railyai/raily-pin/published/keyring/case-3d/v2/bambu/stats.md

# Slice stats per plate (case v2)

Bambu Studio 02.06.00.51 CLI, system presets, 0.16 mm layers, Panchroma Matte (density 1.37). Grams come from the G-code extrusion: *part* = model + support, *purge* = the flush at each colour change + the prime tower (P2S and H2S flush in firmware, `M620.10`: their purge is the slicer's filament total minus the G-code extrusion). Times are the slicer estimate. Generated by `build_bambu.py stats`.

## X1 Carbon / X1E / X1

| Project | Plate | Time | Colour changes | White, part | Periwinkle, part | Support (in the part grams) | Purge | Total |
| --- | --- | --- | --- | --- | --- | --- | --- | --- |
| v1 | 1. LED coupon (print first) | 0 h 13 m | 0 | 0.0 g | 1.5 g | 0.0 g | 0.0 g | 2.0 g |
| v1 | 2. V1 case A (screws): tray + shelf | 0 h 59 m | 0 | 18.7 g | 0.0 g | 0.4 g | 0.0 g | 19.2 g |
| v1 | 3. V1 case A (screws): cover | 1 h 21 m | 0 | 0.0 g | 23.7 g | 11.4 g | 0.0 g | 24.2 g |
| v1 | 4. V1 case B (snap-fit): tray + shelf | 1 h 03 m | 0 | 18.9 g | 0.0 g | 0.4 g | 0.0 g | 19.4 g |
| v1 | 5. V1 case B (snap-fit): cover | 1 h 21 m | 0 | 0.0 g | 23.8 g | 11.3 g | 0.0 g | 24.3 g |
| v5 | 1. LED coupon (print first) | 0 h 13 m | 0 | 0.0 g | 1.5 g | 0.0 g | 0.0 g | 2.0 g |
| v5 | 2. V5 case A (screws): tray + shelf | 2 h 15 m | 50 | 19.5 g | 1.9 g | 0.4 g | 14.9 g | 36.7 g |
| v5 | 3. V5 case A (screws): cover | 1 h 21 m | 0 | 0.0 g | 23.7 g | 11.4 g | 0.0 g | 24.2 g |
| v5 | 4. V5 case B (snap-fit): tray + shelf | 2 h 17 m | 50 | 19.7 g | 1.9 g | 0.4 g | 14.9 g | 36.9 g |
| v5 | 5. V5 case B (snap-fit): cover | 1 h 21 m | 0 | 0.0 g | 23.8 g | 11.3 g | 0.0 g | 24.3 g |
| v5-batch | 1. V5 5 trays + 5 shelves (A) | 5 h 55 m | 50 | 91.0 g | 2.7 g | 2.2 g | 21.3 g | 115.5 g |
| v5-batch | 2. V5 5 covers (A) | 6 h 08 m | 0 | 0.0 g | 118.6 g | 56.9 g | 0.0 g | 119.1 g |
| v1-noams | 1. White: tray + shelf (A) | 0 h 59 m | 0 | 18.7 g | 0.0 g | 0.4 g | 0.0 g | 19.2 g |
| v1-noams | 2. Periwinkle: cover (A) | 1 h 21 m | 0 | 0.0 g | 23.7 g | 11.4 g | 0.0 g | 24.2 g |
| v1-noams | 3. White: tray + shelf (B) | 1 h 02 m | 0 | 18.9 g | 0.0 g | 0.4 g | 0.0 g | 19.4 g |
| v1-noams | 4. Periwinkle: cover (B) | 1 h 21 m | 0 | 0.0 g | 23.8 g | 11.3 g | 0.0 g | 24.3 g |

## P1S

| Project | Plate | Time | Colour changes | White, part | Periwinkle, part | Support (in the part grams) | Purge | Total |
| --- | --- | --- | --- | --- | --- | --- | --- | --- |
| v1 | 1. LED coupon (print first) | 0 h 11 m | 0 | 0.0 g | 1.5 g | 0.0 g | 0.0 g | 1.8 g |
| v1 | 2. V1 case A (screws): tray + shelf | 0 h 57 m | 0 | 18.7 g | 0.0 g | 0.4 g | 0.0 g | 19.1 g |
| v1 | 3. V1 case A (screws): cover | 1 h 18 m | 0 | 0.0 g | 23.7 g | 11.4 g | 0.0 g | 24.1 g |
| v1 | 4. V1 case B (snap-fit): tray + shelf | 1 h 00 m | 0 | 18.9 g | 0.0 g | 0.4 g | 0.0 g | 19.3 g |
| v1 | 5. V1 case B (snap-fit): cover | 1 h 19 m | 0 | 0.0 g | 23.8 g | 11.3 g | 0.0 g | 24.2 g |
| v5 | 1. LED coupon (print first) | 0 h 11 m | 0 | 0.0 g | 1.5 g | 0.0 g | 0.0 g | 1.8 g |
| v5 | 2. V5 case A (screws): tray + shelf | 2 h 13 m | 50 | 19.5 g | 1.9 g | 0.4 g | 14.9 g | 36.6 g |
| v5 | 3. V5 case A (screws): cover | 1 h 18 m | 0 | 0.0 g | 23.7 g | 11.4 g | 0.0 g | 24.1 g |
| v5 | 4. V5 case B (snap-fit): tray + shelf | 2 h 15 m | 50 | 19.7 g | 1.9 g | 0.4 g | 14.9 g | 36.8 g |
| v5 | 5. V5 case B (snap-fit): cover | 1 h 19 m | 0 | 0.0 g | 23.8 g | 11.3 g | 0.0 g | 24.2 g |
| v5-batch | 1. V5 5 trays + 5 shelves (A) | 5 h 53 m | 50 | 91.0 g | 2.7 g | 2.2 g | 21.3 g | 115.3 g |
| v5-batch | 2. V5 5 covers (A) | 6 h 05 m | 0 | 0.0 g | 118.6 g | 56.9 g | 0.0 g | 118.9 g |
| v1-noams | 1. White: tray + shelf (A) | 0 h 57 m | 0 | 18.7 g | 0.0 g | 0.4 g | 0.0 g | 19.1 g |
| v1-noams | 2. Periwinkle: cover (A) | 1 h 18 m | 0 | 0.0 g | 23.7 g | 11.4 g | 0.0 g | 24.1 g |
| v1-noams | 3. White: tray + shelf (B) | 1 h 00 m | 0 | 18.9 g | 0.0 g | 0.4 g | 0.0 g | 19.3 g |
| v1-noams | 4. Periwinkle: cover (B) | 1 h 19 m | 0 | 0.0 g | 23.8 g | 11.3 g | 0.0 g | 24.2 g |

## P1P

| Project | Plate | Time | Colour changes | White, part | Periwinkle, part | Support (in the part grams) | Purge | Total |
| --- | --- | --- | --- | --- | --- | --- | --- | --- |
| v1 | 1. LED coupon (print first) | 0 h 11 m | 0 | 0.0 g | 1.5 g | 0.0 g | 0.0 g | 1.8 g |
| v1 | 2. V1 case A (screws): tray + shelf | 0 h 58 m | 0 | 18.7 g | 0.0 g | 0.4 g | 0.0 g | 19.1 g |
| v1 | 3. V1 case A (screws): cover | 1 h 19 m | 0 | 0.0 g | 23.7 g | 11.4 g | 0.0 g | 24.1 g |
| v1 | 4. V1 case B (snap-fit): tray + shelf | 1 h 01 m | 0 | 18.9 g | 0.0 g | 0.4 g | 0.0 g | 19.3 g |
| v1 | 5. V1 case B (snap-fit): cover | 1 h 19 m | 0 | 0.0 g | 23.8 g | 11.3 g | 0.0 g | 24.2 g |
| v5 | 1. LED coupon (print first) | 0 h 11 m | 0 | 0.0 g | 1.5 g | 0.0 g | 0.0 g | 1.8 g |
| v5 | 2. V5 case A (screws): tray + shelf | 2 h 14 m | 50 | 19.5 g | 1.9 g | 0.4 g | 14.9 g | 36.6 g |
| v5 | 3. V5 case A (screws): cover | 1 h 19 m | 0 | 0.0 g | 23.7 g | 11.4 g | 0.0 g | 24.1 g |
| v5 | 4. V5 case B (snap-fit): tray + shelf | 2 h 16 m | 50 | 19.7 g | 1.9 g | 0.4 g | 14.9 g | 36.8 g |
| v5 | 5. V5 case B (snap-fit): cover | 1 h 19 m | 0 | 0.0 g | 23.8 g | 11.3 g | 0.0 g | 24.2 g |
| v5-batch | 1. V5 5 trays + 5 shelves (A) | 5 h 53 m | 50 | 91.0 g | 2.7 g | 2.2 g | 21.3 g | 115.3 g |
| v5-batch | 2. V5 5 covers (A) | 6 h 05 m | 0 | 0.0 g | 118.6 g | 56.9 g | 0.0 g | 118.9 g |
| v1-noams | 1. White: tray + shelf (A) | 0 h 58 m | 0 | 18.7 g | 0.0 g | 0.4 g | 0.0 g | 19.1 g |
| v1-noams | 2. Periwinkle: cover (A) | 1 h 19 m | 0 | 0.0 g | 23.7 g | 11.4 g | 0.0 g | 24.1 g |
| v1-noams | 3. White: tray + shelf (B) | 1 h 01 m | 0 | 18.9 g | 0.0 g | 0.4 g | 0.0 g | 19.3 g |
| v1-noams | 4. Periwinkle: cover (B) | 1 h 19 m | 0 | 0.0 g | 23.8 g | 11.3 g | 0.0 g | 24.2 g |

## P2S

| Project | Plate | Time | Colour changes | White, part | Periwinkle, part | Support (in the part grams) | Purge | Total |
| --- | --- | --- | --- | --- | --- | --- | --- | --- |
| v1 | 1. LED coupon (print first) | 0 h 11 m | 0 | 0.0 g | 1.6 g | 0.0 g | 0.0 g | 1.6 g |
| v1 | 2. V1 case A (screws) | 2 h 13 m | 2 | 19.3 g | 24.5 g | 12.2 g | 0.7 g | 44.5 g |
| v1 | 3. V1 case B (snap-fit) | 2 h 16 m | 2 | 19.5 g | 24.6 g | 12.1 g | 0.7 g | 44.8 g |
| v5 | 1. LED coupon (print first) | 0 h 11 m | 0 | 0.0 g | 1.6 g | 0.0 g | 0.0 g | 1.6 g |
| v5 | 2. V5 case A (screws) | 3 h 19 m | 52 | 18.7 g | 25.0 g | 12.2 g | 18.4 g | 62.2 g |
| v5 | 3. V5 case B (snap-fit) | 3 h 22 m | 52 | 18.9 g | 25.1 g | 12.1 g | 18.4 g | 62.5 g |
| v5-batch | 1. V5 5 trays + 5 shelves (A) | 5 h 44 m | 50 | 93.8 g | 2.8 g | 2.2 g | 21.3 g | 117.8 g |
| v5-batch | 2. V5 5 covers (A) | 6 h 07 m | 0 | 0.0 g | 122.2 g | 58.6 g | 0.0 g | 122.3 g |
| v1-noams | 1. White: tray + shelf (A) | 0 h 58 m | 0 | 19.3 g | 0.0 g | 0.5 g | 0.0 g | 19.3 g |
| v1-noams | 2. Periwinkle: cover (A) | 1 h 19 m | 0 | 0.0 g | 24.5 g | 11.7 g | 0.0 g | 24.5 g |
| v1-noams | 3. White: tray + shelf (B) | 1 h 01 m | 0 | 19.5 g | 0.0 g | 0.5 g | 0.0 g | 19.6 g |
| v1-noams | 4. Periwinkle: cover (B) | 1 h 19 m | 0 | 0.0 g | 24.6 g | 11.6 g | 0.0 g | 24.6 g |

## A1

| Project | Plate | Time | Colour changes | White, part | Periwinkle, part | Support (in the part grams) | Purge | Total |
| --- | --- | --- | --- | --- | --- | --- | --- | --- |
| v1 | 1. LED coupon (print first) | 0 h 12 m | 0 | 0.0 g | 1.5 g | 0.0 g | 0.0 g | 1.9 g |
| v1 | 2. V1 case A (screws) | 2 h 14 m | 2 | 18.8 g | 23.8 g | 11.8 g | 0.4 g | 43.4 g |
| v1 | 3. V1 case B (snap-fit) | 2 h 17 m | 2 | 19.0 g | 23.9 g | 11.7 g | 0.4 g | 43.7 g |
| v5 | 1. LED coupon (print first) | 0 h 12 m | 0 | 0.0 g | 1.5 g | 0.0 g | 0.0 g | 1.9 g |
| v5 | 2. V5 case A (screws) | 3 h 24 m | 52 | 19.9 g | 26.0 g | 11.8 g | 11.1 g | 57.4 g |
| v5 | 3. V5 case B (snap-fit) | 3 h 26 m | 52 | 20.1 g | 26.1 g | 11.7 g | 11.1 g | 57.7 g |
| v5-batch | 1. V5 5 trays + 5 shelves (A) | 5 h 56 m | 50 | 91.0 g | 2.6 g | 2.2 g | 19.1 g | 113.1 g |
| v5-batch | 2. V5 5 covers (A) | 6 h 14 m | 0 | 0.0 g | 118.6 g | 56.9 g | 0.0 g | 119.0 g |
| v1-noams | 1. White: tray + shelf (A) | 0 h 59 m | 0 | 18.7 g | 0.0 g | 0.4 g | 0.0 g | 19.1 g |
| v1-noams | 2. Periwinkle: cover (A) | 1 h 19 m | 0 | 0.0 g | 23.7 g | 11.4 g | 0.0 g | 24.1 g |
| v1-noams | 3. White: tray + shelf (B) | 1 h 02 m | 0 | 18.9 g | 0.0 g | 0.4 g | 0.0 g | 19.3 g |
| v1-noams | 4. Periwinkle: cover (B) | 1 h 20 m | 0 | 0.0 g | 23.8 g | 11.3 g | 0.0 g | 24.2 g |

## A1 mini

| Project | Plate | Time | Colour changes | White, part | Periwinkle, part | Support (in the part grams) | Purge | Total |
| --- | --- | --- | --- | --- | --- | --- | --- | --- |
| v1 | 1. LED coupon (print first) | 0 h 11 m | 0 | 0.0 g | 1.5 g | 0.0 g | 0.0 g | 1.9 g |
| v1 | 2. V1 case A (screws): tray + shelf | 0 h 59 m | 0 | 18.7 g | 0.0 g | 0.4 g | 0.0 g | 19.1 g |
| v1 | 3. V1 case A (screws): cover | 1 h 22 m | 0 | 0.0 g | 23.7 g | 11.4 g | 0.0 g | 24.1 g |
| v1 | 4. V1 case B (snap-fit): tray + shelf | 1 h 03 m | 0 | 18.9 g | 0.0 g | 0.4 g | 0.0 g | 19.3 g |
| v1 | 5. V1 case B (snap-fit): cover | 1 h 22 m | 0 | 0.0 g | 23.8 g | 11.3 g | 0.0 g | 24.2 g |
| v5 | 1. LED coupon (print first) | 0 h 11 m | 0 | 0.0 g | 1.5 g | 0.0 g | 0.0 g | 1.9 g |
| v5 | 2. V5 case A (screws): tray + shelf | 2 h 18 m | 50 | 19.8 g | 2.1 g | 0.4 g | 10.7 g | 32.9 g |
| v5 | 3. V5 case A (screws): cover | 1 h 22 m | 0 | 0.0 g | 23.7 g | 11.4 g | 0.0 g | 24.1 g |
| v5 | 4. V5 case B (snap-fit): tray + shelf | 2 h 20 m | 50 | 20.0 g | 2.1 g | 0.4 g | 10.7 g | 33.1 g |
| v5 | 5. V5 case B (snap-fit): cover | 1 h 22 m | 0 | 0.0 g | 23.8 g | 11.3 g | 0.0 g | 24.2 g |
| v5-batch | 1. V5 3 trays + 3 shelves (A) | 4 h 24 m | 50 | 54.6 g | 1.5 g | 1.3 g | 19.2 g | 75.7 g |
| v5-batch | 2. V5 3 covers (A) | 3 h 55 m | 0 | 0.0 g | 71.2 g | 34.1 g | 0.0 g | 71.5 g |
| v1-noams | 1. White: tray + shelf (A) | 0 h 59 m | 0 | 18.7 g | 0.0 g | 0.4 g | 0.0 g | 19.1 g |
| v1-noams | 2. Periwinkle: cover (A) | 1 h 22 m | 0 | 0.0 g | 23.7 g | 11.4 g | 0.0 g | 24.1 g |
| v1-noams | 3. White: tray + shelf (B) | 1 h 03 m | 0 | 18.9 g | 0.0 g | 0.4 g | 0.0 g | 19.3 g |
| v1-noams | 4. Periwinkle: cover (B) | 1 h 22 m | 0 | 0.0 g | 23.8 g | 11.3 g | 0.0 g | 24.2 g |

## H2D

| Project | Plate | Time | Colour changes | White, part | Periwinkle, part | Support (in the part grams) | Purge | Total |
| --- | --- | --- | --- | --- | --- | --- | --- | --- |
| v1 | 1. LED coupon (print first) | 0 h 10 m | 0 | 0.0 g | 1.5 g | 0.0 g | 0.0 g | 1.7 g |
| v1 | 2. V1 case A (screws) | 2 h 12 m | 0 | 18.7 g | 23.7 g | 11.8 g | 0.0 g | 42.6 g |
| v1 | 3. V1 case B (snap-fit) | 2 h 15 m | 0 | 18.9 g | 23.8 g | 11.7 g | 0.0 g | 42.9 g |
| v5 | 1. LED coupon (print first) | 0 h 10 m | 0 | 0.0 g | 1.5 g | 0.0 g | 0.0 g | 1.7 g |
| v5 | 2. V5 case A (screws) | 2 h 19 m | 0 | 18.2 g | 24.3 g | 11.8 g | 0.0 g | 42.6 g |
| v5 | 3. V5 case B (snap-fit) | 2 h 22 m | 0 | 18.4 g | 24.4 g | 11.7 g | 0.0 g | 42.9 g |
| v5-batch | 1. V5 5 trays + 5 shelves (A) | 4 h 53 m | 0 | 90.9 g | 2.7 g | 2.2 g | 4.0 g | 97.8 g |
| v5-batch | 2. V5 5 covers (A) | 6 h 11 m | 0 | 0.0 g | 118.6 g | 56.9 g | 0.0 g | 118.8 g |
| v1-noams | 1. White: tray + shelf (A) | 0 h 58 m | 0 | 18.7 g | 0.0 g | 0.4 g | 0.0 g | 18.9 g |
| v1-noams | 2. Periwinkle: cover (A) | 1 h 19 m | 0 | 0.0 g | 23.7 g | 11.4 g | 0.0 g | 23.9 g |
| v1-noams | 3. White: tray + shelf (B) | 1 h 01 m | 0 | 18.9 g | 0.0 g | 0.4 g | 0.0 g | 19.1 g |
| v1-noams | 4. Periwinkle: cover (B) | 1 h 19 m | 0 | 0.0 g | 23.8 g | 11.3 g | 0.0 g | 24.0 g |

## H2S

| Project | Plate | Time | Colour changes | White, part | Periwinkle, part | Support (in the part grams) | Purge | Total |
| --- | --- | --- | --- | --- | --- | --- | --- | --- |
| v1 | 1. LED coupon (print first) | 0 h 10 m | 0 | 0.0 g | 1.5 g | 0.0 g | 0.0 g | 1.7 g |
| v1 | 2. V1 case A (screws) | 2 h 11 m | 2 | 18.7 g | 23.7 g | 11.8 g | 0.6 g | 43.3 g |
| v1 | 3. V1 case B (snap-fit) | 2 h 15 m | 2 | 18.9 g | 23.8 g | 11.7 g | 0.7 g | 43.6 g |
| v5 | 1. LED coupon (print first) | 0 h 10 m | 0 | 0.0 g | 1.5 g | 0.0 g | 0.0 g | 1.7 g |
| v5 | 2. V5 case A (screws) | 3 h 17 m | 52 | 18.2 g | 24.3 g | 11.8 g | 20.8 g | 63.5 g |
| v5 | 3. V5 case B (snap-fit) | 3 h 20 m | 52 | 18.4 g | 24.4 g | 11.7 g | 20.8 g | 63.8 g |
| v5-batch | 1. V5 5 trays + 5 shelves (A) | 5 h 42 m | 50 | 91.0 g | 2.7 g | 2.2 g | 22.2 g | 116.1 g |
| v5-batch | 2. V5 5 covers (A) | 6 h 06 m | 0 | 0.0 g | 118.6 g | 56.9 g | 0.0 g | 118.8 g |
| v1-noams | 1. White: tray + shelf (A) | 0 h 56 m | 0 | 18.7 g | 0.0 g | 0.4 g | 0.0 g | 18.9 g |
| v1-noams | 2. Periwinkle: cover (A) | 1 h 18 m | 0 | 0.0 g | 23.7 g | 11.4 g | 0.0 g | 23.9 g |
| v1-noams | 3. White: tray + shelf (B) | 1 h 00 m | 0 | 18.9 g | 0.0 g | 0.4 g | 0.0 g | 19.2 g |
| v1-noams | 4. Periwinkle: cover (B) | 1 h 18 m | 0 | 0.0 g | 23.8 g | 11.3 g | 0.0 g | 24.0 g |
