railyai/raily-pin/guide/art/overview-fill.png

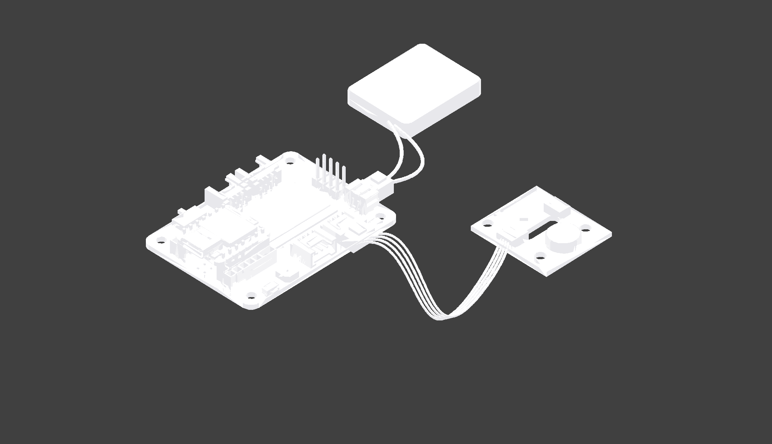
guide/art/overview-fill.png
