railyai/raily-pin/published/keyring/case-3d/bambu/preview/a1m-v5-batch-plate1.png

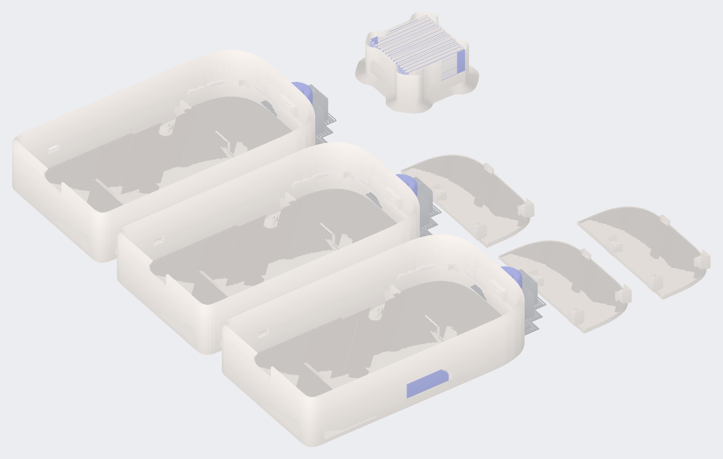
published/keyring/case-3d/bambu/preview/a1m-v5-batch-plate1.png
