railyai/raily-pin/published/keyring/case-3d/bambu/preview/h2d-v5-plate2.png

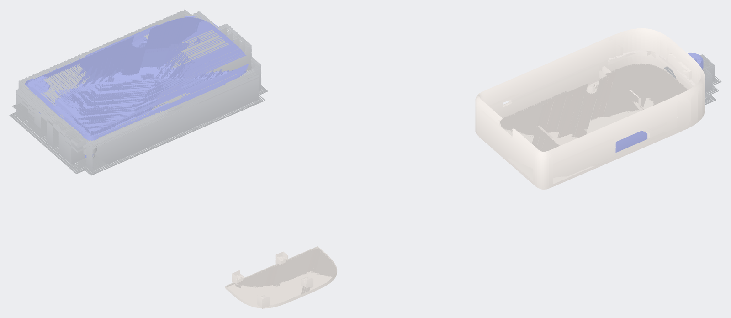
published/keyring/case-3d/bambu/preview/h2d-v5-plate2.png
