railyai/raily-pin/published/keyring/case-3d/bambu/preview/v1-plate1.png

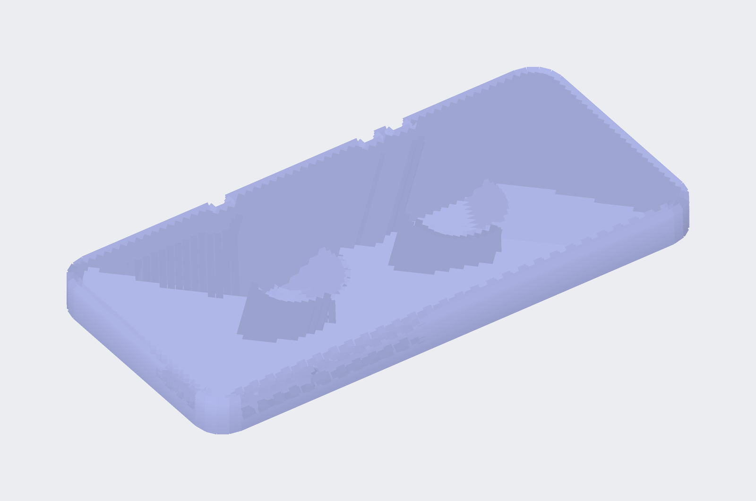
published/keyring/case-3d/bambu/preview/v1-plate1.png
