railyai/raily-pin/published/keyring/case-3d/v2/bambu/preview/a1m-v1-noams-plate2.png

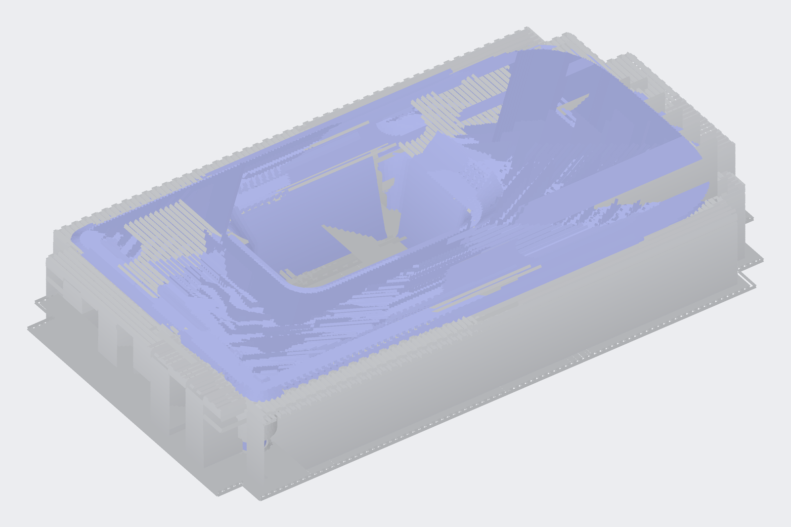
published/keyring/case-3d/v2/bambu/preview/a1m-v1-noams-plate2.png
