railyai/raily-pin/published/keyring/case-3d/v2/line-art/case-v2-iso.png

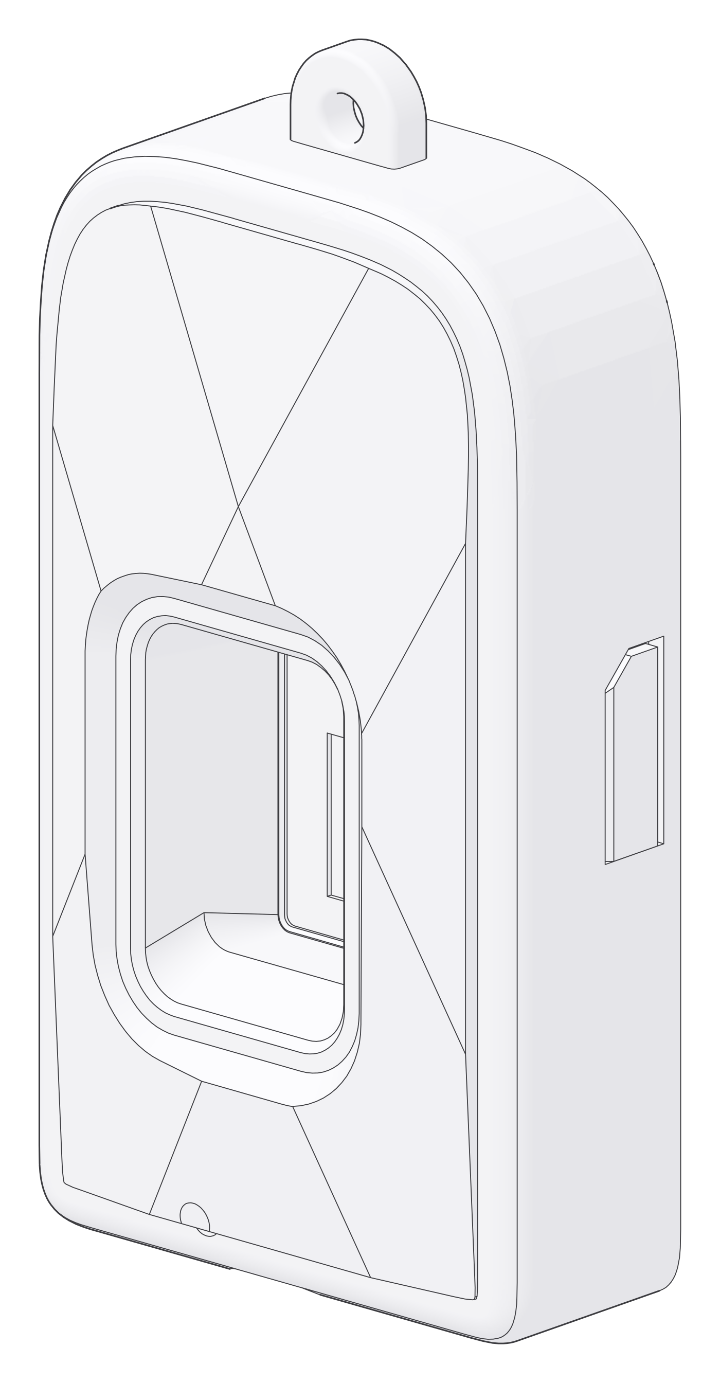
published/keyring/case-3d/v2/line-art/case-v2-iso.png
