railyai/raily-pin/published/keyring/case-3d/v2/line-art/case-v2-window-across.png

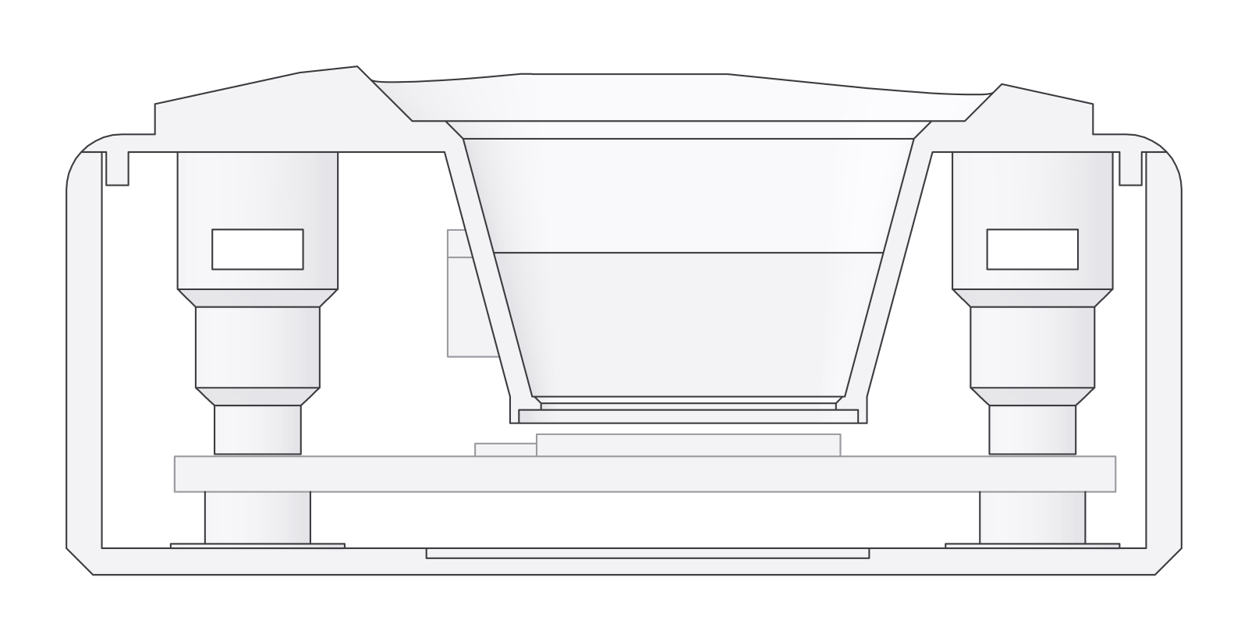
published/keyring/case-3d/v2/line-art/case-v2-window-across.png
