railyai/raily-pin/published/keyring/case-3d/v2/line-art/tab-v2-across.png

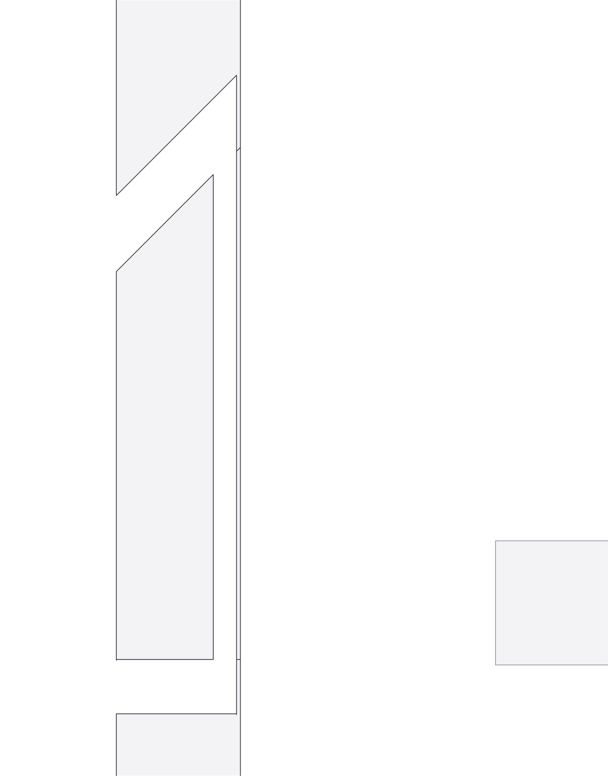
published/keyring/case-3d/v2/line-art/tab-v2-across.png
