railyai/raily-pin/published/keyring/case-3d/v2/line-art/usb-v2-usb-end.png

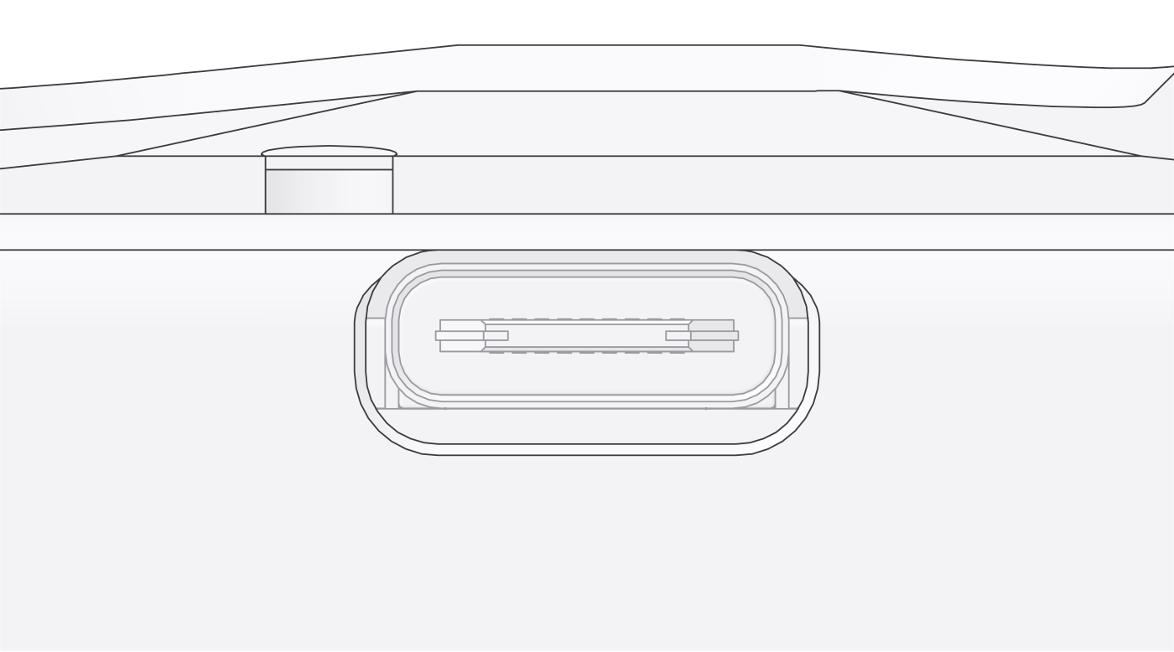
published/keyring/case-3d/v2/line-art/usb-v2-usb-end.png
