railyai/raily-pin/published/keyring/case-3d/v2/renders/render-v2-v1-front.png

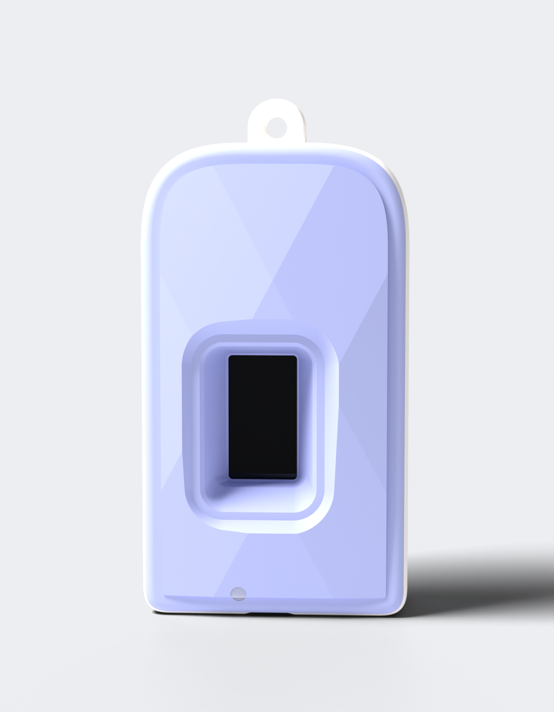
published/keyring/case-3d/v2/renders/render-v2-v1-front.png
