railyai/raily-pin/published/keyring/case/guide-figures/overview.png

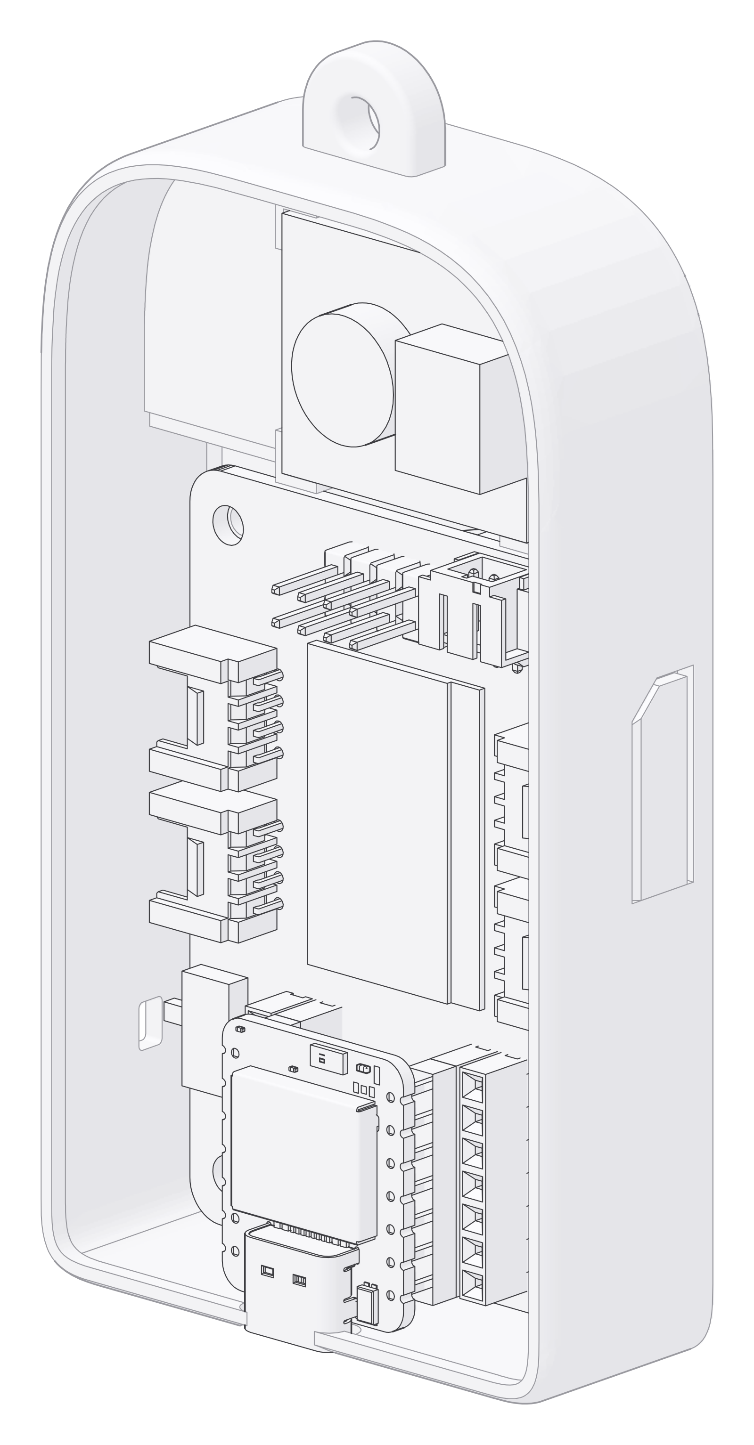
published/keyring/case/guide-figures/overview.png
