railyai/raily-pin/published/keyring/case/line-art/case-front.png

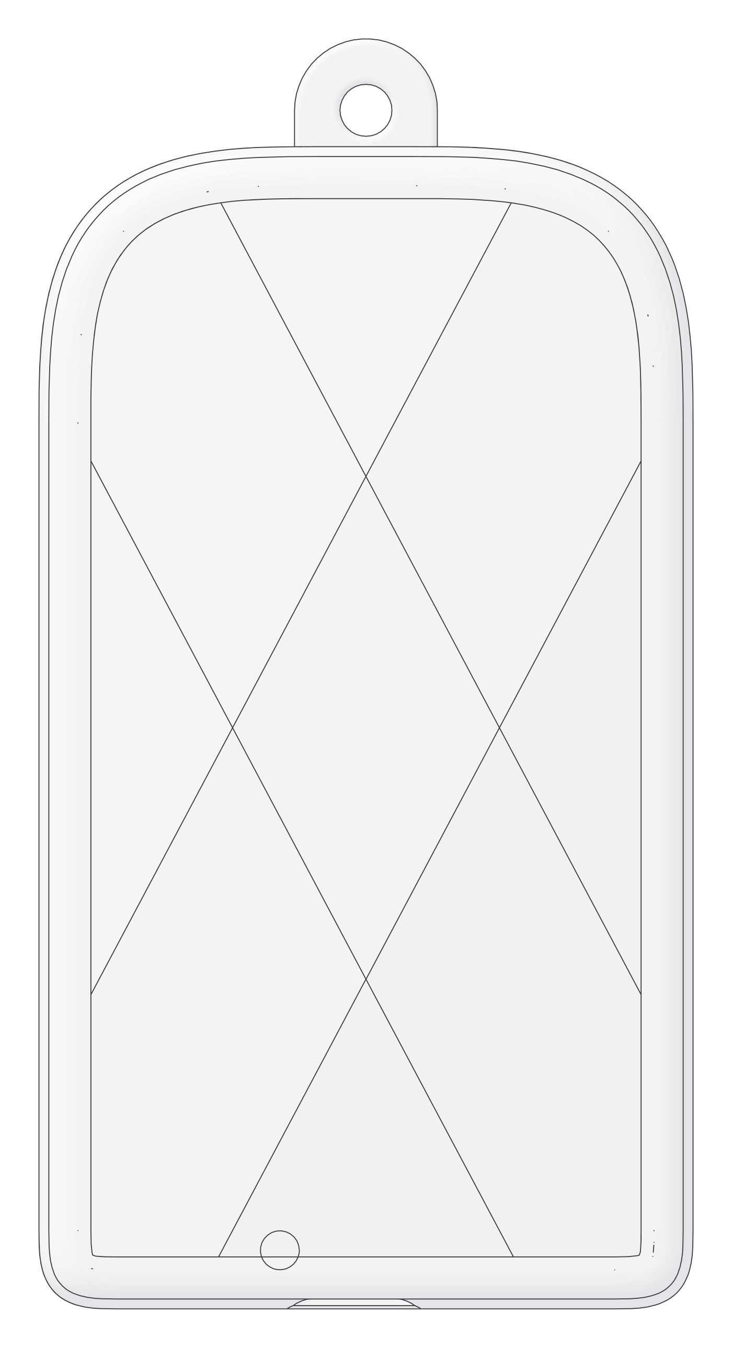
published/keyring/case/line-art/case-front.png
