railyai/raily-pin/published/keyring/case/line-art/case-iso.png

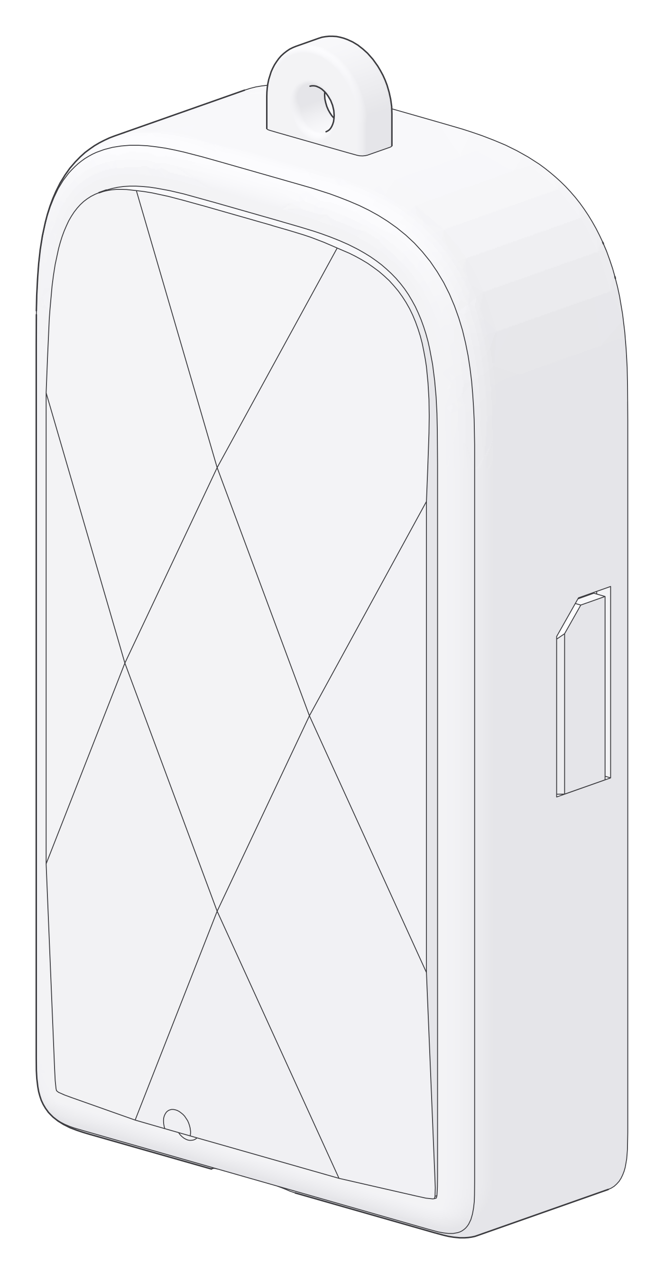
published/keyring/case/line-art/case-iso.png
