railyai/raily-pin/published/keyring/case/line-art/tab-across-nub.png

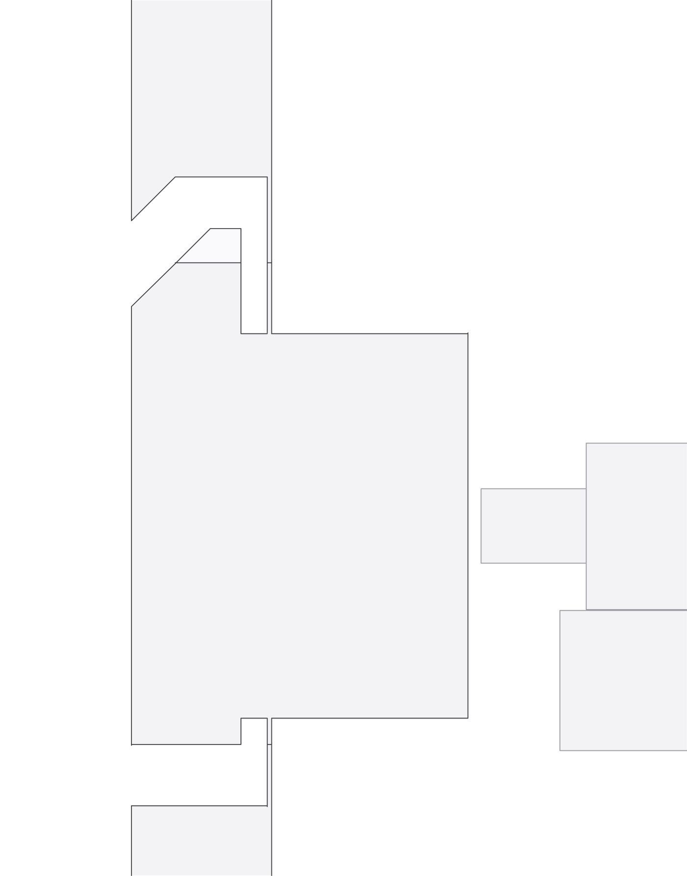
published/keyring/case/line-art/tab-across-nub.png
