railyai/raily-pin/published/keyring/case/line-art/tab-before-after.png

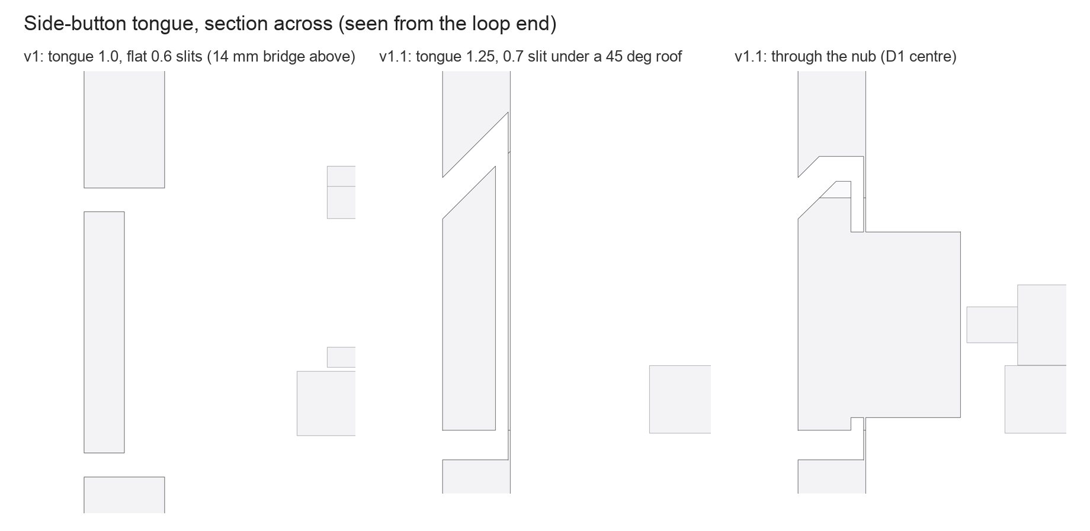
published/keyring/case/line-art/tab-before-after.png
