railyai/raily-pin/published/keyring/case/line-art/usb-before-after.png

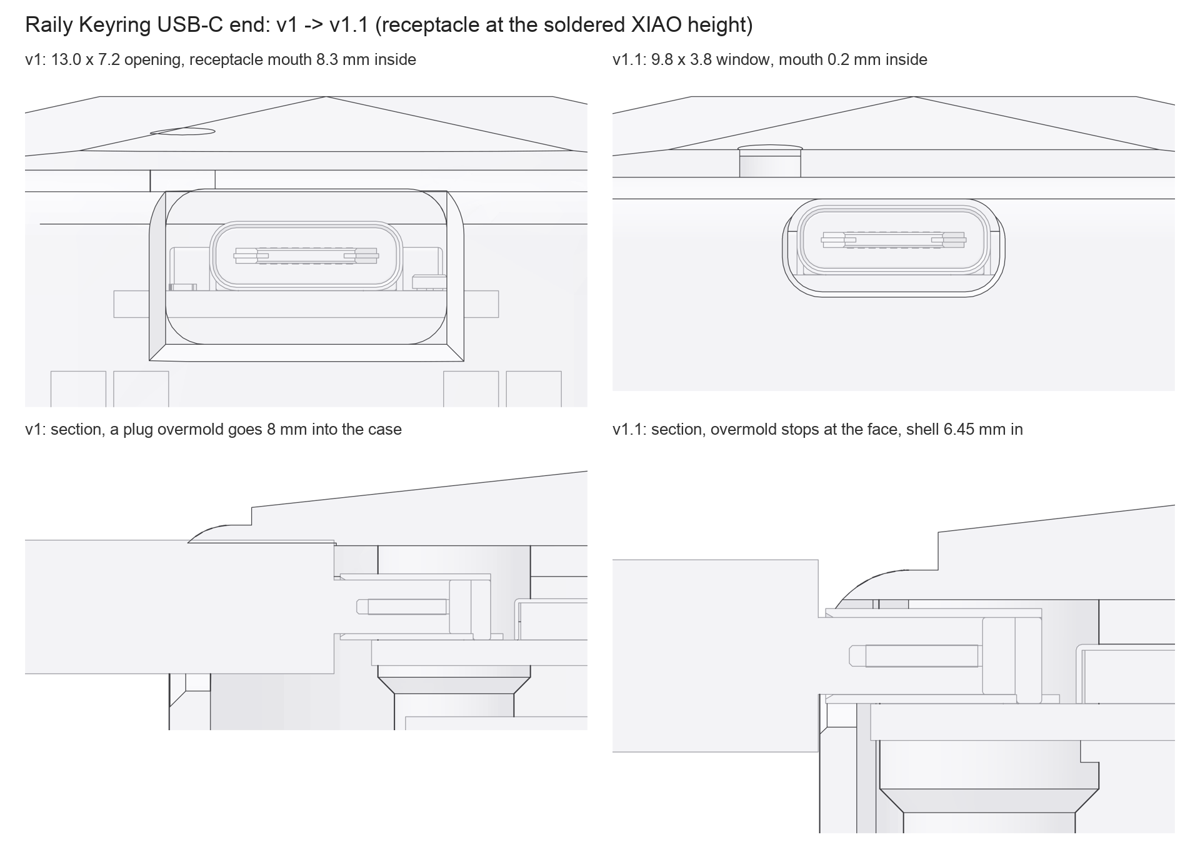
published/keyring/case/line-art/usb-before-after.png
