railyai/raily-pin/published/keyring/case/renders/render-led-v1-periwinkle04.png

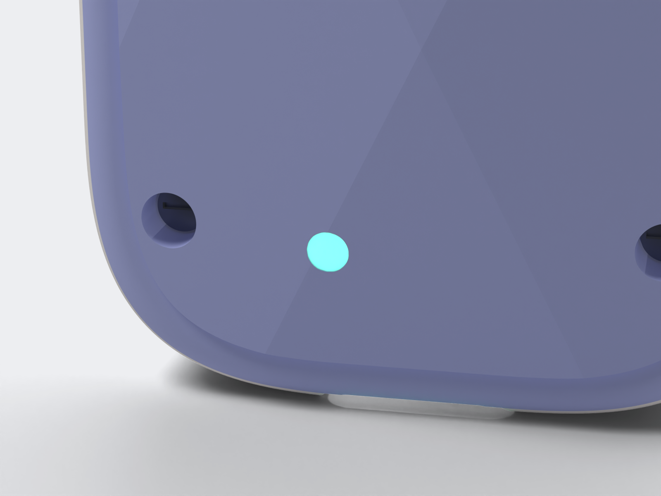
published/keyring/case/renders/render-led-v1-periwinkle04.png
