railyai/raily-pin/published/keyring/case/renders/render-v1-front.png

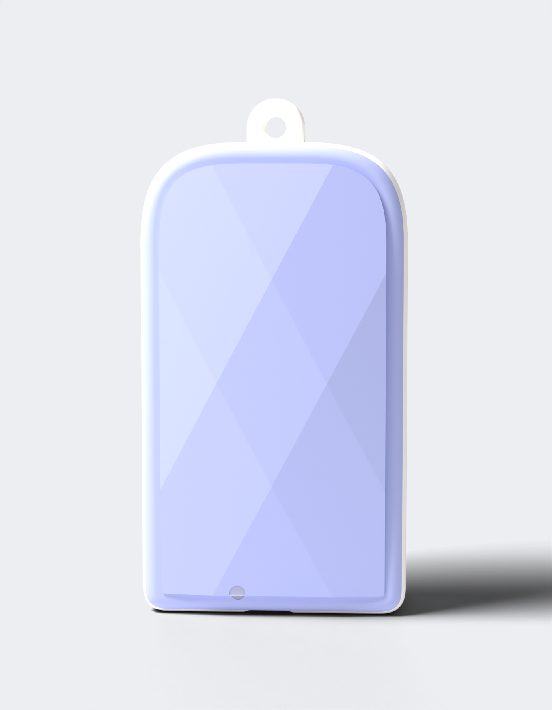
published/keyring/case/renders/render-v1-front.png
