railyai/raily-pin/published/keyring/case/renders/render-v1-iso.png

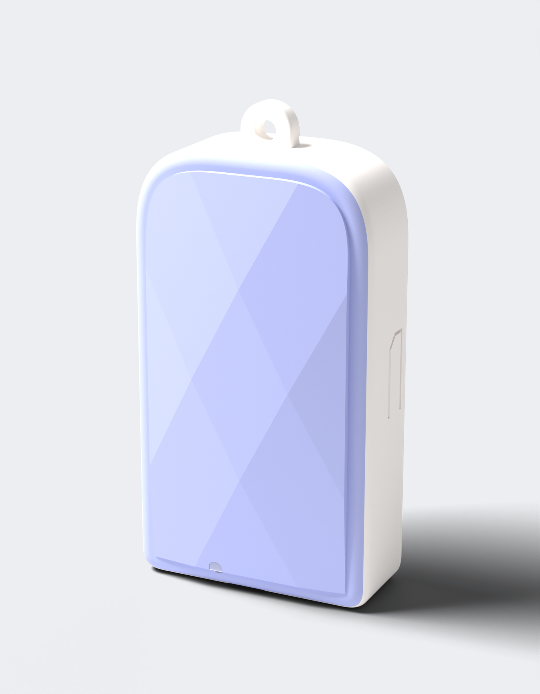
published/keyring/case/renders/render-v1-iso.png
