railyai/raily-pin/published/keyring/case/renders/sheet-final.png

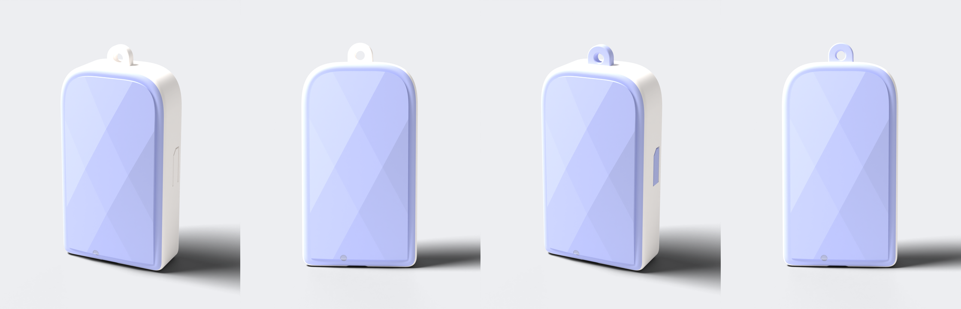
published/keyring/case/renders/sheet-final.png
