railyai/raily-pin/published/keyring/case-3d/v2/print-flat/closure-b/keyring-cover-led.stl

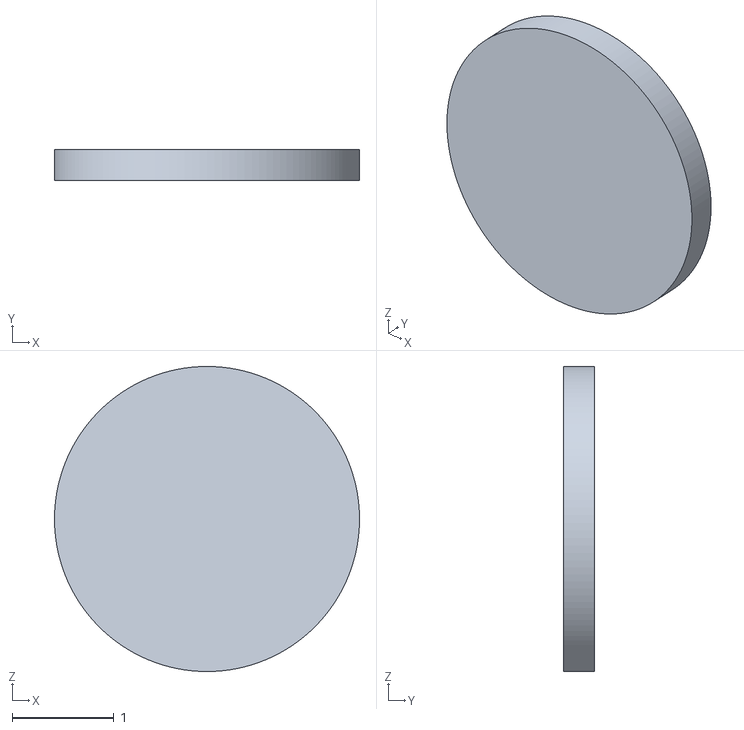
[picture p51: CAD file, 2026-10-08]
published/keyring/case-3d/v2/print-flat/closure-b/keyring-cover-led.stl
3.00 x 0.3 x 3.00
