railyai/raily-pin/published/keyring/case-3d/v2/print-flat/keyring-tray-loop.stl

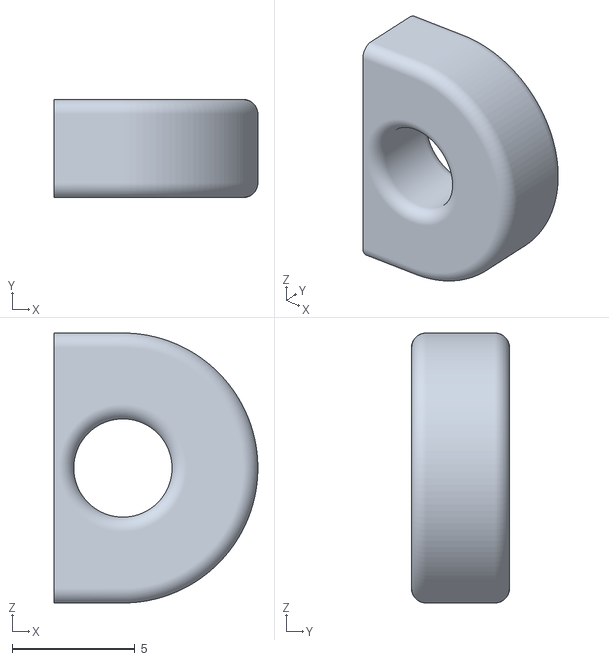
[picture p52: CAD file, 2026-10-08]
published/keyring/case-3d/v2/print-flat/keyring-tray-loop.stl
8.30 x 4.00 x 11.0
