railyai/raily-pin/published/keyring/case-3d/v2/print/closure-b/keyring-cover-cover.stl

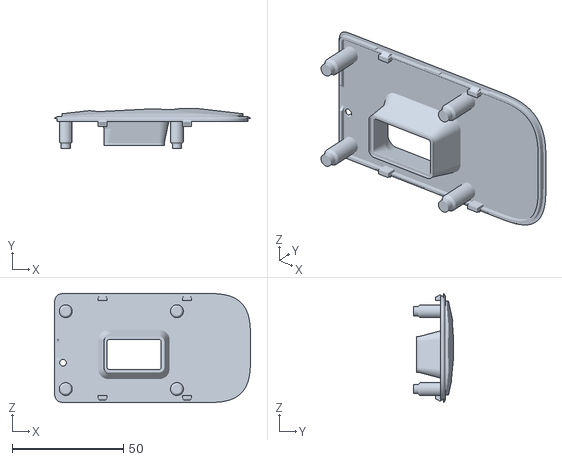
[picture p53: CAD file, 2026-10-08]
published/keyring/case-3d/v2/print/closure-b/keyring-cover-cover.stl
88.1 x 18.2 x 49.0
