railyai/raily-pin/guide/cad/xiao-pcb-clean.step

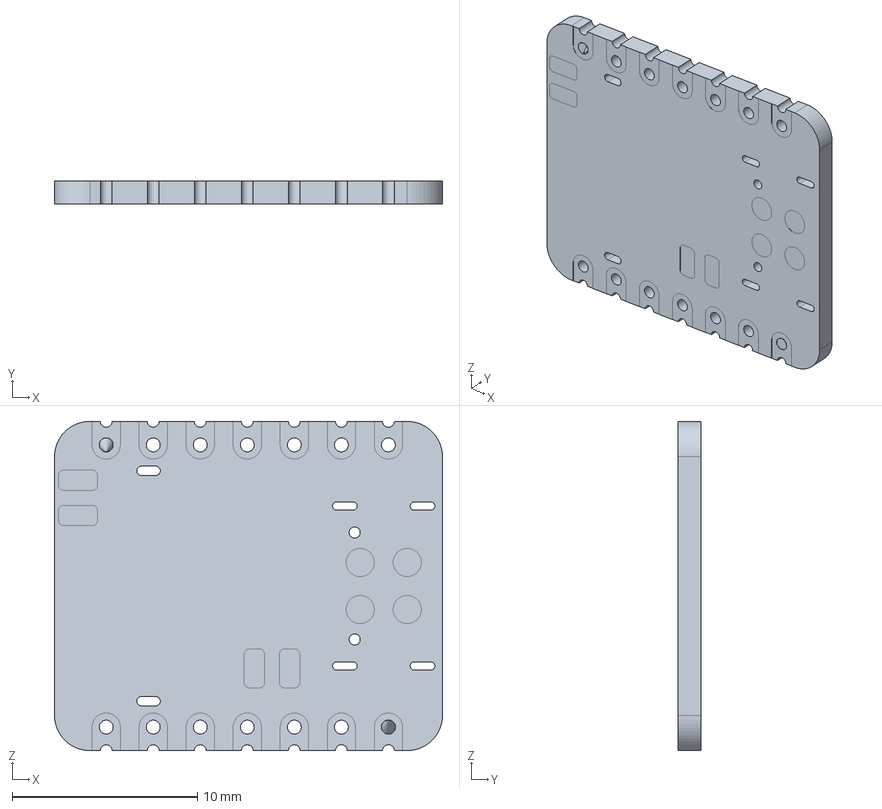
[picture p54: CAD file, 2026-10-08]
guide/cad/xiao-pcb-clean.step
21.0 x 1.24 x 17.8 mm
