railyai/raily-pin/published/keyring/case-3d/bambu/printers/a1/v5.3mf

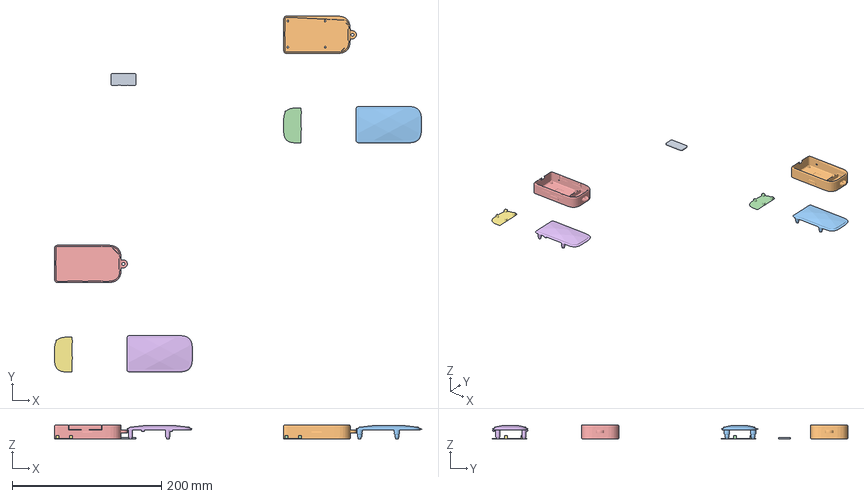
[picture p55: CAD file, 2026-10-08]
published/keyring/case-3d/bambu/printers/a1/v5.3mf
492.1 x 477.3 x 19.3 mm
led-coupon_1
assemble_1 x 2
assemble_2 x 2
assemble_3 x 2
