railyai/raily-pin/published/keyring/case-3d/bambu/printers/h2d/v1-noams.3mf

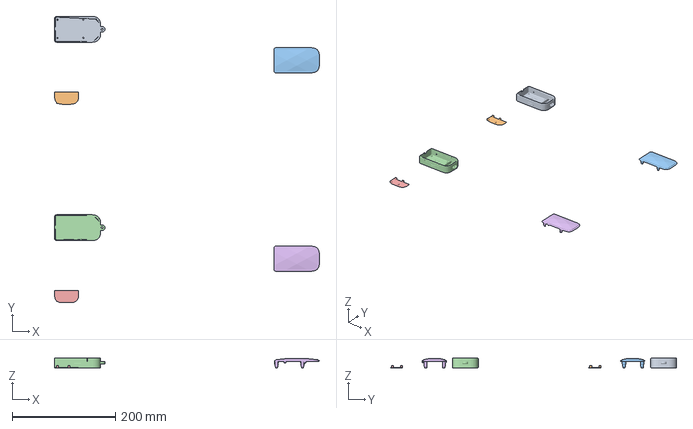
[picture p56: CAD file, 2026-10-08]
published/keyring/case-3d/bambu/printers/h2d/v1-noams.3mf
512.8 x 554.4 x 19.3 mm
assemble_1 x 4
assemble_2 x 2
