railyai/raily-pin/published/keyring/case-3d/bambu/printers/h2s/v5-batch.3mf

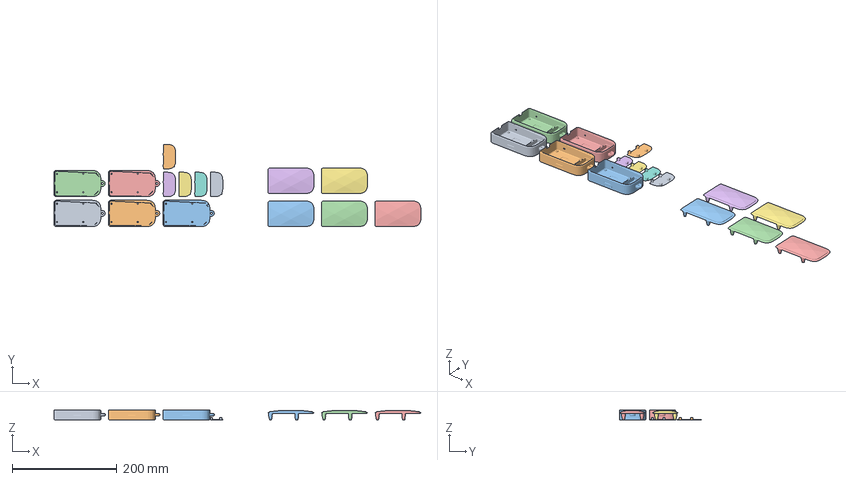
[picture p57: CAD file, 2026-10-08]
published/keyring/case-3d/bambu/printers/h2s/v5-batch.3mf
699.9 x 156.8 x 19.3 mm
assemble_1 x 2
assemble_2 x 2
assemble_3 x 2
assemble_4 x 2
assemble_5 x 2
assemble_6
assemble_7
assemble_8
assemble_9
assemble_10
