railyai/raily-pin/published/keyring/case-3d/bambu/printers/p2s/v1-noams.3mf

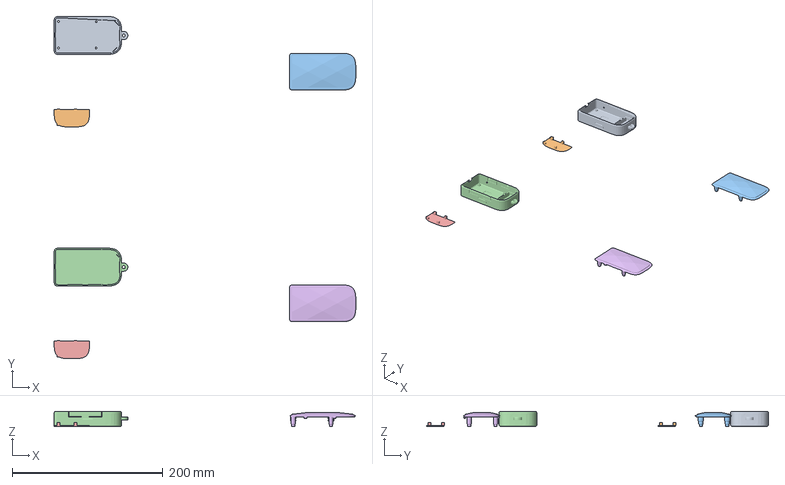
[picture p59: CAD file, 2026-10-08]
published/keyring/case-3d/bambu/printers/p2s/v1-noams.3mf
400.0 x 453.6 x 19.3 mm
assemble_1 x 4
assemble_2 x 2
