railyai/raily-pin/published/keyring/case-3d/checkpoint-a/A2-shelf-17.2b-A1mini.gcode.3mf

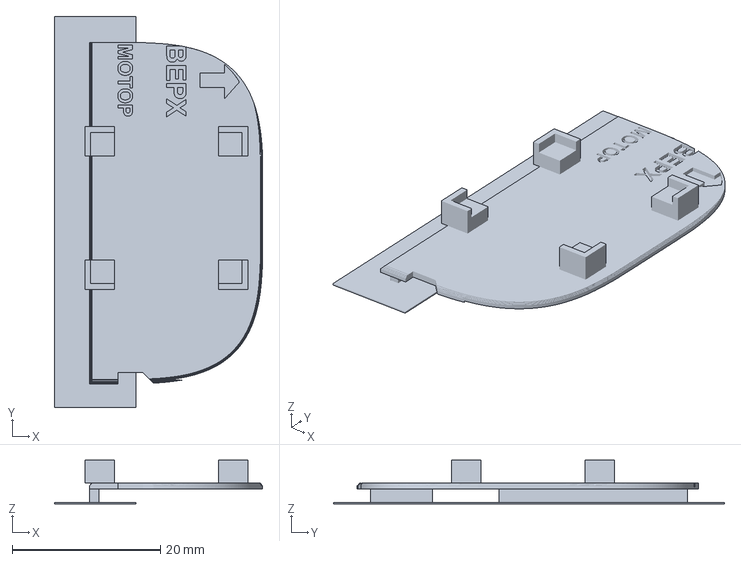
[picture p60: CAD file, 2026-10-08]
published/keyring/case-3d/checkpoint-a/A2-shelf-17.2b-A1mini.gcode.3mf
28.1 x 52.7 x 5.90 mm
