railyai/raily-pin/published/keyring/case-3d/print/closure-b/keyring-cover-led.stl

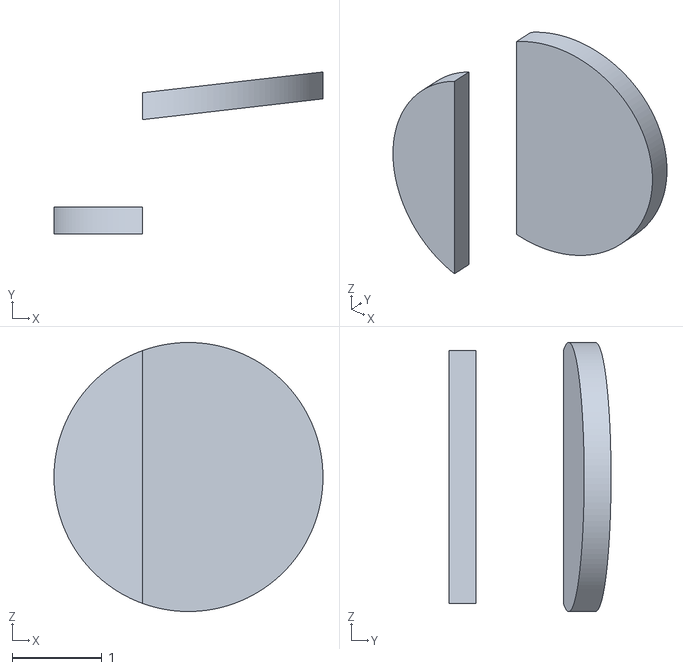
[picture p61: CAD file, 2026-10-08]
published/keyring/case-3d/print/closure-b/keyring-cover-led.stl
3.00 x 1.81 x 3.00
