railyai/raily-pin/published/keyring/case-3d/print/keyring-tray-tray.stl

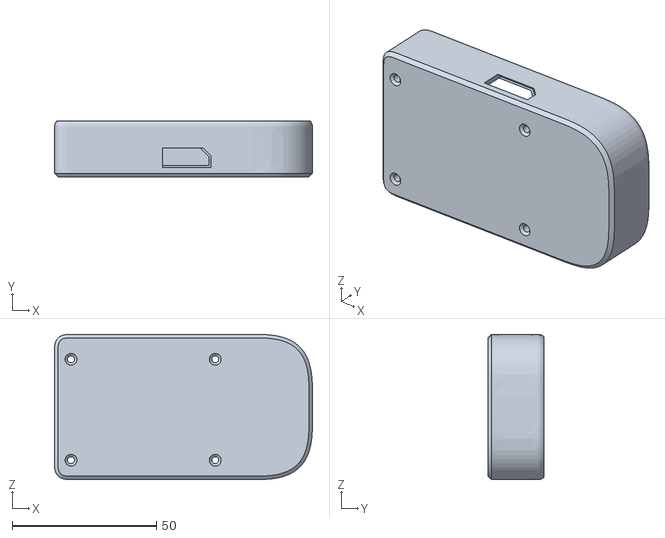
[picture p62: CAD file, 2026-10-08]
published/keyring/case-3d/print/keyring-tray-tray.stl
89.5 x 19.3 x 50.4
