railyai/raily-pin/published/keyring/case-3d/print/shelf-variants/shelf-D.stl

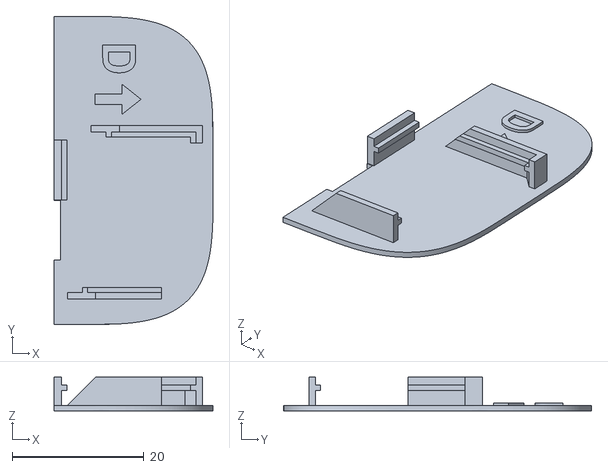
[picture p63: CAD file, 2026-10-08]
published/keyring/case-3d/print/shelf-variants/shelf-D.stl
24.1 x 46.8 x 5.10
