railyai/raily-pin/published/keyring/case-3d/v2/bambu/printers/p1s/v5.3mf

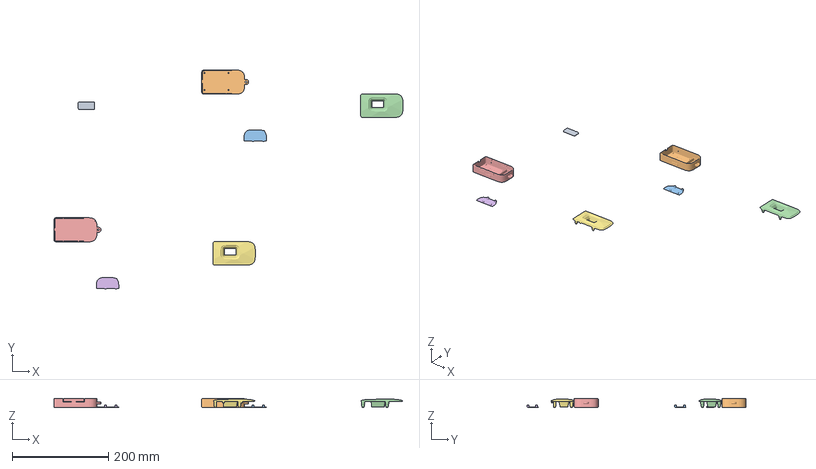
[picture p66: CAD file, 2026-10-08]
published/keyring/case-3d/v2/bambu/printers/p1s/v5.3mf
725.8 x 455.6 x 19.1 mm
led-coupon_1
assemble_1 x 4
assemble_2 x 2
