railyai/raily-pin/published/keyring/case-3d/v2/bambu/printers/p2s/v1-noams.3mf

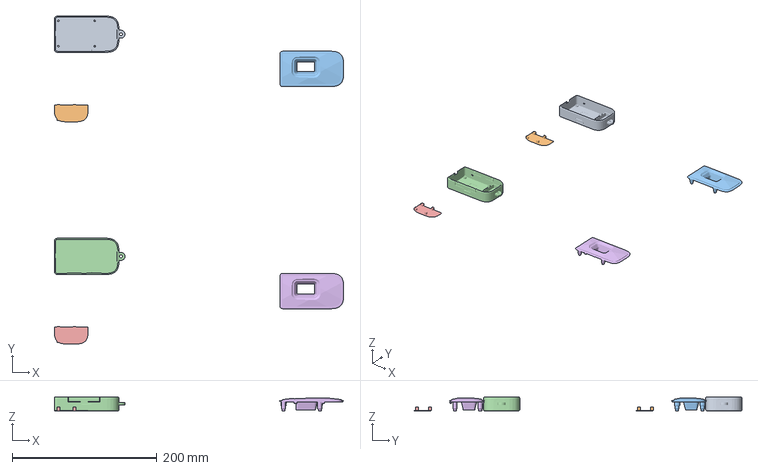
[picture p67: CAD file, 2026-10-08]
published/keyring/case-3d/v2/bambu/printers/p2s/v1-noams.3mf
400.1 x 453.6 x 19.1 mm
assemble_1 x 4
assemble_2 x 2
