railyai/raily-pin/published/keyring/case-3d/v2/print/keyring-shelf-shelf.stl

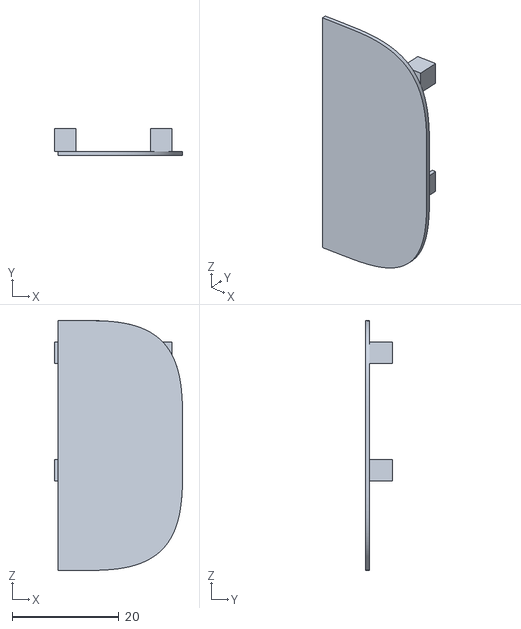
[picture p68: CAD file, 2026-10-08]
published/keyring/case-3d/v2/print/keyring-shelf-shelf.stl
24.0 x 5.10 x 46.8
