railyai/raily-pin/guide/cad/expansion.step

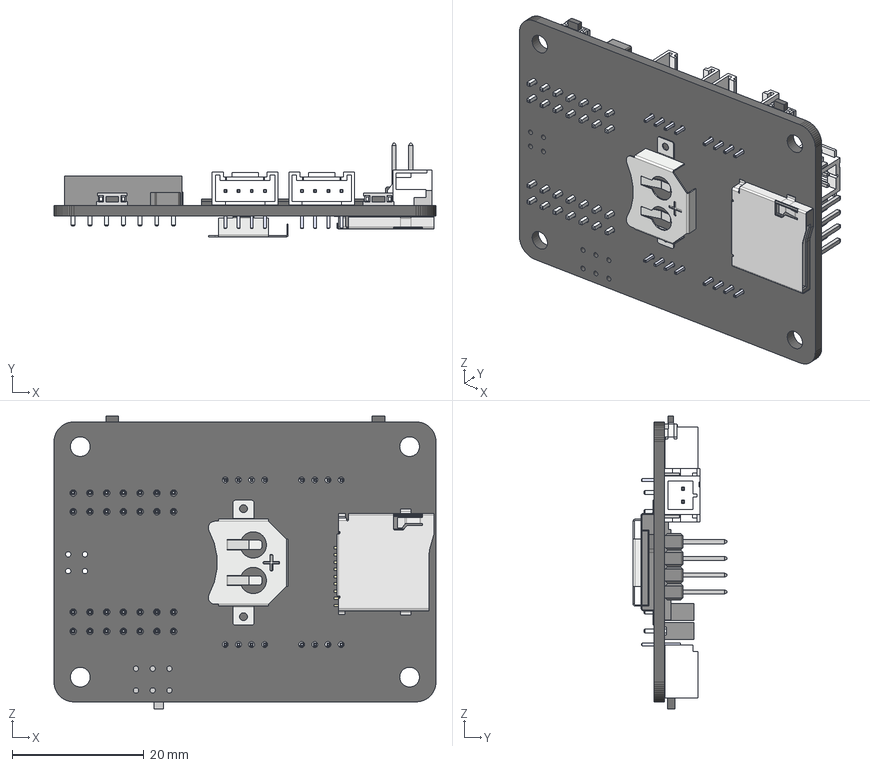
[picture p69: CAD file, 2026-10-08]
guide/cad/expansion.step
58.0 x 14.3 x 44.5 mm
_autosave-Seeeduino XIAO Expansion board_v1.0_200824 PCB
FemaleHeader
FemaleHeader_1
FemaleHeader_2
FemaleHeader_3
Grove Connector (lying) x 4
Document
JST - PH - SMD (R) - 2Pin - 2.00mm
Frame
Pin1
Pin2
Pin3
Pin4
Pin5
Pin6
Pin7
Pin8
Pin9
1TS003B
1TS003B_1
По умолчанию
