railyai/raily-pin/published/keyring/case-3d/bambu/printers/a1/v5-batch.3mf

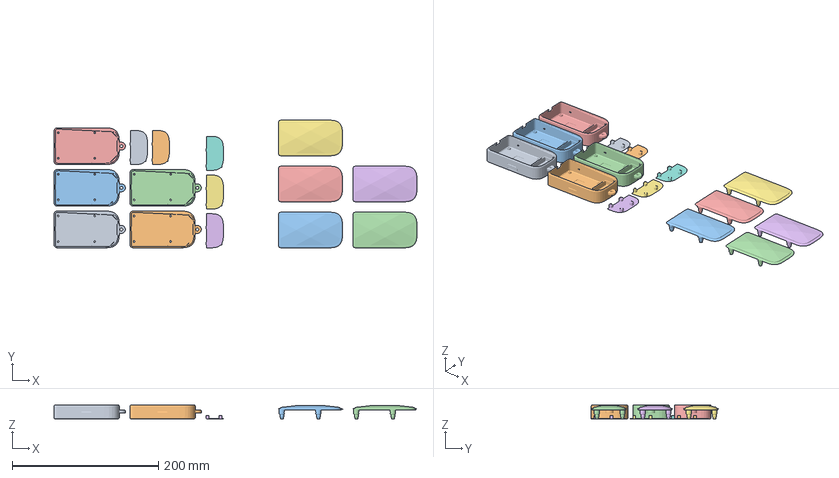
[picture p70: CAD file, 2026-10-08]
published/keyring/case-3d/bambu/printers/a1/v5-batch.3mf
497.1 x 174.8 x 19.3 mm
assemble_1 x 2
assemble_2 x 2
assemble_3 x 2
assemble_4 x 2
assemble_5 x 2
assemble_6
assemble_7
assemble_8
assemble_9
assemble_10
