railyai/raily-pin/published/keyring/case-3d/bambu/printers/a1m/v5.3mf

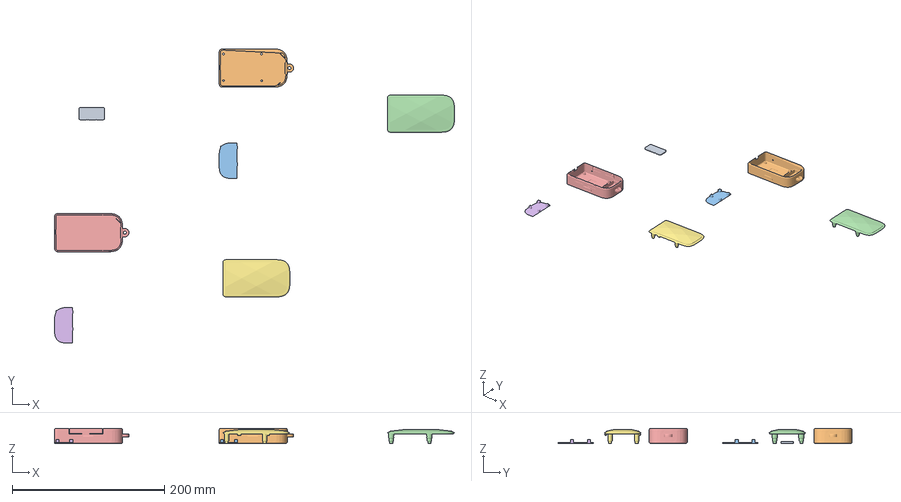
[picture p71: CAD file, 2026-10-08]
published/keyring/case-3d/bambu/printers/a1m/v5.3mf
524.8 x 386.1 x 19.3 mm
led-coupon_1
assemble_1 x 4
assemble_2 x 2
