railyai/raily-pin/published/keyring/case-3d/checkpoint-a/A4-pusher-A1mini.gcode.3mf

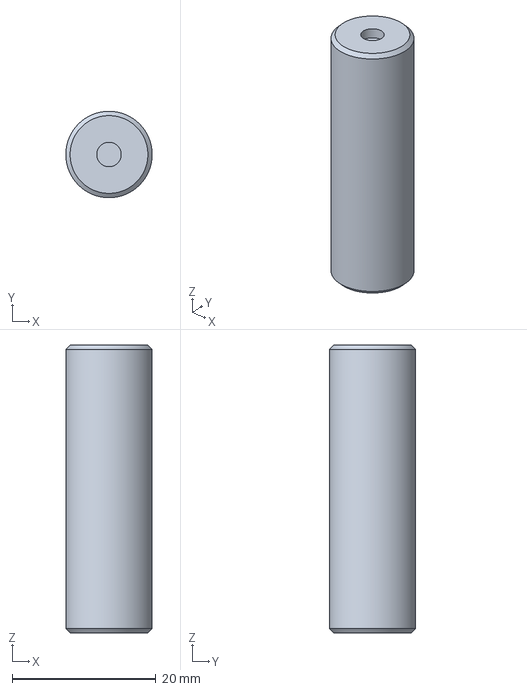
[picture p73: CAD file, 2026-10-08]
published/keyring/case-3d/checkpoint-a/A4-pusher-A1mini.gcode.3mf
12.0 x 12.0 x 40.0 mm
