railyai/raily-pin/published/keyring/case-3d/print/closure-b/keyring-cover-cover.stl

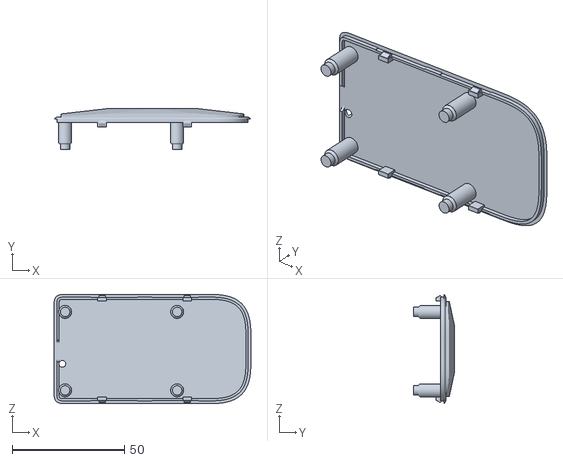
[picture p74: CAD file, 2026-10-08]
published/keyring/case-3d/print/closure-b/keyring-cover-cover.stl
87.9 x 18.4 x 48.8
