railyai/raily-pin/published/keyring/case-3d/print/shelf-variants/shelf-F.stl

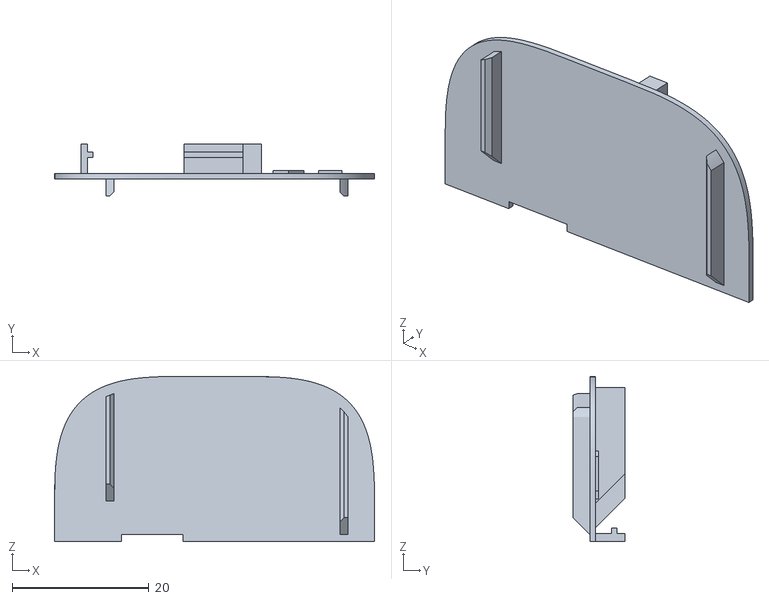
[picture p75: CAD file, 2026-10-08]
published/keyring/case-3d/print/shelf-variants/shelf-F.stl
46.8 x 7.60 x 24.1
