railyai/raily-pin/published/keyring/case-3d/v2/bambu/printers/a1m/v1-noams.3mf

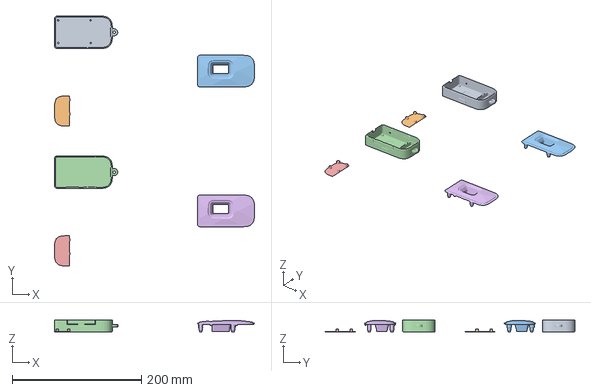
[picture p77: CAD file, 2026-10-08]
published/keyring/case-3d/v2/bambu/printers/a1m/v1-noams.3mf
308.9 x 386.1 x 19.1 mm
assemble_1 x 4
assemble_2 x 2
