railyai/raily-pin/published/keyring/case-3d/v2/bambu/printers/h2d/v5-batch.3mf

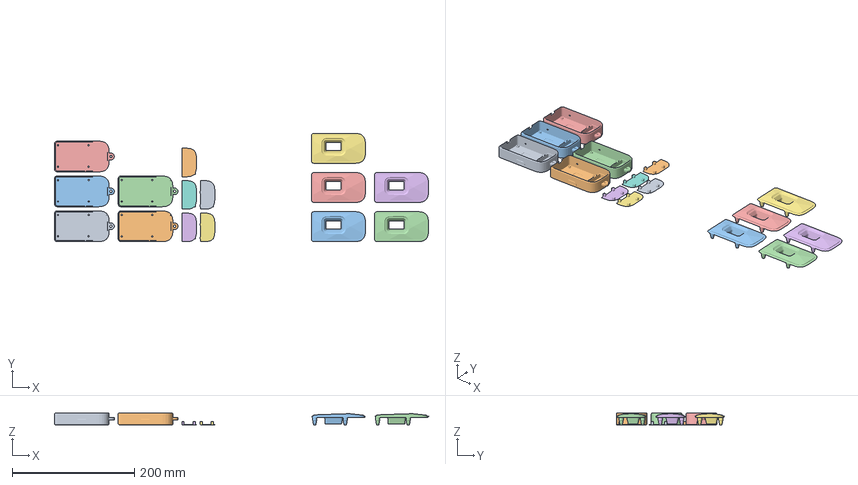
[picture p78: CAD file, 2026-10-08]
published/keyring/case-3d/v2/bambu/printers/h2d/v5-batch.3mf
611.1 x 177.0 x 19.1 mm
assemble_1 x 2
assemble_2 x 2
assemble_3 x 2
assemble_4 x 2
assemble_5 x 2
assemble_6
assemble_7
assemble_8
assemble_9
assemble_10
