railyai/raily-pin/published/keyring/case-3d/v2/bambu/printers/h2s/v1-noams.3mf

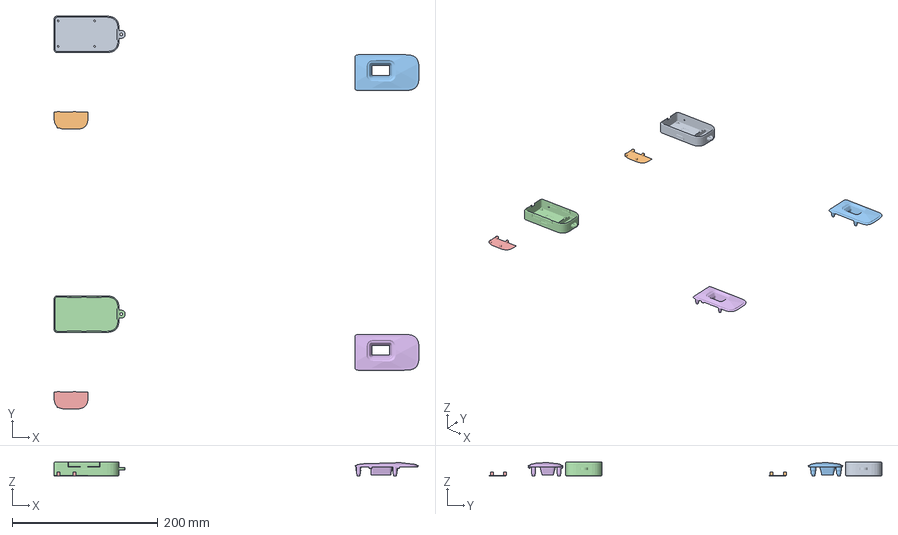
[picture p79: CAD file, 2026-10-08]
published/keyring/case-3d/v2/bambu/printers/h2s/v1-noams.3mf
500.9 x 539.4 x 19.1 mm
assemble_1 x 4
assemble_2 x 2
