railyai/raily-pin/published/keyring/case-3d/v2/print-flat/closure-b/keyring-cover-cover.stl

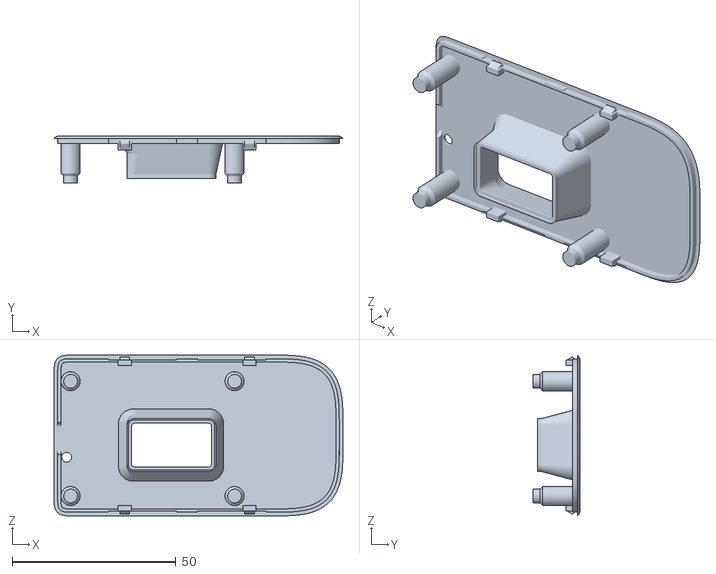
[picture p81: CAD file, 2026-10-08]
published/keyring/case-3d/v2/print-flat/closure-b/keyring-cover-cover.stl
88.1 x 14.4 x 49.0
