railyai/raily-pin/published/keyring/case-3d/v2/print/keyring-led-coupon.stl

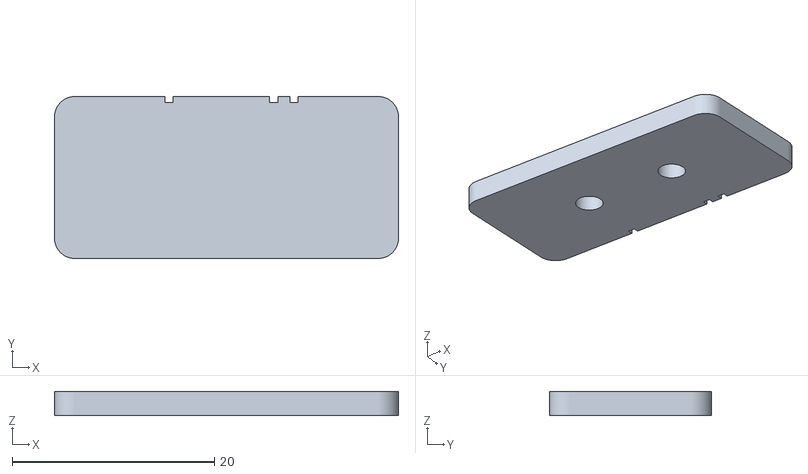
[picture p83: CAD file, 2026-10-08]
published/keyring/case-3d/v2/print/keyring-led-coupon.stl
34.0 x 16.0 x 2.40
