railyai/raily-pin/published/keyring/case-3d/bambu/printers/a1/v1-noams.3mf

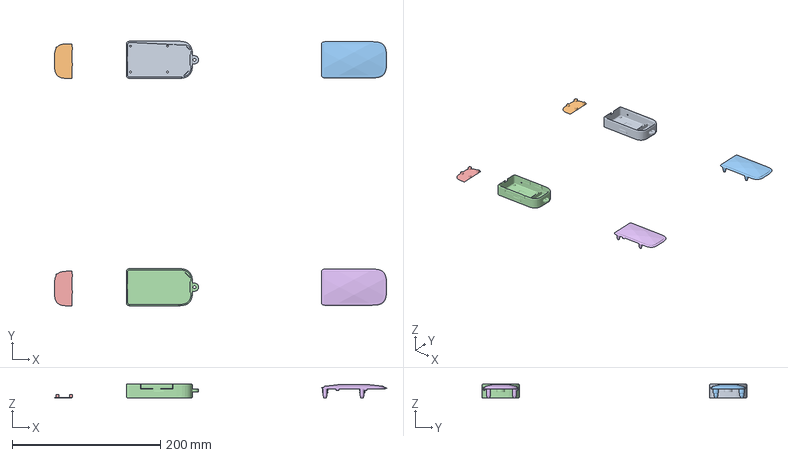
[picture p84: CAD file, 2026-10-08]
published/keyring/case-3d/bambu/printers/a1/v1-noams.3mf
448.5 x 357.6 x 19.3 mm
assemble_1 x 4
assemble_2 x 2
