railyai/raily-pin/published/keyring/case-3d/bambu/printers/a1m/v5-batch.3mf

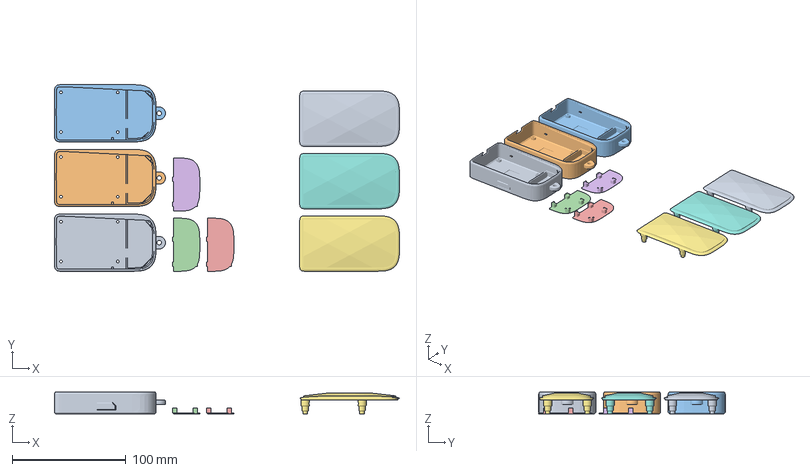
[picture p85: CAD file, 2026-10-08]
published/keyring/case-3d/bambu/printers/a1m/v5-batch.3mf
303.9 x 164.4 x 19.3 mm
assemble_1 x 2
assemble_2 x 2
assemble_3 x 2
assemble_4
assemble_5
assemble_6
