railyai/raily-pin/published/keyring/case-3d/v2/bambu/printers/h2d/v5.3mf

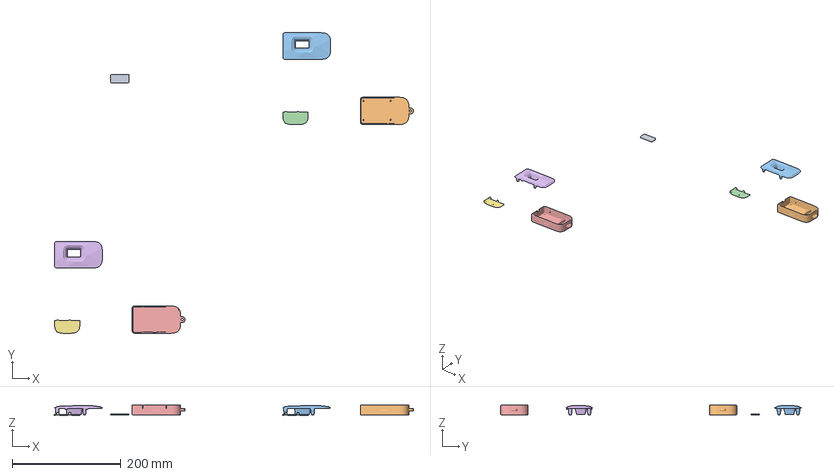
[picture p89: CAD file, 2026-10-08]
published/keyring/case-3d/v2/bambu/printers/h2d/v5.3mf
660.5 x 553.0 x 19.1 mm
led-coupon_1
assemble_1 x 2
assemble_2 x 2
assemble_3 x 2
