railyai/raily-pin/published/keyring/case-3d/v2/print-flat/keyring-case.step

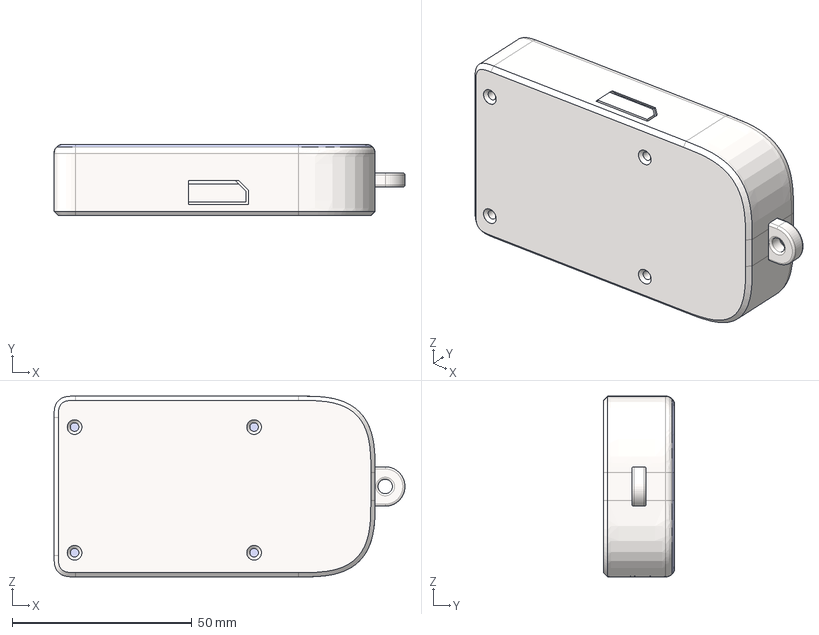
[picture p90: CAD file, 2026-10-08]
published/keyring/case-3d/v2/print-flat/keyring-case.step
97.8 x 19.9 x 50.4 mm
tray-tray
tray-button
tray-loop
cover-cover
shelf-shelf
cover-led
