railyai/raily-pin/published/keyring/case-3d/v2/print/keyring-window-insert.stl

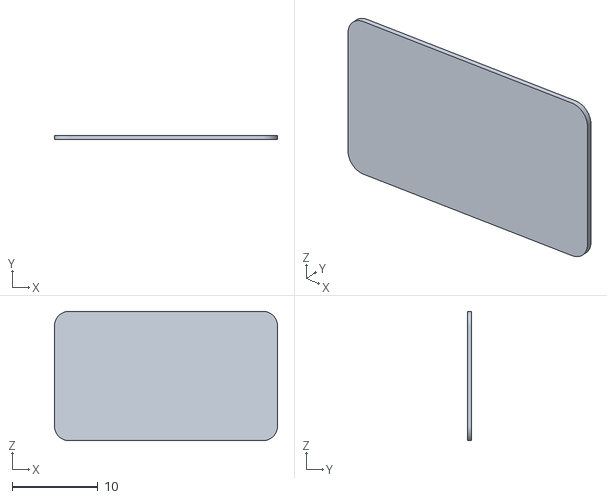
[picture p91: CAD file, 2026-10-08]
published/keyring/case-3d/v2/print/keyring-window-insert.stl
26.1 x 0.5 x 15.1
