railyai/raily-pin/published/keyring/case-3d/print/shelf-variants/shelf-D-floor-stop-plus-z.stl

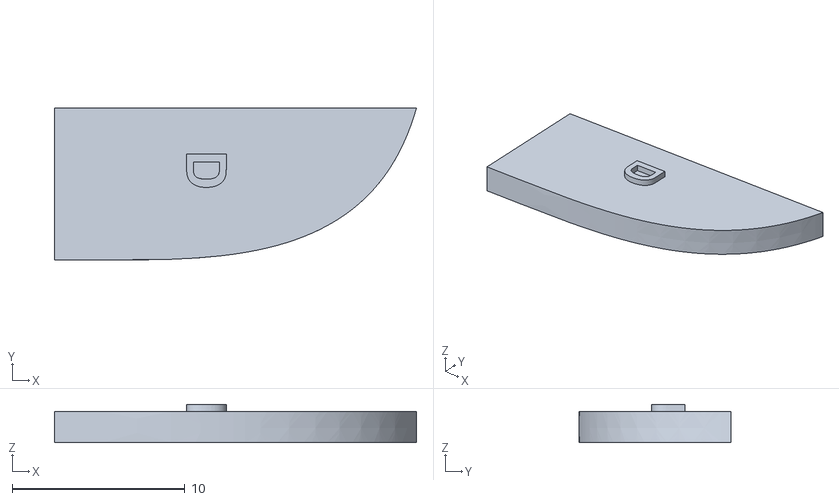
[picture p92: CAD file, 2026-10-08]
published/keyring/case-3d/print/shelf-variants/shelf-D-floor-stop-plus-z.stl
20.9 x 8.80 x 2.20
