railyai/raily-pin/published/keyring/case-3d/print/shelf-variants/shelf-D-floor-stop-minus-z.stl

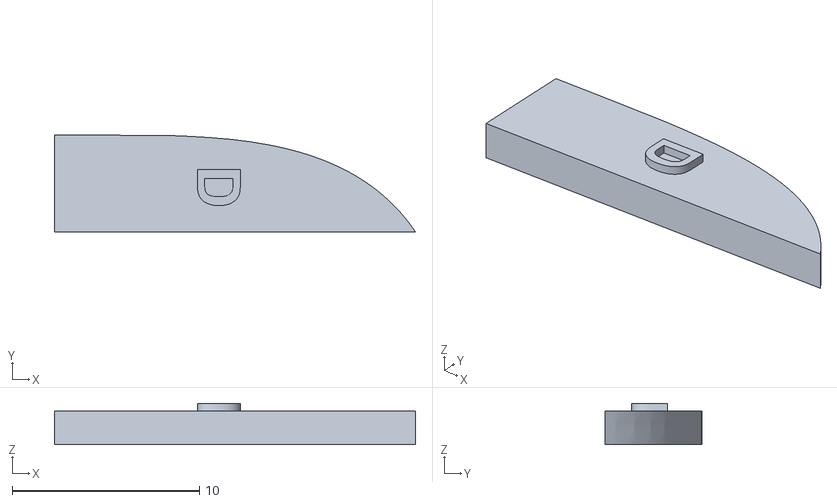
[picture p93: CAD file, 2026-10-08]
published/keyring/case-3d/print/shelf-variants/shelf-D-floor-stop-minus-z.stl
19.3 x 5.17 x 2.20
