railyai/raily-pin/published/keyring/case-3d/print/shelf-variants/shelf-B.stl

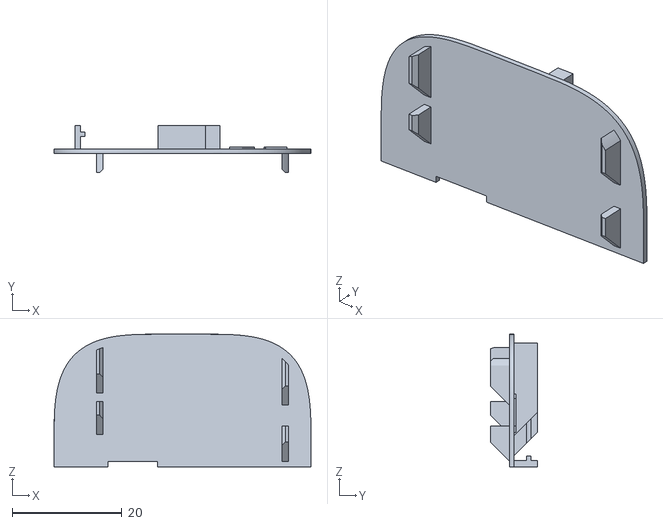
[picture p95: CAD file, 2026-10-08]
published/keyring/case-3d/print/shelf-variants/shelf-B.stl
46.8 x 8.60 x 24.1
