railyai/raily-pin/published/keyring/case-3d/print/keyring-case.step

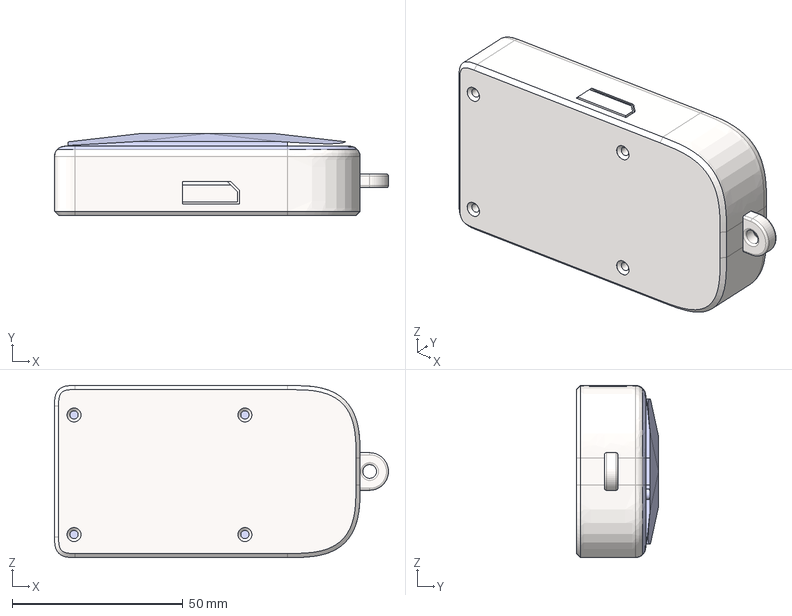
[picture p96: CAD file, 2026-10-08]
published/keyring/case-3d/print/keyring-case.step
97.8 x 24.0 x 50.4 mm
tray-tray
tray-button
tray-loop
cover-cover
shelf-shelf
cover-led
