railyai/raily-pin/published/keyring/case-3d/print/shelf-variants/shelf-variants-a1m.3mf

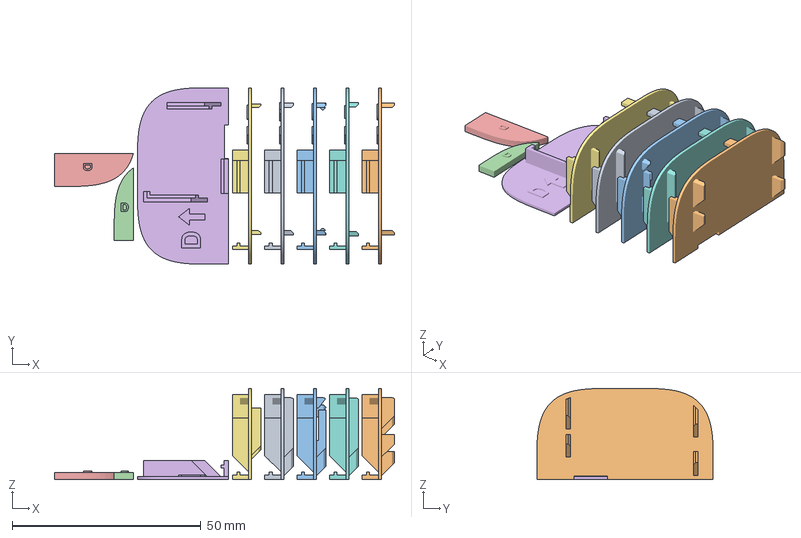
[picture p97: CAD file, 2026-10-08]
published/keyring/case-3d/print/shelf-variants/shelf-variants-a1m.3mf
90.1 x 46.8 x 24.1 mm
assemble_1
assemble_2
assemble_3
assemble_4
assemble_5
assemble_6
assemble_7
assemble_8
