railyai/raily-pin/guide/art/app-phone-fill.png

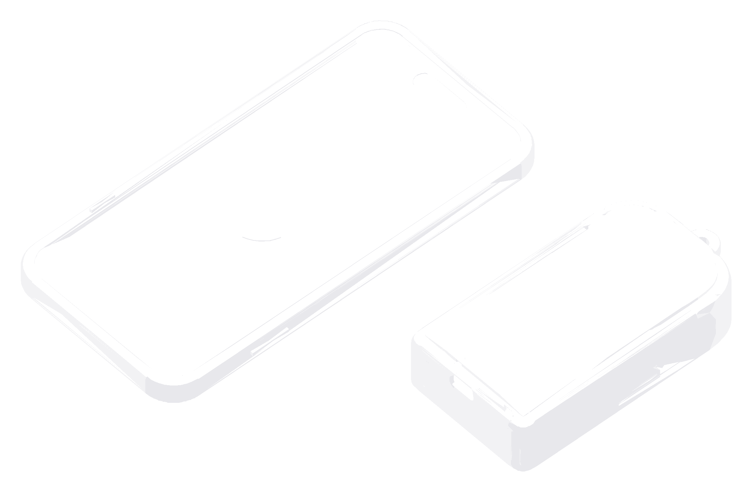
guide/art/app-phone-fill.png
