railyai/raily-pin/guide/art/app-phone-only-fill.png

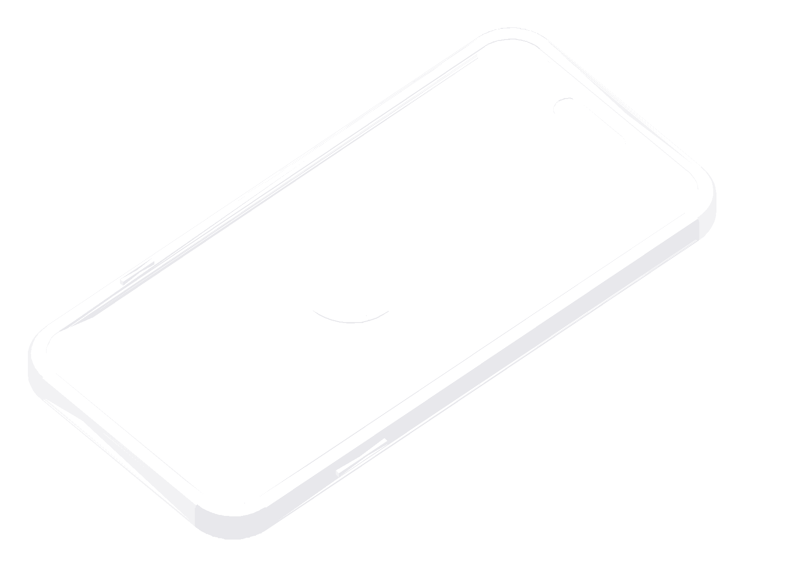
guide/art/app-phone-only-fill.png
