railyai/raily-pin/guide/art/battery-jst-fill.png

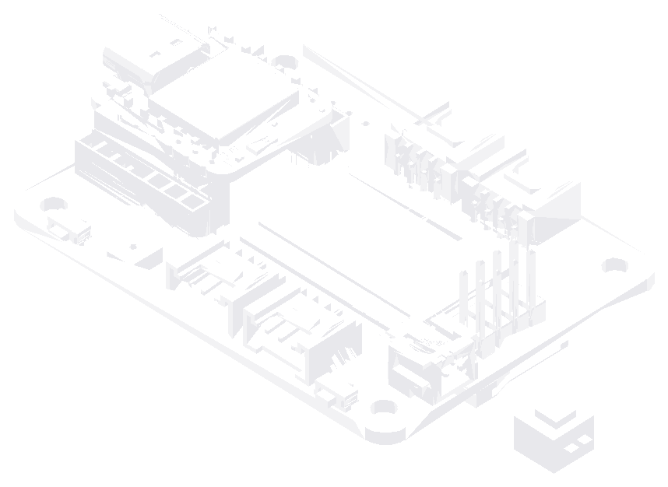
guide/art/battery-jst-fill.png
