railyai/raily-pin/guide/art/board-tile-fill.png

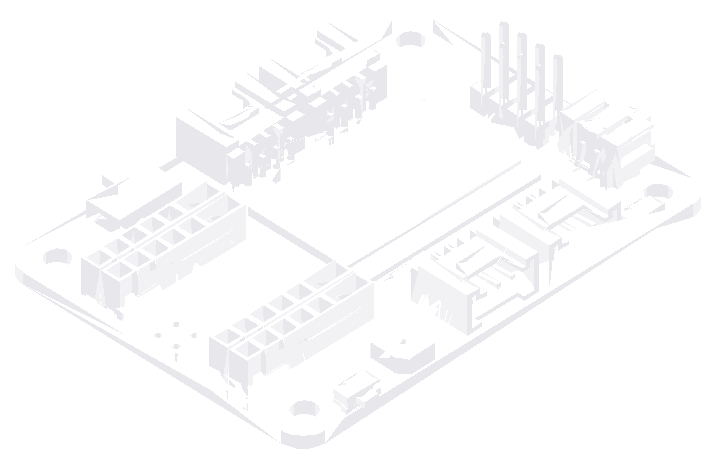
guide/art/board-tile-fill.png
