railyai/raily-pin/guide/art/button-d1-fill.png

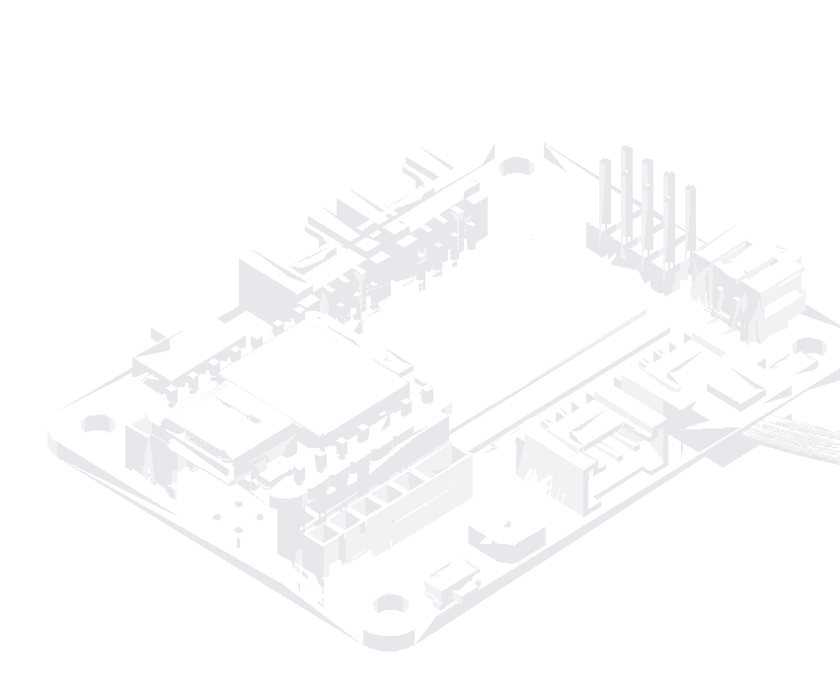
guide/art/button-d1-fill.png
