railyai/raily-pin/guide/art/charge-pouch-fill.png

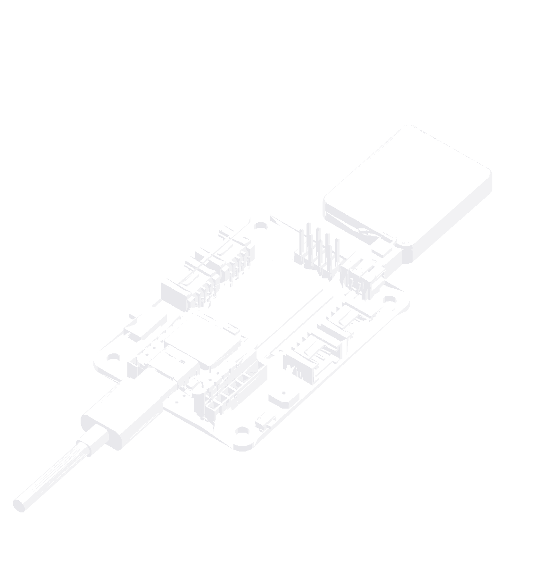
guide/art/charge-pouch-fill.png
