railyai/raily-pin/guide/art/check-meter-fill.png

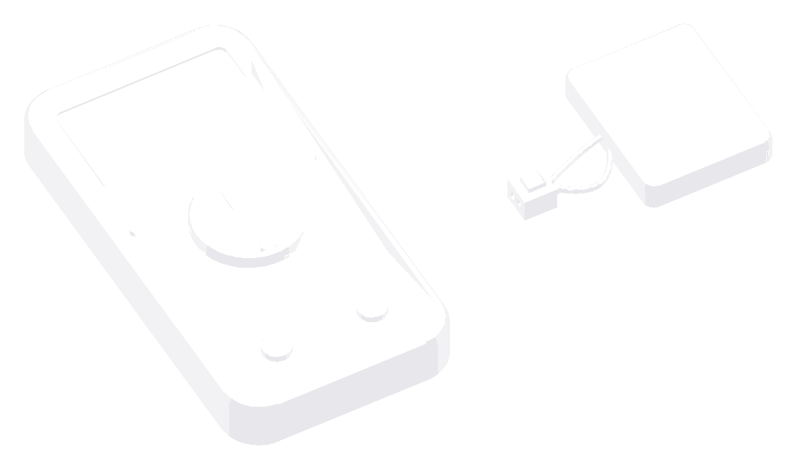
guide/art/check-meter-fill.png
