railyai/raily-pin/guide/art/check-plug-fill.png

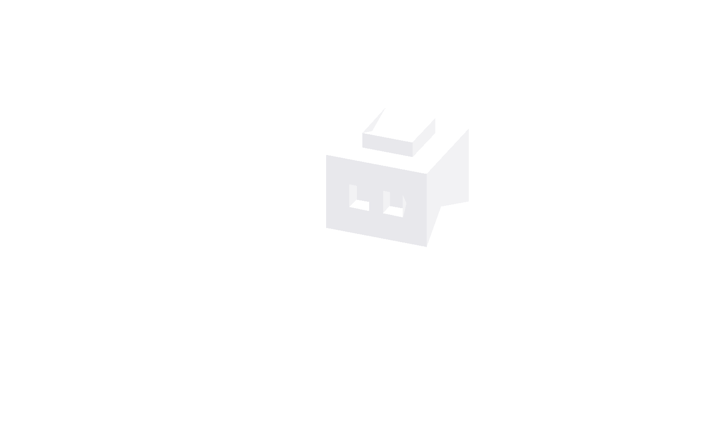
guide/art/check-plug-fill.png
