railyai/raily-pin/guide/art/foam-tape-fill.png

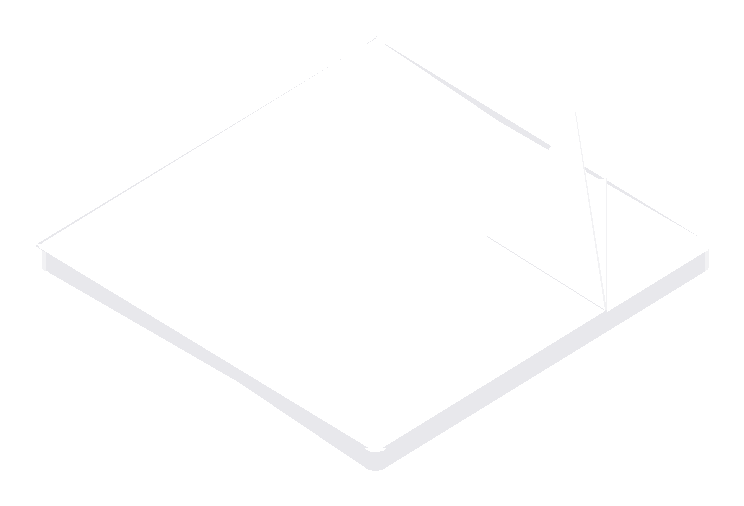
guide/art/foam-tape-fill.png
