railyai/raily-pin/guide/art/grove-cable-5cm.jpg

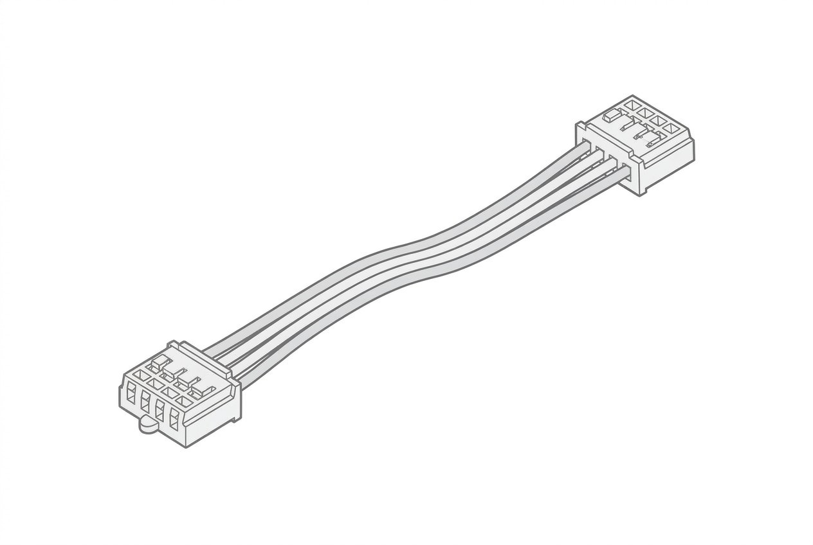
guide/art/grove-cable-5cm.jpg
