railyai/raily-pin/guide/art/grove-qwiic-cable-fill.png

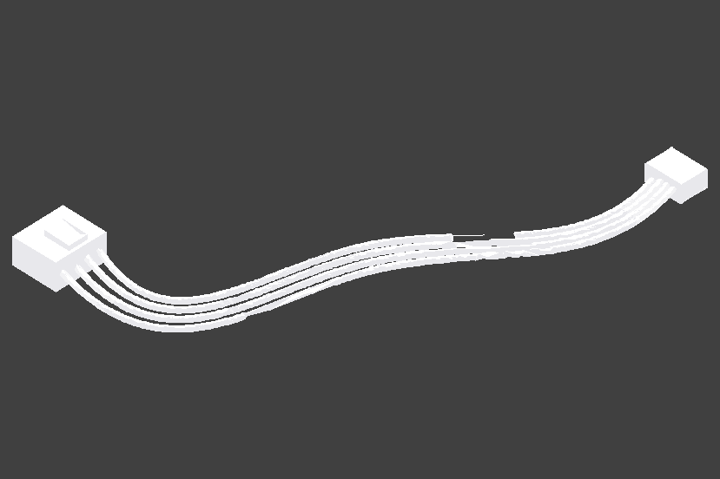
guide/art/grove-qwiic-cable-fill.png
