railyai/raily-pin/guide/art/hdr-clip-fill.png

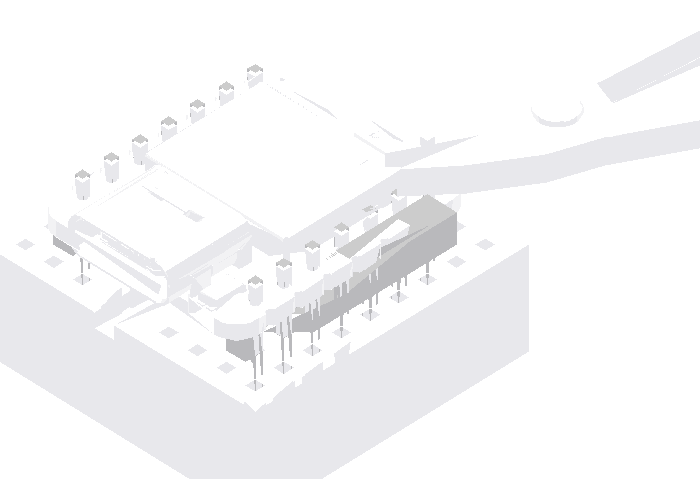
guide/art/hdr-clip-fill.png
