railyai/raily-pin/guide/art/hdr-module-fill.png

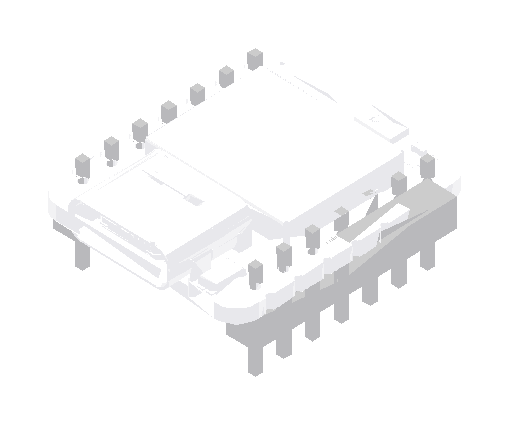
guide/art/hdr-module-fill.png
