railyai/raily-pin/guide/art/hdr-right-fill.png

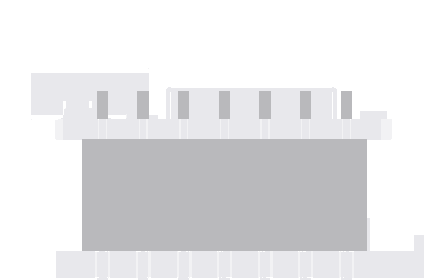
guide/art/hdr-right-fill.png
