railyai/raily-pin/guide/art/hdr-seat-fill.png

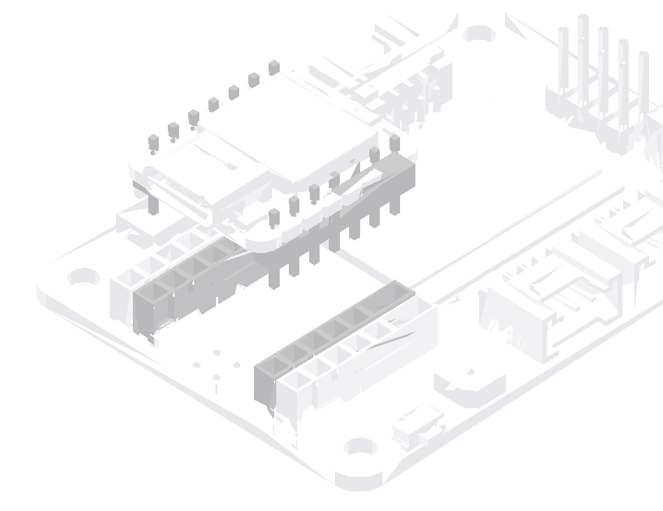
guide/art/hdr-seat-fill.png
