railyai/raily-pin/guide/art/hdr-solder-fill.png

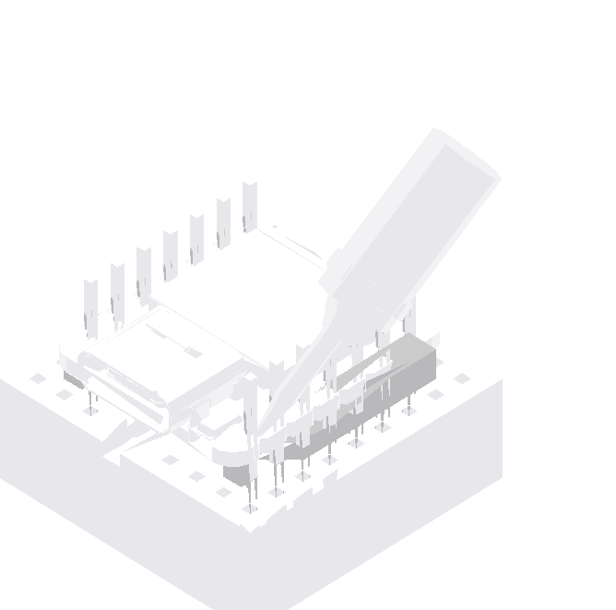
guide/art/hdr-solder-fill.png
