railyai/raily-pin/guide/art/hdr-strip-fill.png

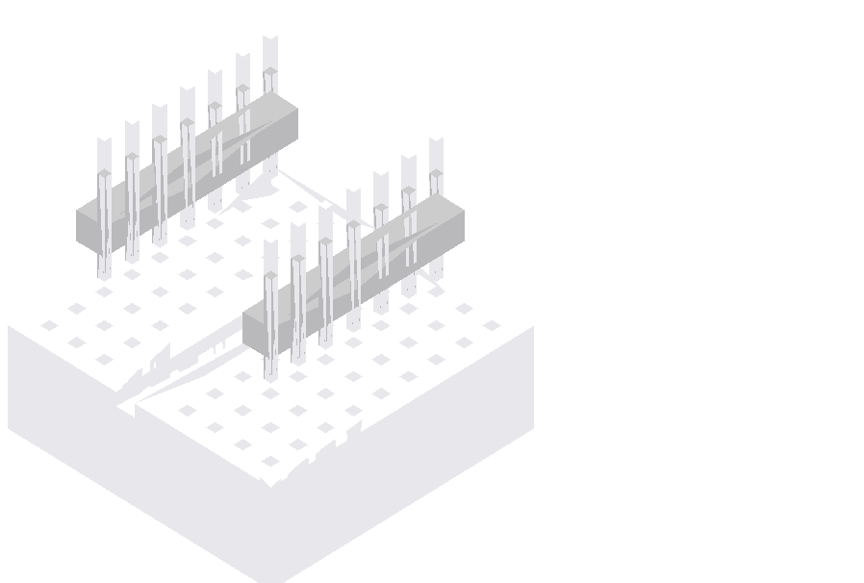
guide/art/hdr-strip-fill.png
