railyai/raily-pin/guide/art/hdr-wrong-fill.png

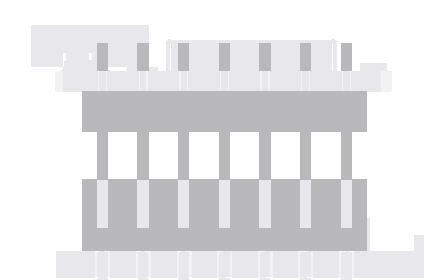
guide/art/hdr-wrong-fill.png
