railyai/raily-pin/guide/art/hdr-xiao-fill.png

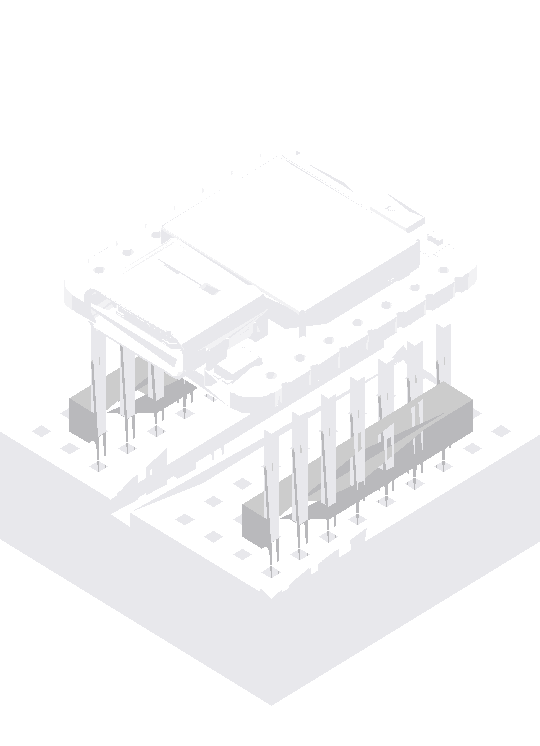
guide/art/hdr-xiao-fill.png
