railyai/raily-pin/guide/art/inset.jpg

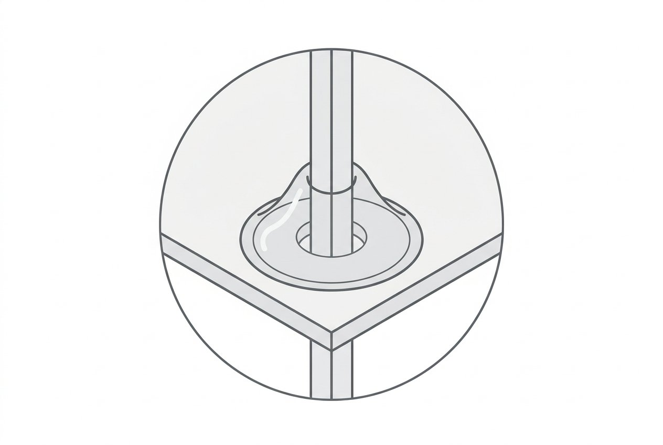
guide/art/inset.jpg
