railyai/raily-pin/guide/art/motor-a0-fill.png

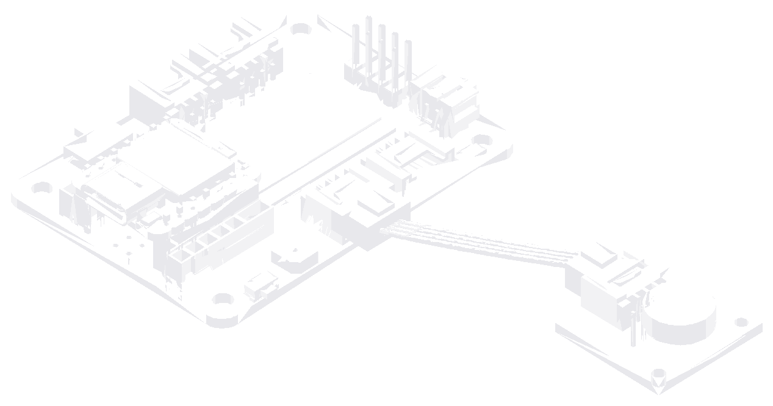
guide/art/motor-a0-fill.png
