railyai/raily-pin/guide/art/motor-chain-fill.png

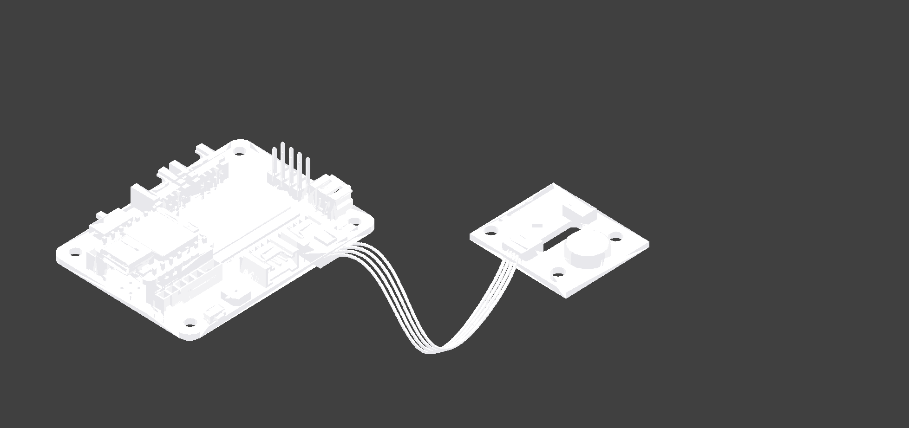
guide/art/motor-chain-fill.png
