railyai/raily-pin/guide/art/qwiic-hub.jpg

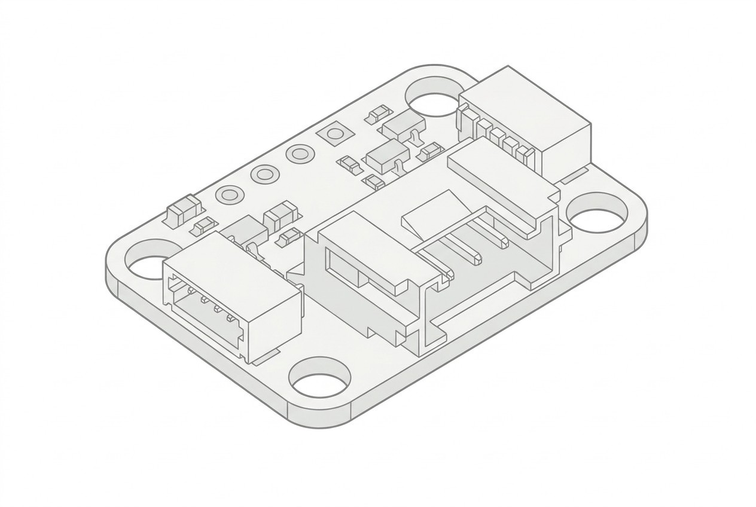
guide/art/qwiic-hub.jpg
