railyai/raily-pin/guide/art/screws-cs-fill.png

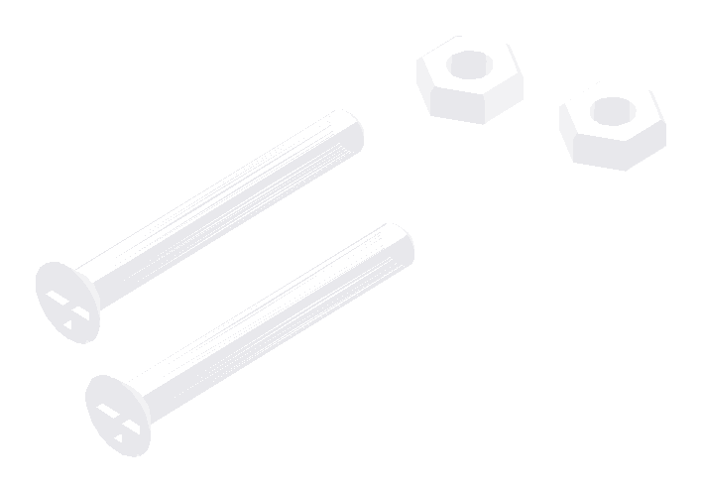
guide/art/screws-cs-fill.png
