railyai/raily-pin/guide/art/seat-vec-fill.png

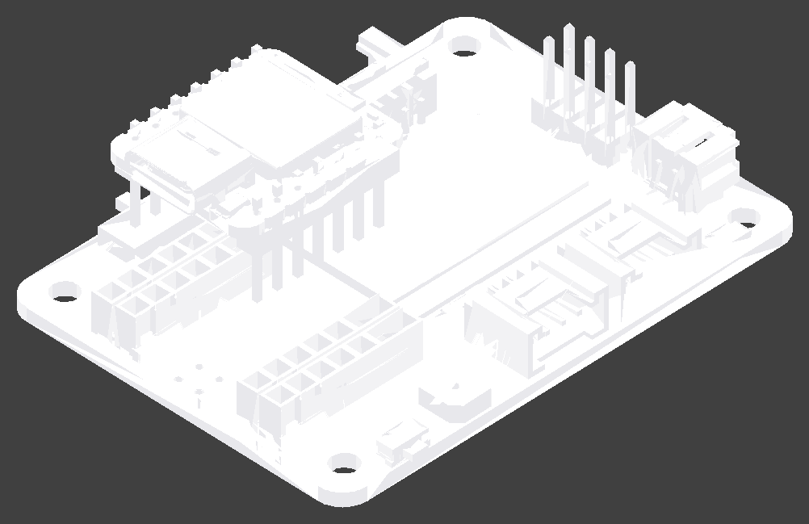
guide/art/seat-vec-fill.png
