railyai/raily-pin/guide/art/solder-vec-fill.png

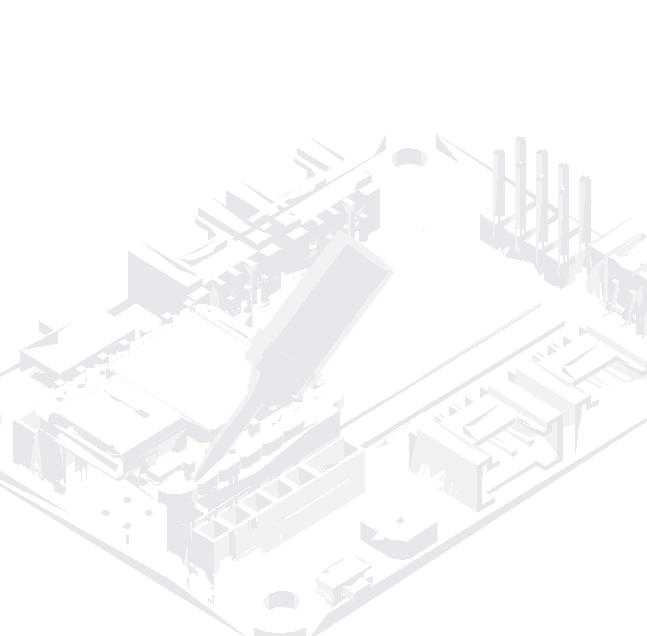
guide/art/solder-vec-fill.png
