railyai/raily-pin/guide/art/switch-off-fill.png

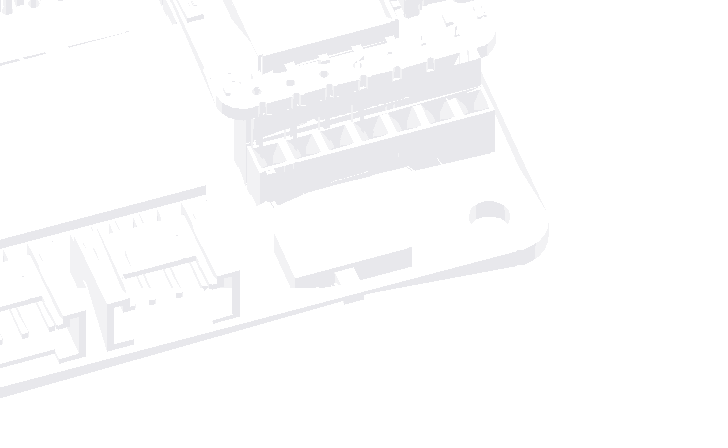
guide/art/switch-off-fill.png
