railyai/raily-pin/guide/art/usb-nobatt-fill.png

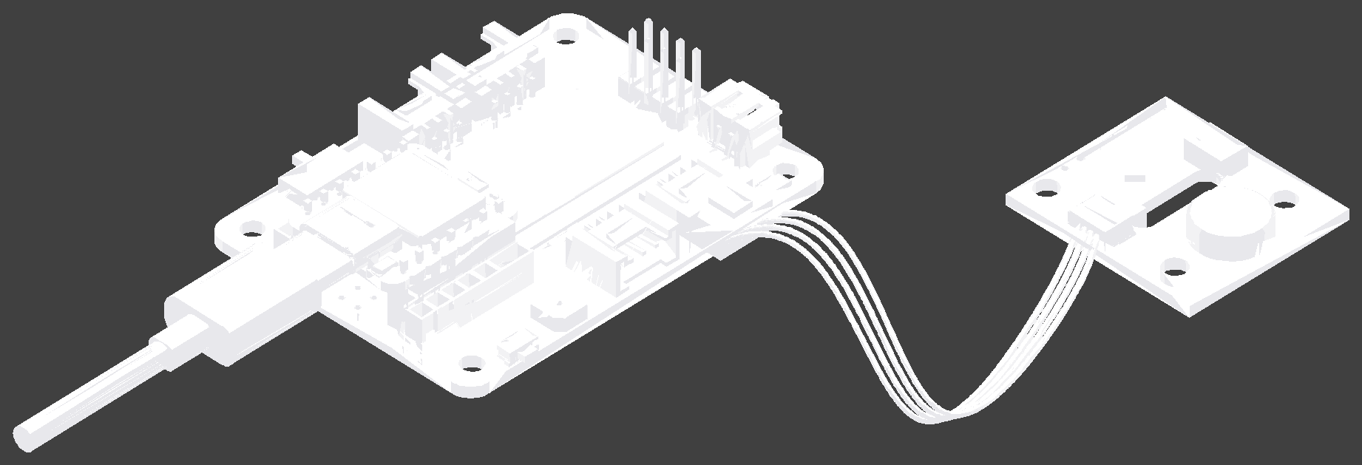
guide/art/usb-nobatt-fill.png
