railyai/raily-pin/guide/pages/page-01.png

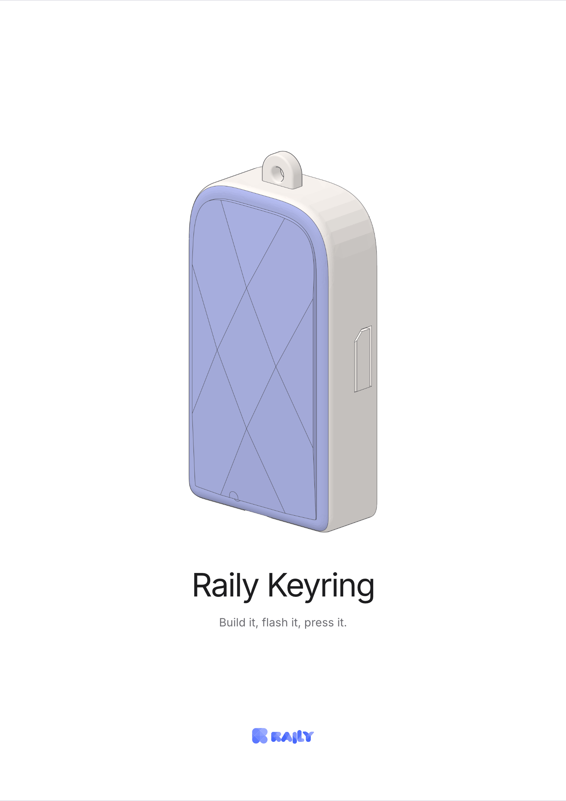
guide/pages/page-01.png
