railyai/raily-pin/guide/pages/page-02.png

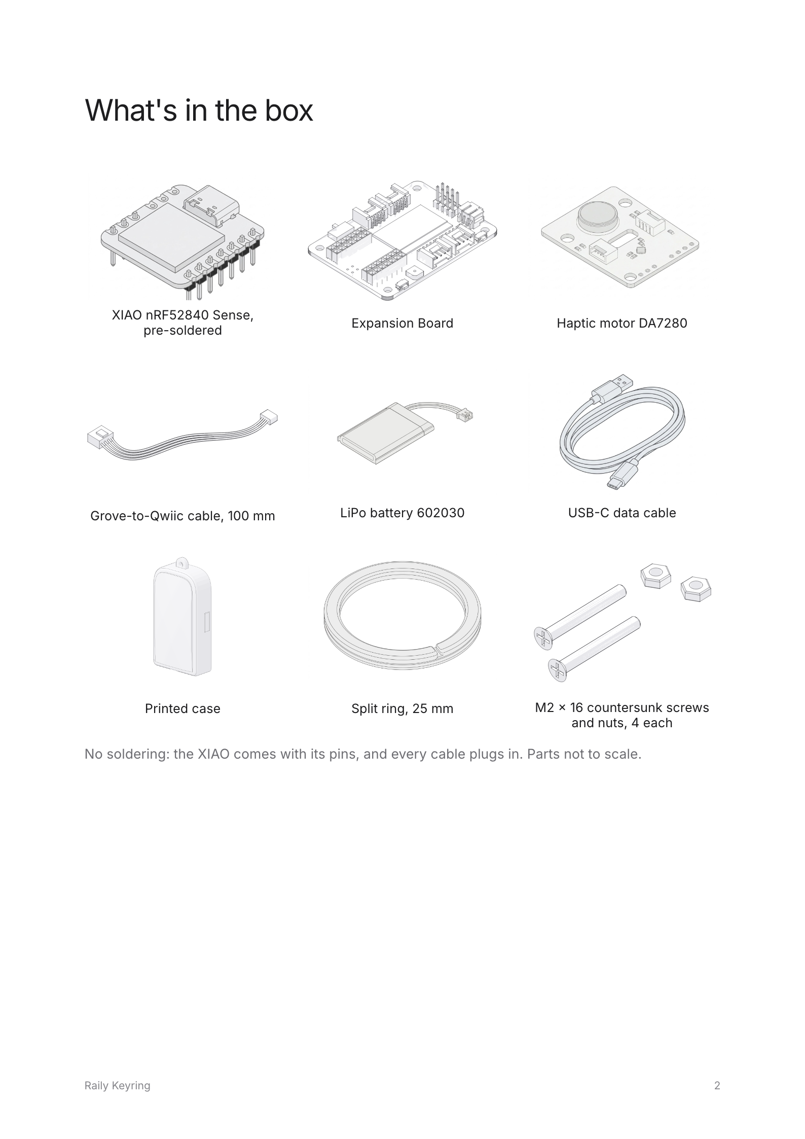
guide/pages/page-02.png
