railyai/raily-pin/guide/pages/page-04.png

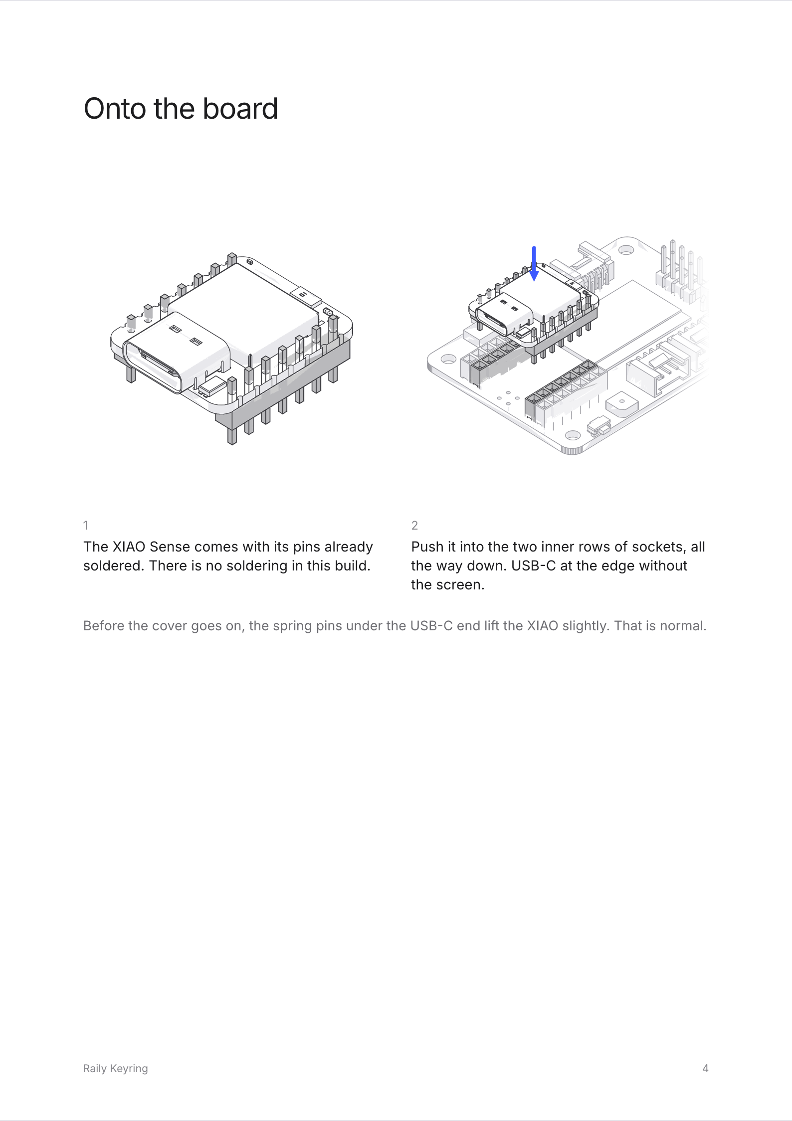
guide/pages/page-04.png
