railyai/raily-pin/guide/pages/page-06.png

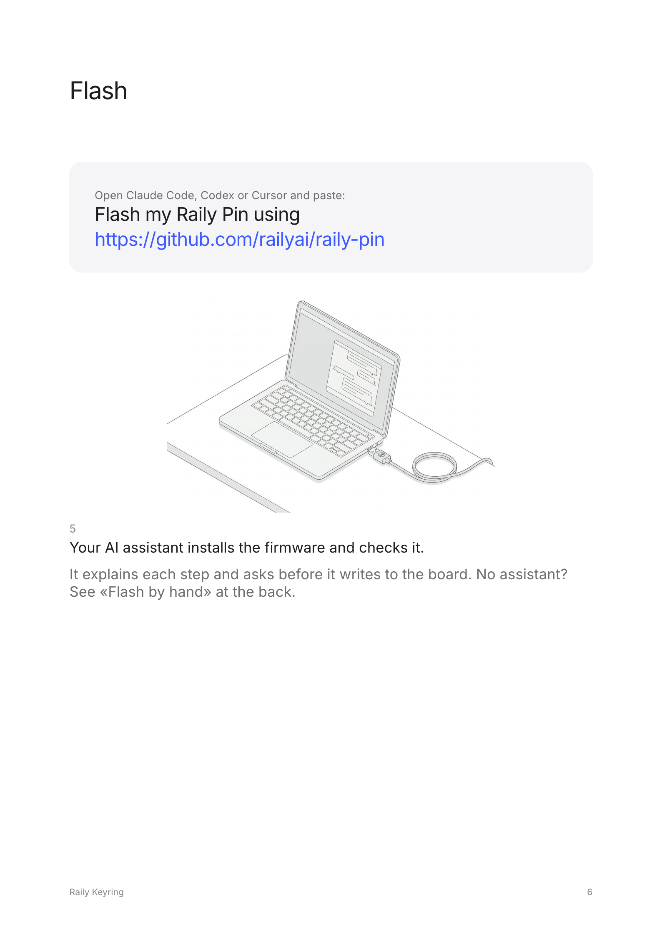
guide/pages/page-06.png
