railyai/raily-pin/guide/pages/page-07.png

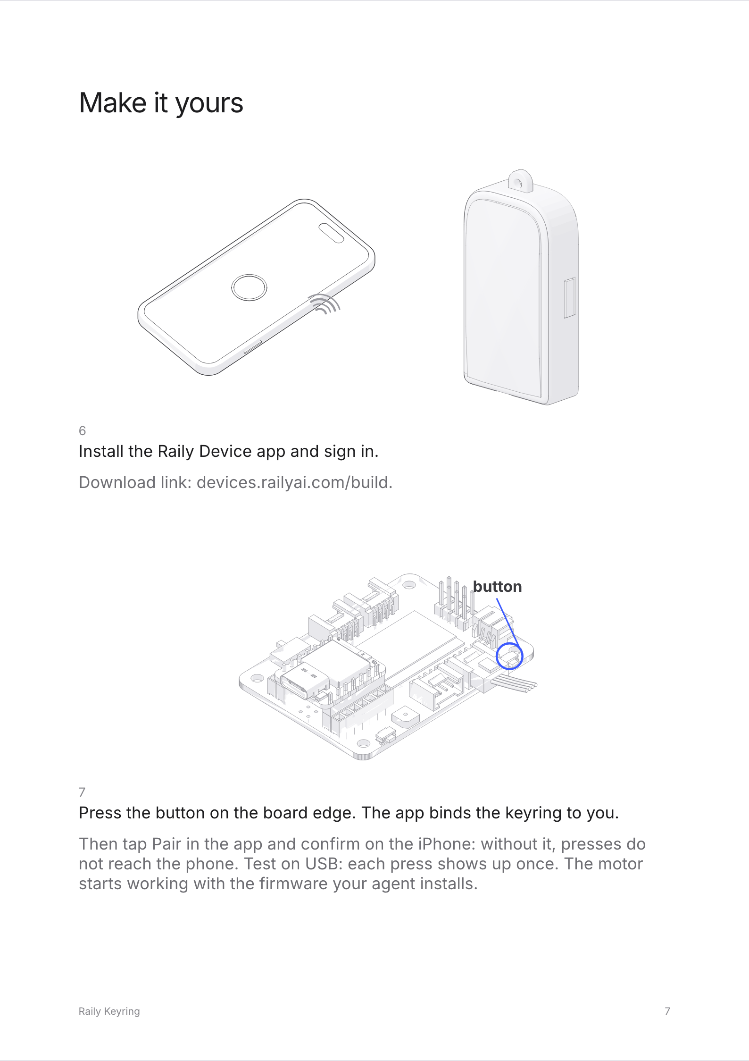
guide/pages/page-07.png
