railyai/raily-pin/guide/pages/page-08.png

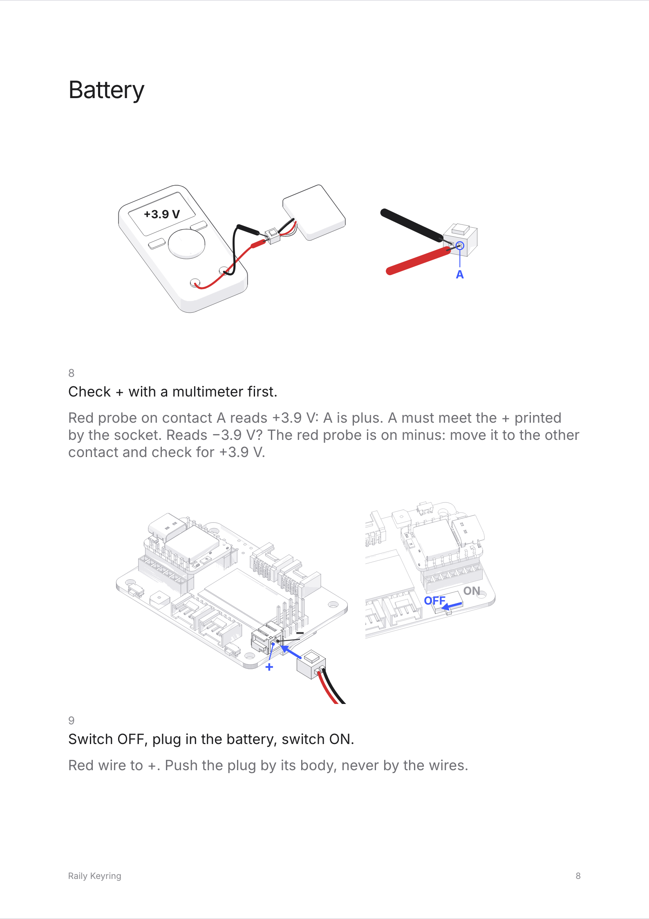
guide/pages/page-08.png
