railyai/raily-pin/guide/pages/page-10.png

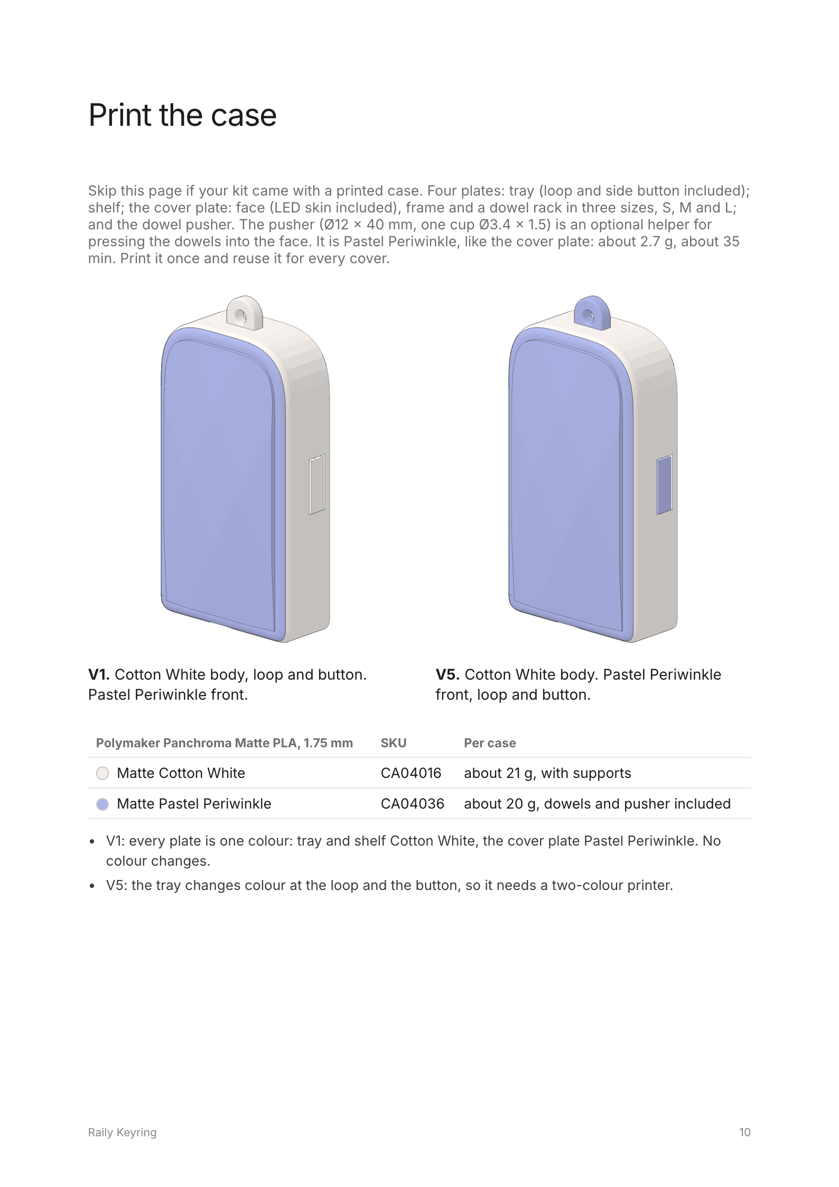
guide/pages/page-10.png
