railyai/raily-pin/guide/pages/page-12.png

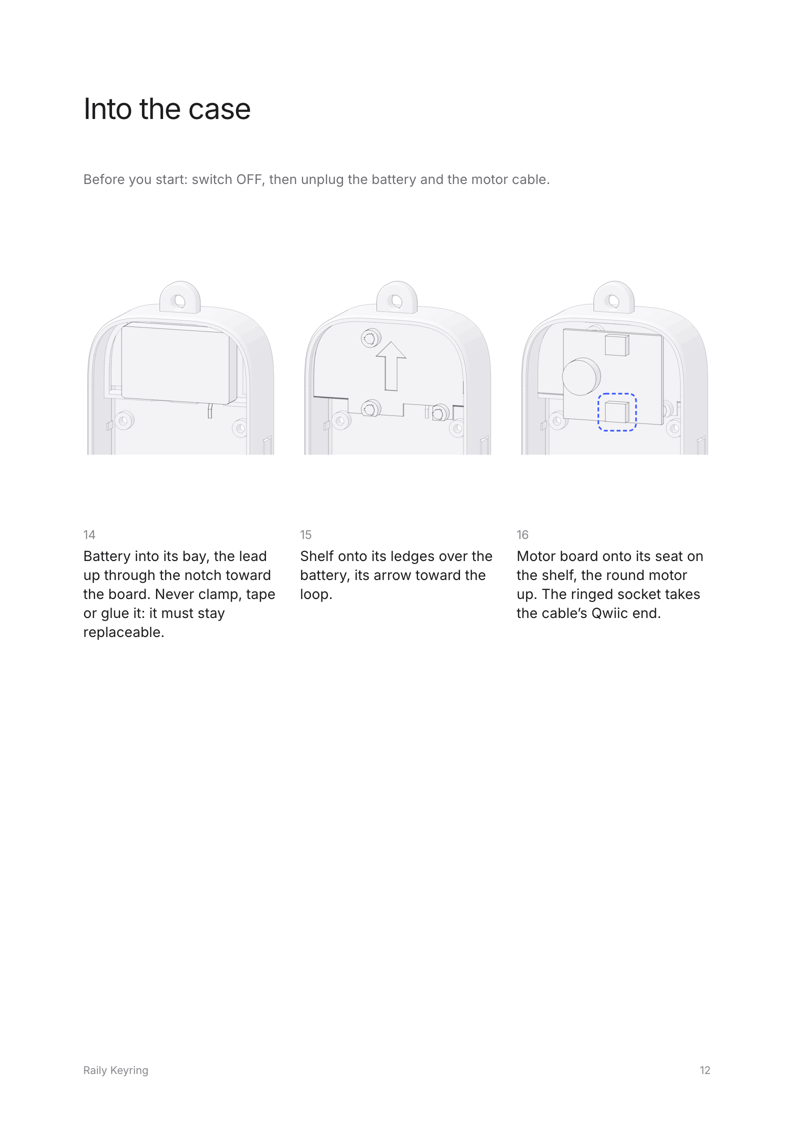
guide/pages/page-12.png
