railyai/raily-pin/guide/pages/page-13.png

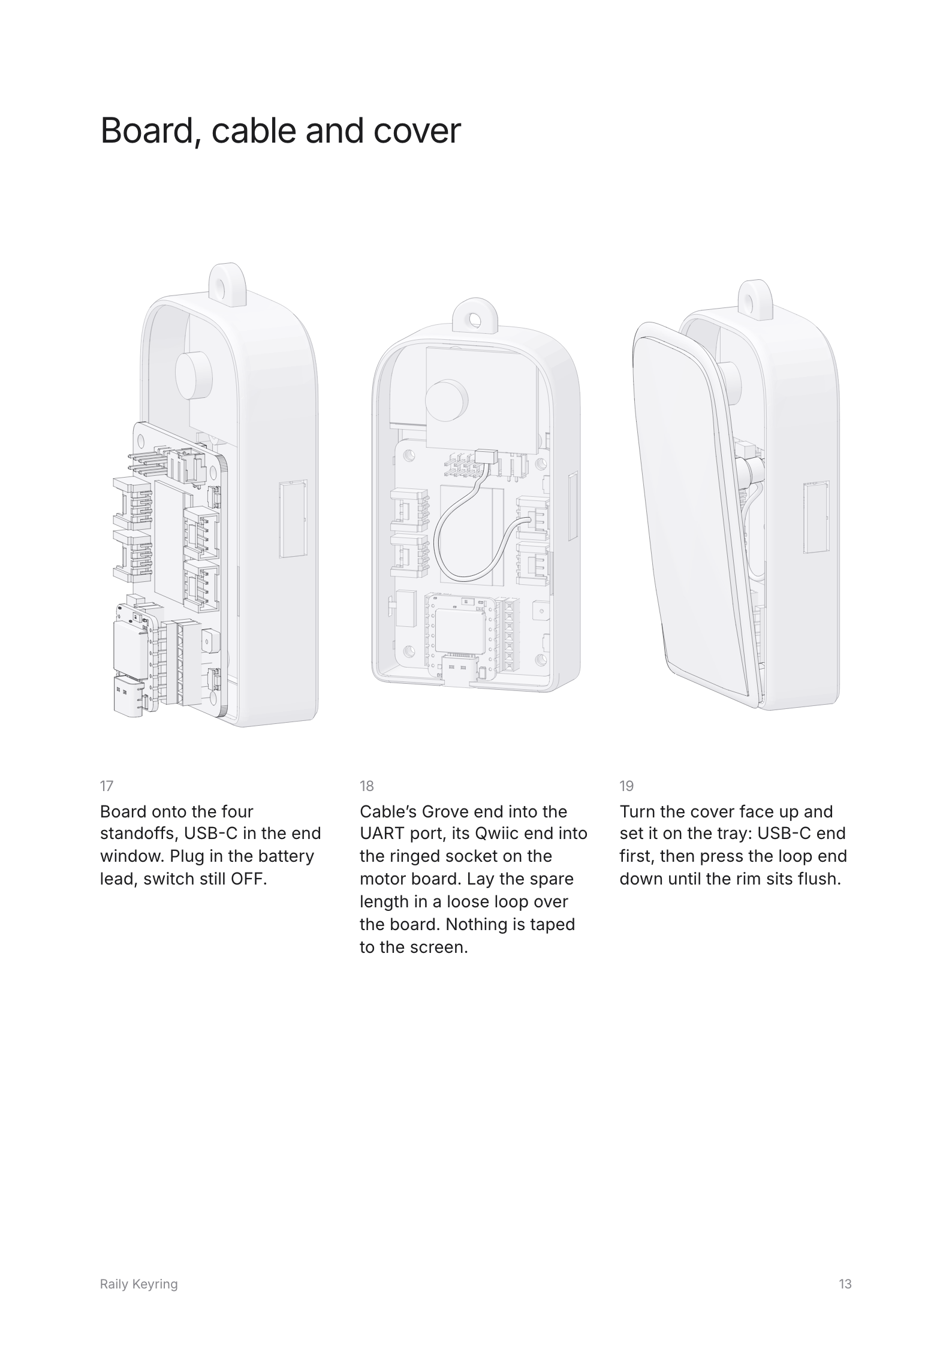
guide/pages/page-13.png
