railyai/raily-pin/guide/pages/page-14.png

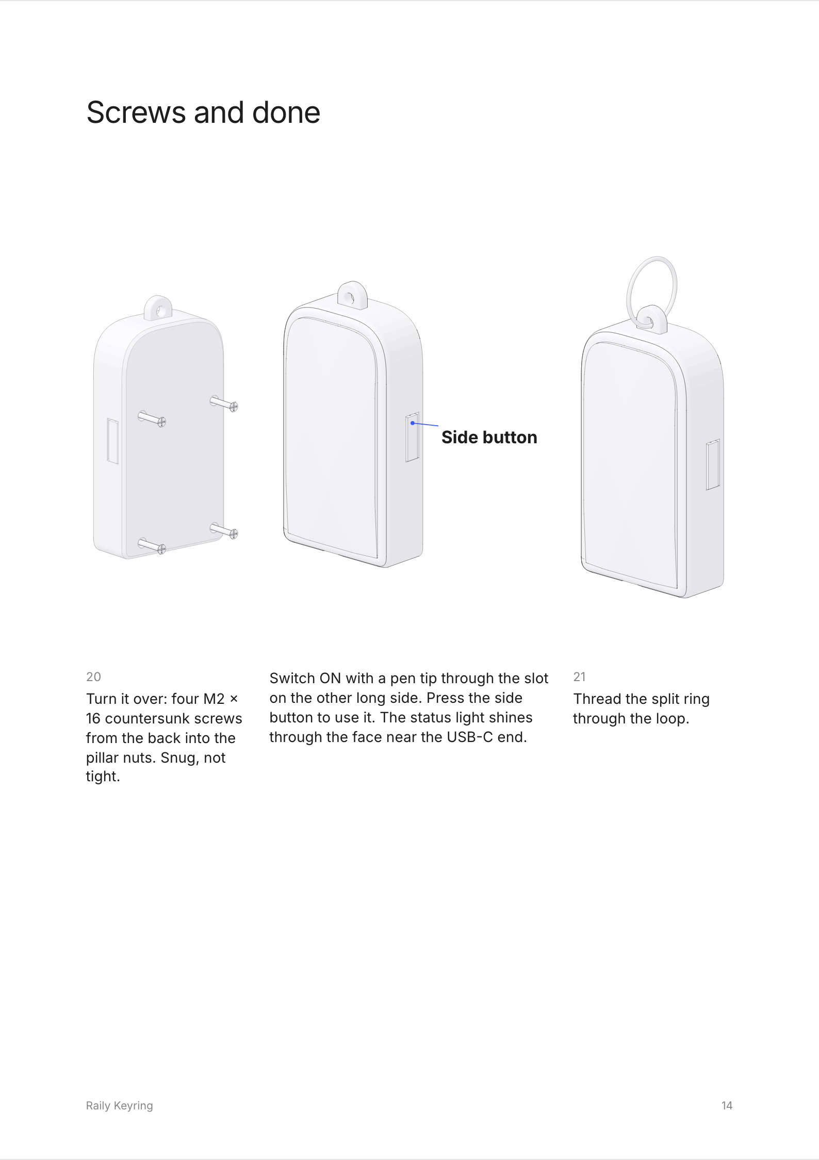
guide/pages/page-14.png
