railyai/raily-pin/guide/pages/page-15.png

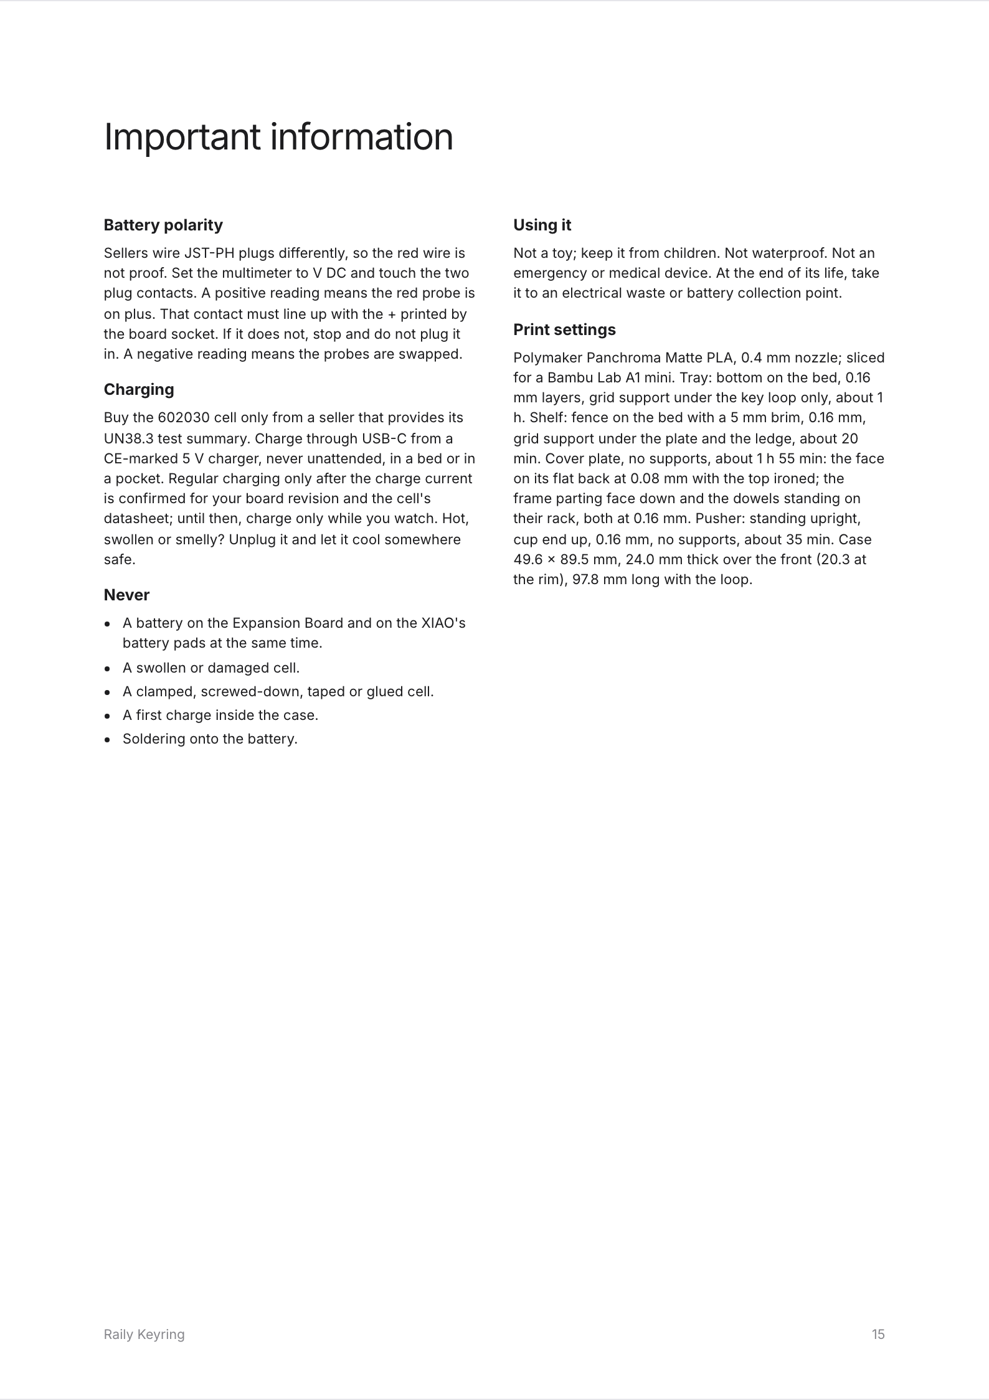
guide/pages/page-15.png
