railyai/raily-pin/guide/pages/page-16.png

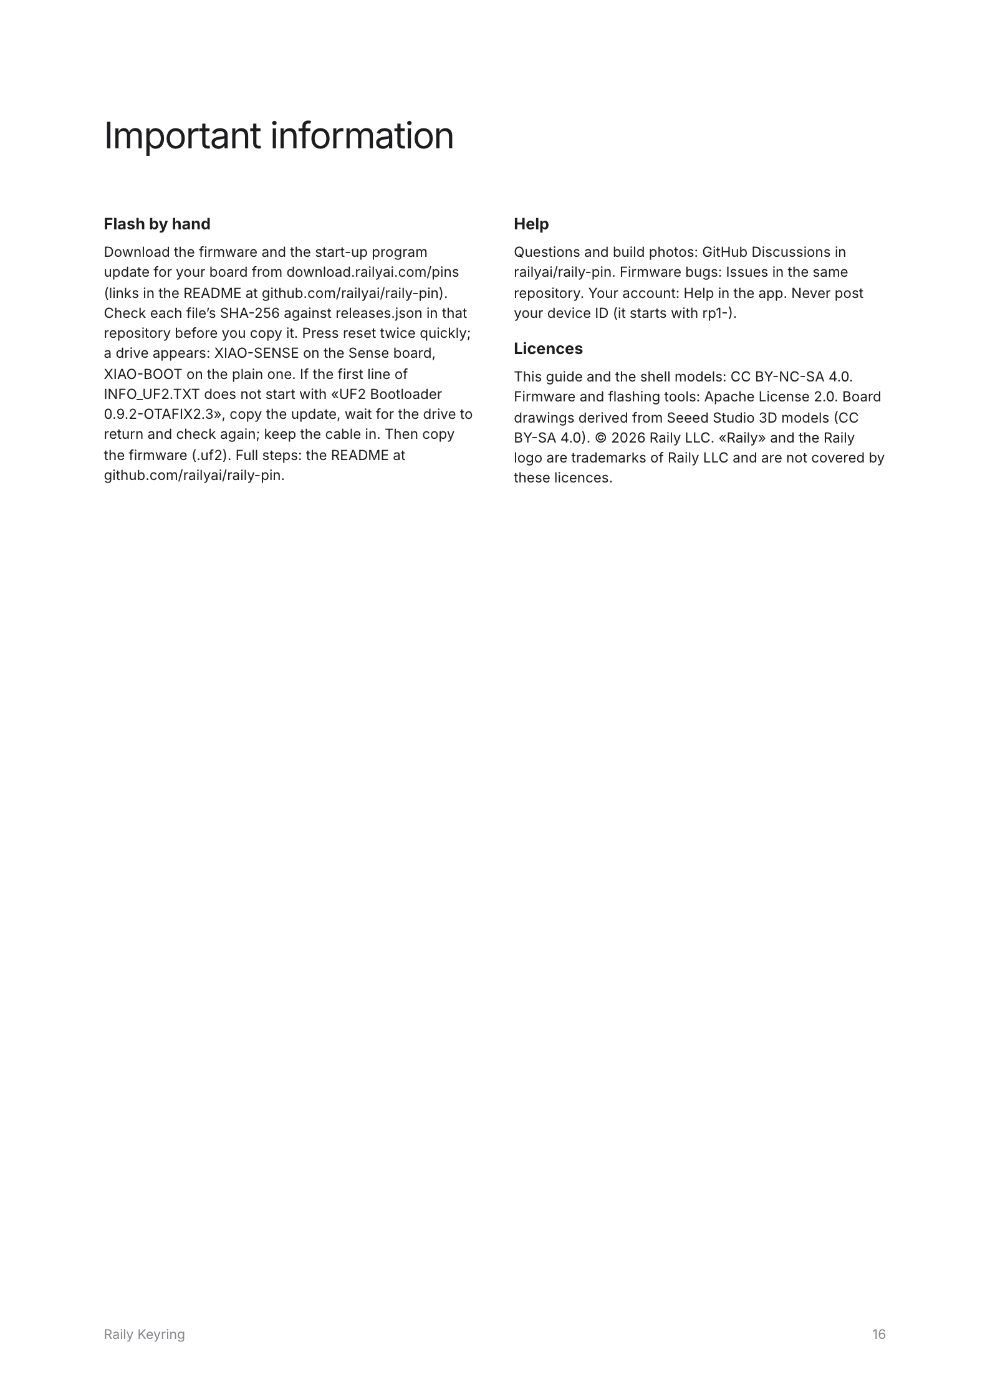
guide/pages/page-16.png
