railyai/raily-pin/published/keyring/case-3d/checkpoint-a/assembly-sheet-ru.png

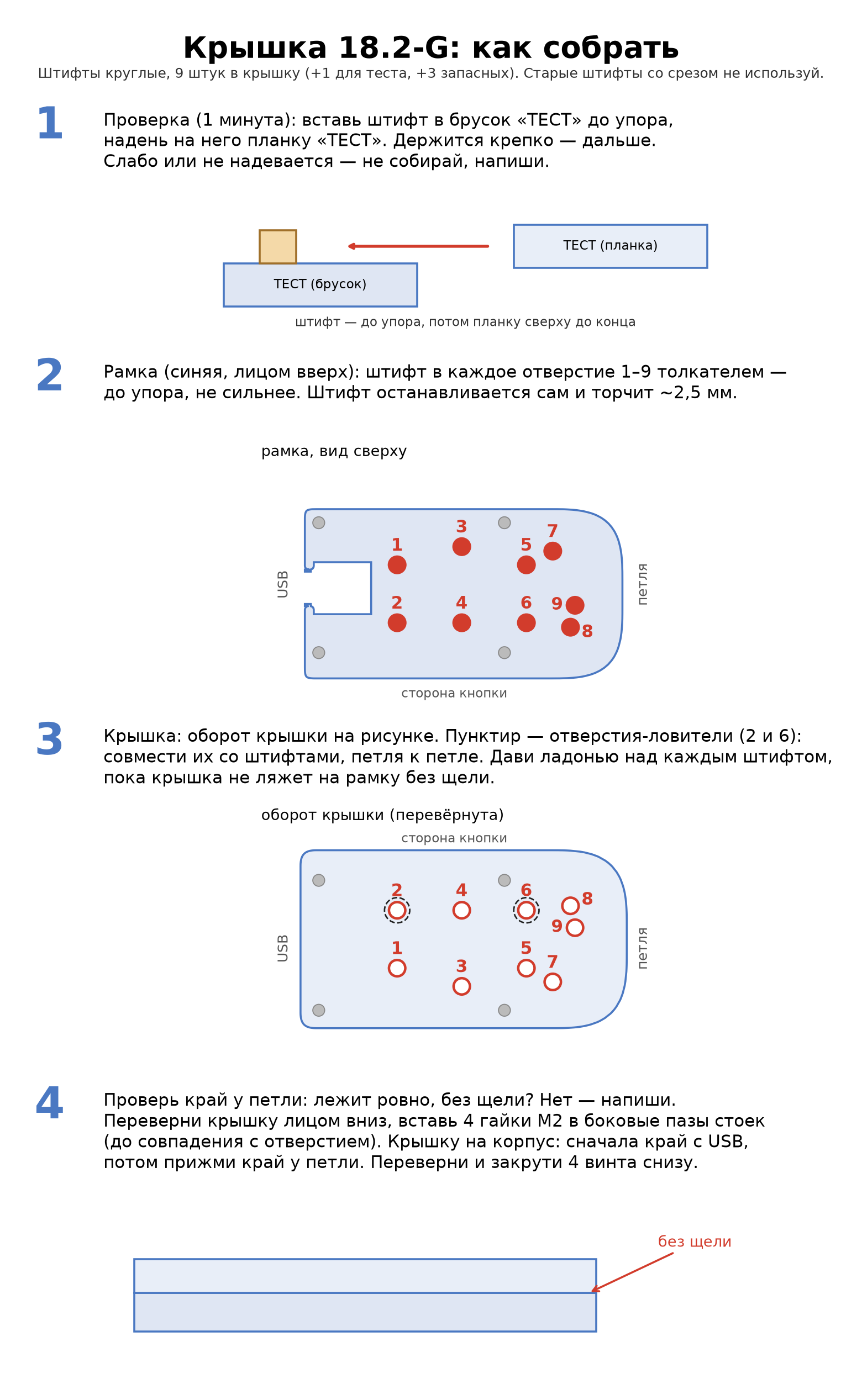
published/keyring/case-3d/checkpoint-a/assembly-sheet-ru.png
