railyai/raily-pin/published/keyring/case-3d/print/shelf-variants/preview-A-F.png

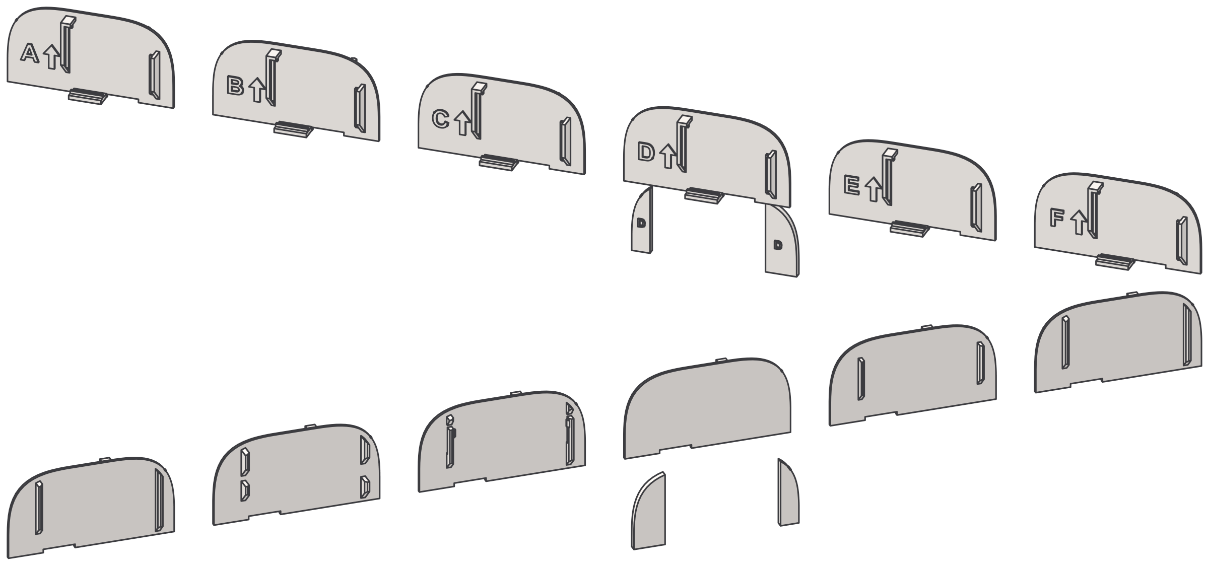
published/keyring/case-3d/print/shelf-variants/preview-A-F.png
