railyai/raily-pin/published/keyring/case-3d/print/shelf-variants/preview-C-seated-section.png

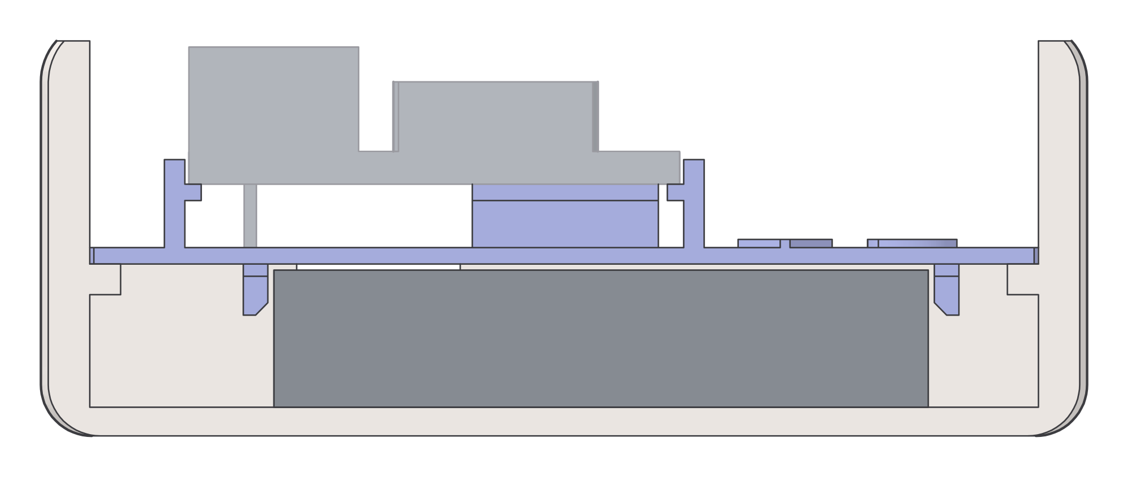
published/keyring/case-3d/print/shelf-variants/preview-C-seated-section.png
