railyai/raily-pin/published/keyring/case/guide-figures/colour-v1-front.png

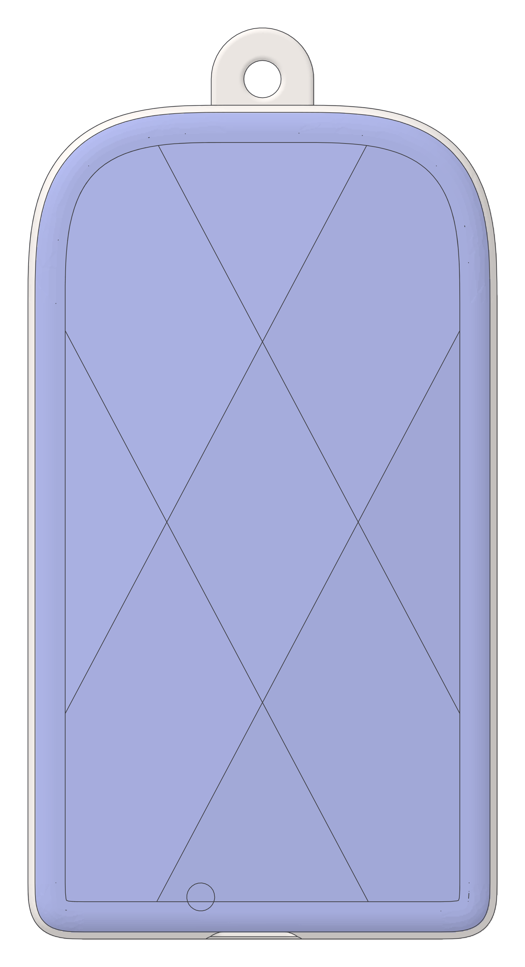
published/keyring/case/guide-figures/colour-v1-front.png
