railyai/raily-pin/published/keyring/case/guide-figures/exploded.png

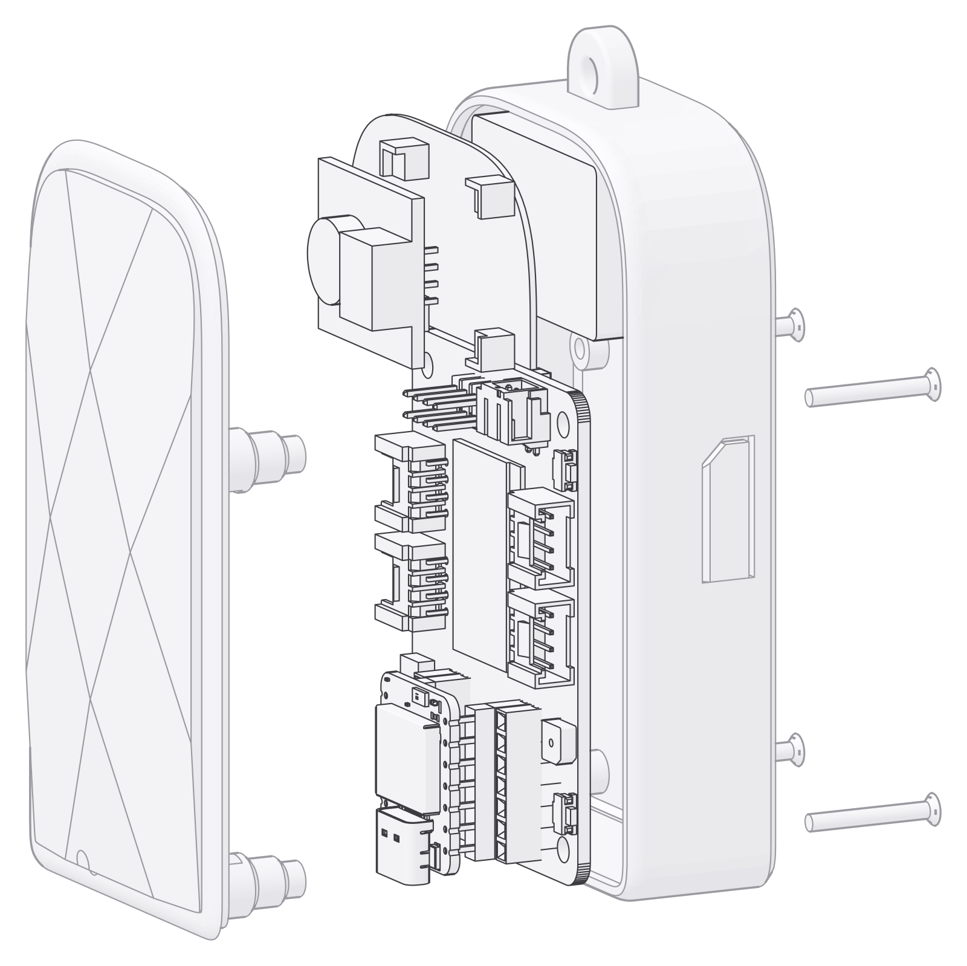
published/keyring/case/guide-figures/exploded.png
