railyai/raily-pin/published/keyring/case/guide-figures/hanging.png

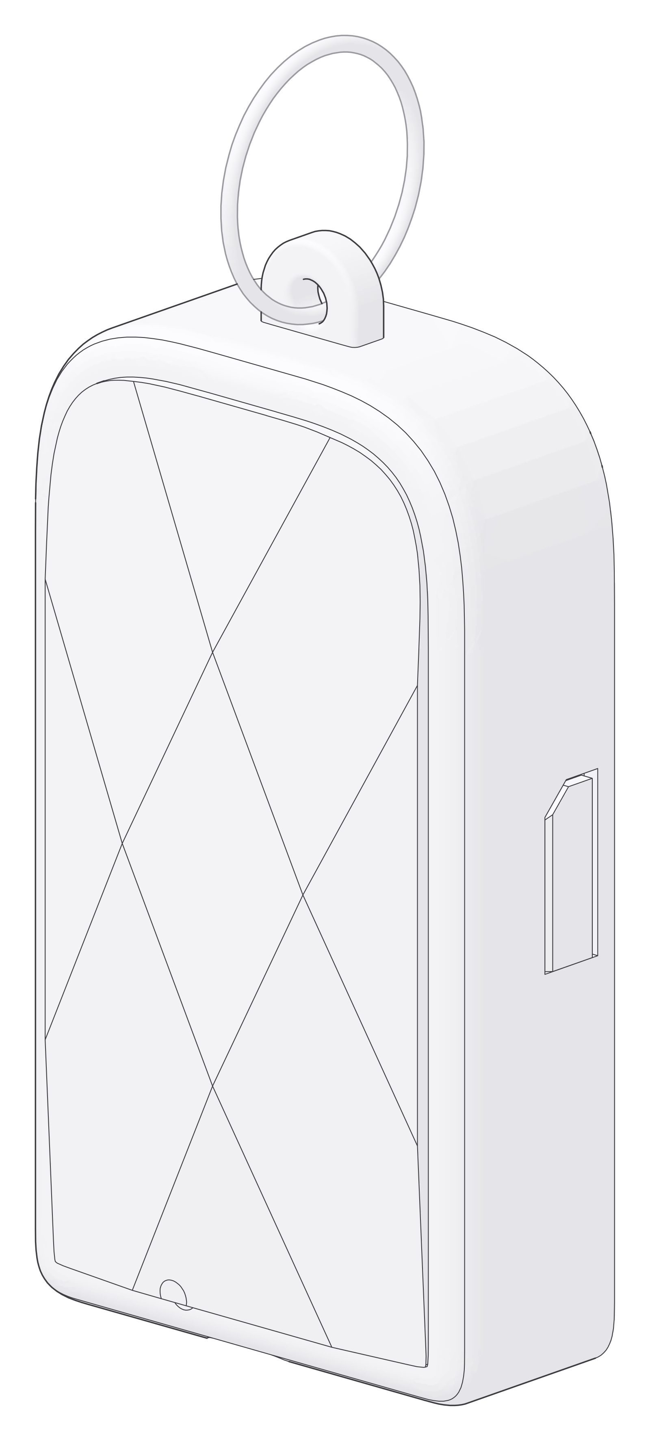
published/keyring/case/guide-figures/hanging.png
