railyai/raily-pin/published/keyring/case/guide-figures/step-2.png

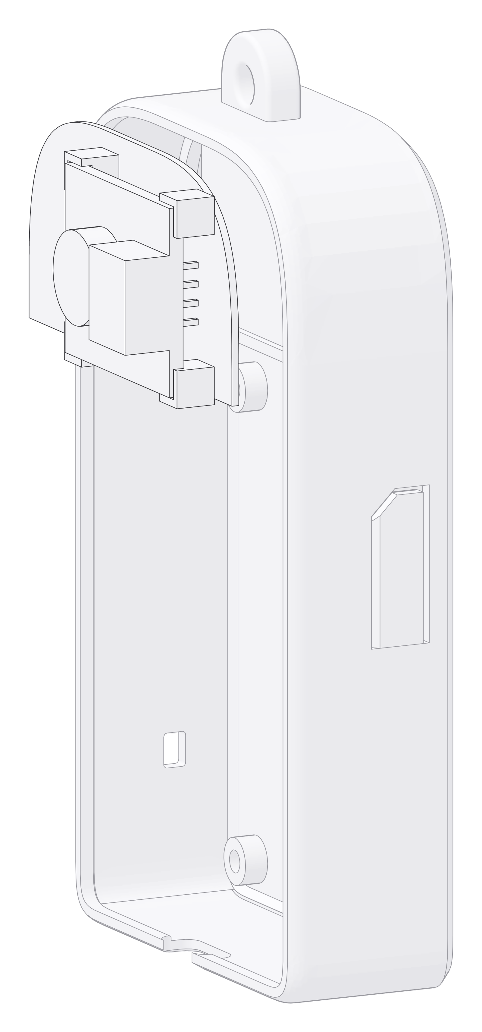
published/keyring/case/guide-figures/step-2.png
