railyai/raily-pin/published/keyring/case/guide-figures/step-3.png

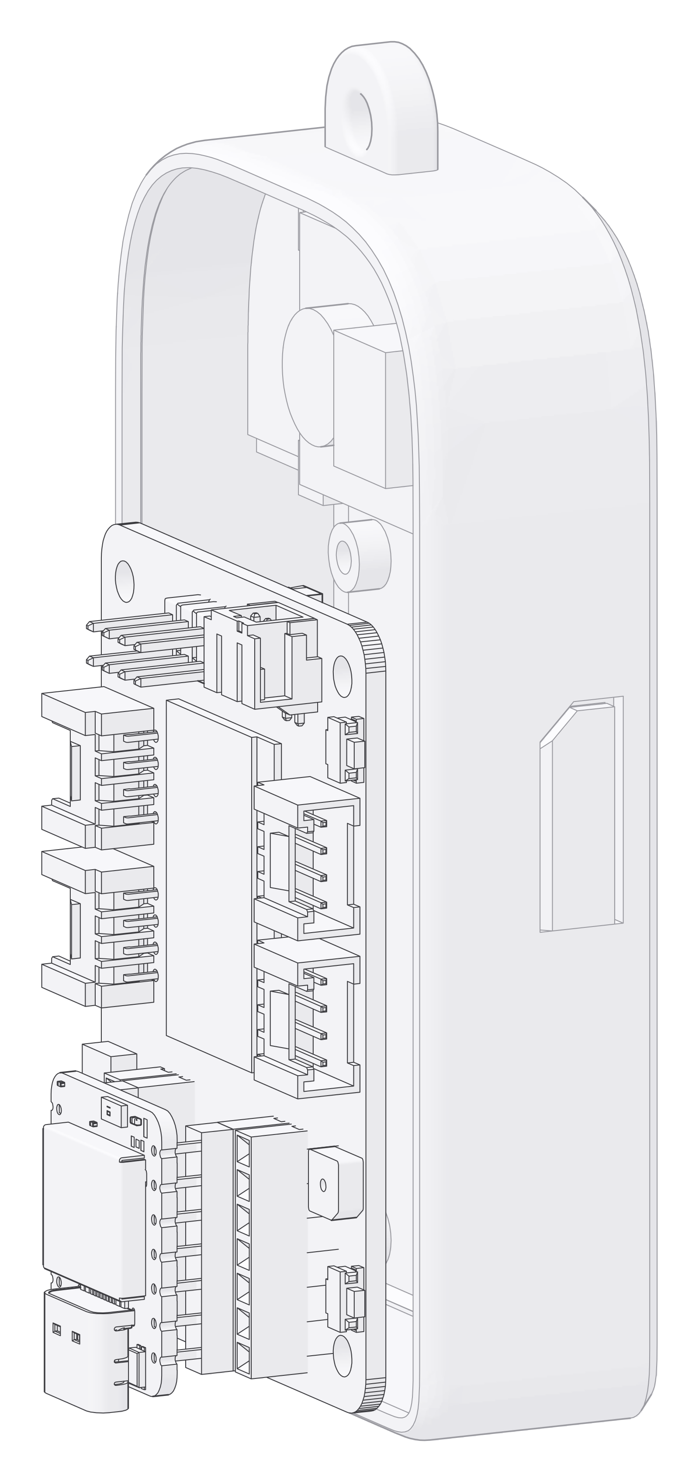
published/keyring/case/guide-figures/step-3.png
