railyai/raily-pin/published/keyring/case/guide-figures/step-4.png

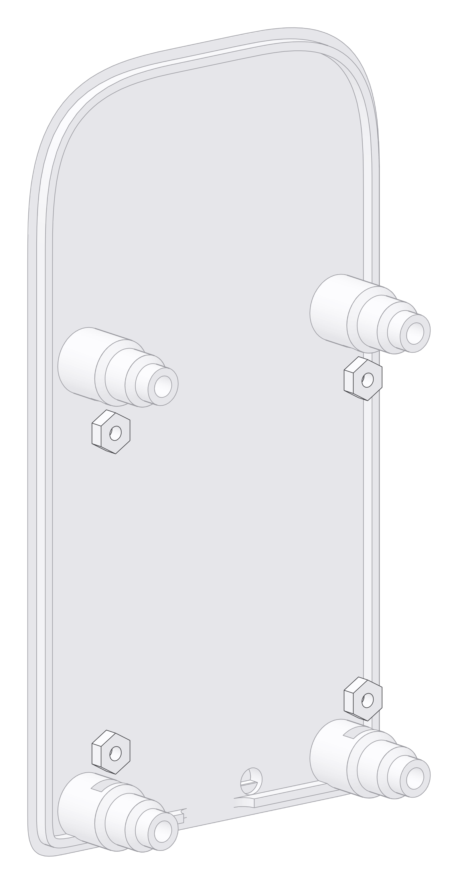
published/keyring/case/guide-figures/step-4.png
