railyai/raily-pin/published/keyring/case/guide-figures/step-5.png

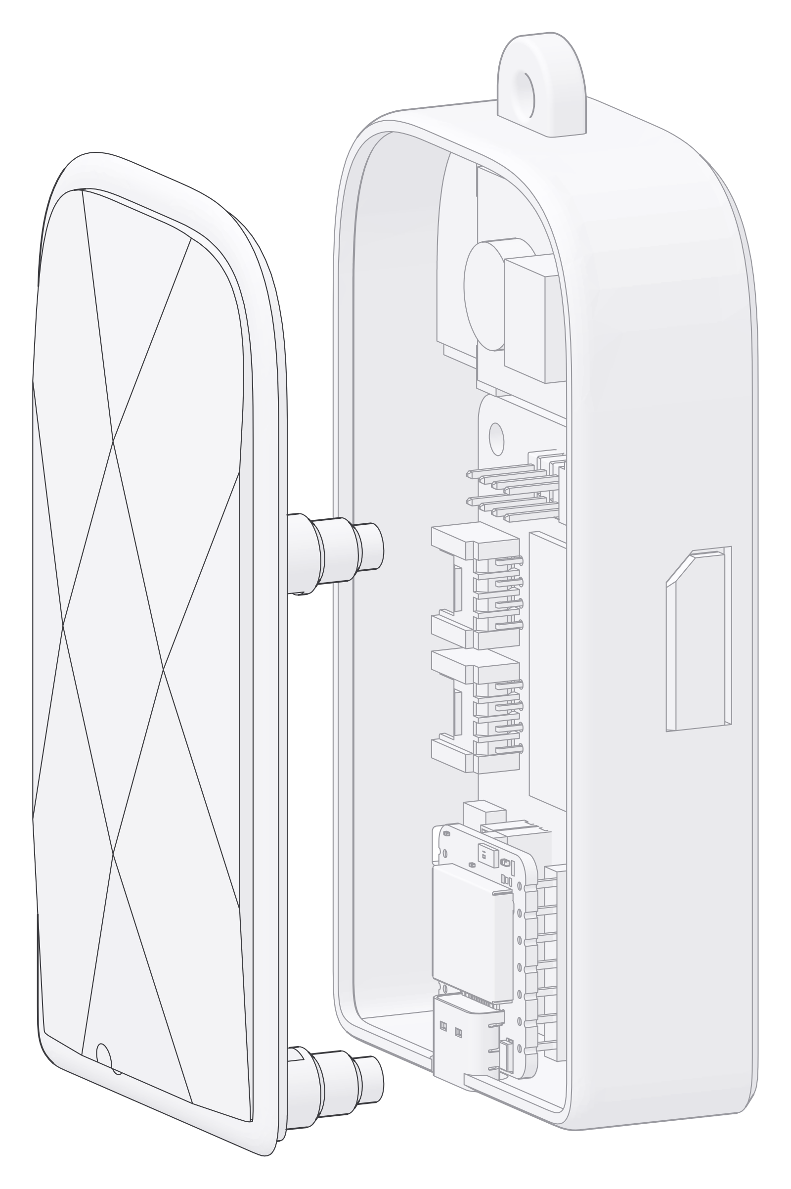
published/keyring/case/guide-figures/step-5.png
