railyai/raily-pin/published/keyring/case/guide-figures/step-5b.png

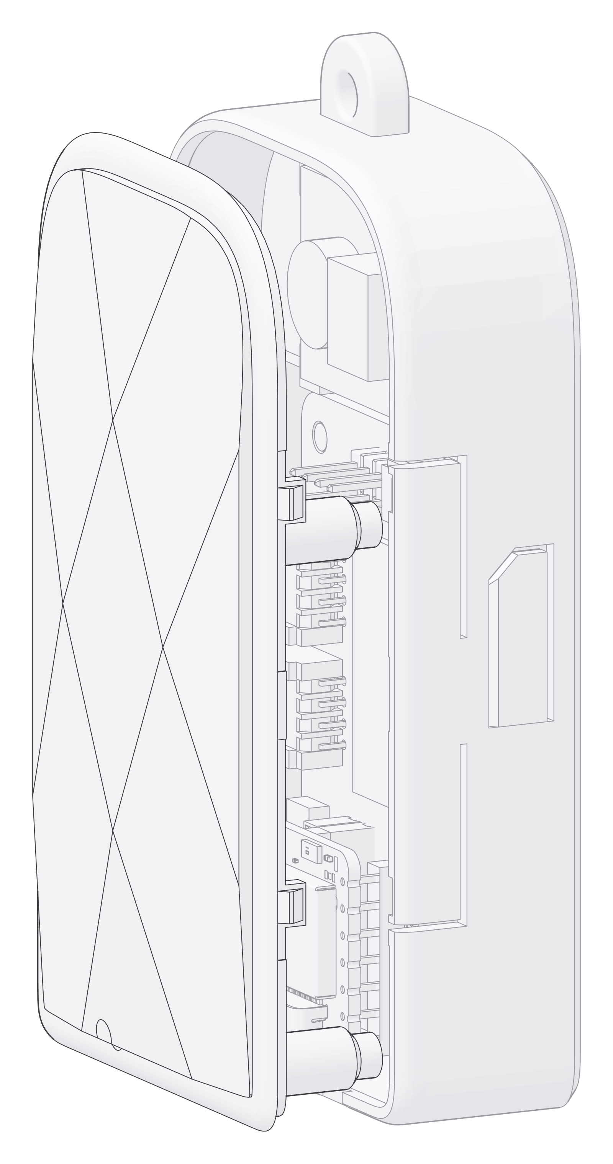
published/keyring/case/guide-figures/step-5b.png
