railyai/raily-pin/published/keyring/case/guide-figures/step-6.png

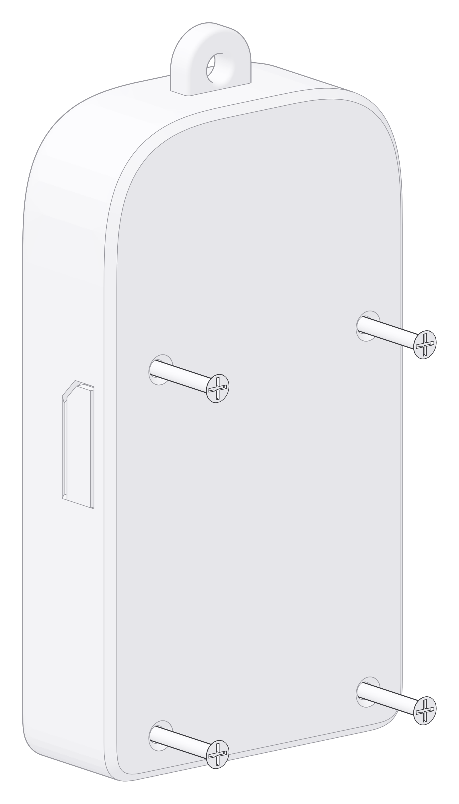
published/keyring/case/guide-figures/step-6.png
