railyai/raily-pin/firmware/tests/fixtures/vdd_discharge_2026-10-07.csv

# vddlog fw=0.2.23-qa boot=3 log=1 load=1 records=384+348 floor_mv=3000 skipped=0
t | vdd | p031 | usb
# load 1
115024 | 3382 | 2735 | 0
115084 | 3383 | 2735 | 0
115144 | 3384 | 2742 | 0
115204 | 3385 | 2738 | 0
115264 | 3384 | 2740 | 0
115324 | 3377 | 2736 | 0
115384 | 3385 | 2735 | 0
115444 | 3385 | 2736 | 0
115504 | 3387 | 2737 | 0
115564 | 3387 | 2736 | 0
115624 | 3379 | 2733 | 0
115684 | 3388 | 2741 | 0
115744 | 3388 | 2735 | 0
115804 | 3389 | 2741 | 0
115864 | 3380 | 2732 | 0
115924 | 3382 | 2738 | 0
115984 | 3368 | 2735 | 0
116044 | 3376 | 2732 | 0
116104 | 3370 | 2736 | 0
116164 | 3375 | 2729 | 0
116224 | 3379 | 2733 | 0
116284 | 3386 | 2741 | 0
116344 | 3367 | 2741 | 0
116404 | 3374 | 2734 | 0
116464 | 3372 | 2732 | 0
116524 | 3375 | 2736 | 0
116584 | 3375 | 2740 | 0
116644 | 3372 | 2735 | 0
116704 | 3377 | 2732 | 0
116764 | 3383 | 2738 | 0
116824 | 3388 | 2741 | 0
116884 | 3379 | 2731 | 0
116944 | 3377 | 2735 | 0
117004 | 3384 | 2739 | 0
117064 | 3376 | 2732 | 0
117124 | 3376 | 2738 | 0
117184 | 3382 | 2738 | 0
117244 | 3379 | 2736 | 0
117304 | 3373 | 2737 | 0
117364 | 3376 | 2737 | 0
117424 | 3381 | 2736 | 0
117484 | 3372 | 2737 | 0
117544 | 3373 | 2736 | 0
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
