railyai/raily-pin/guide/qa/jst-compare.png

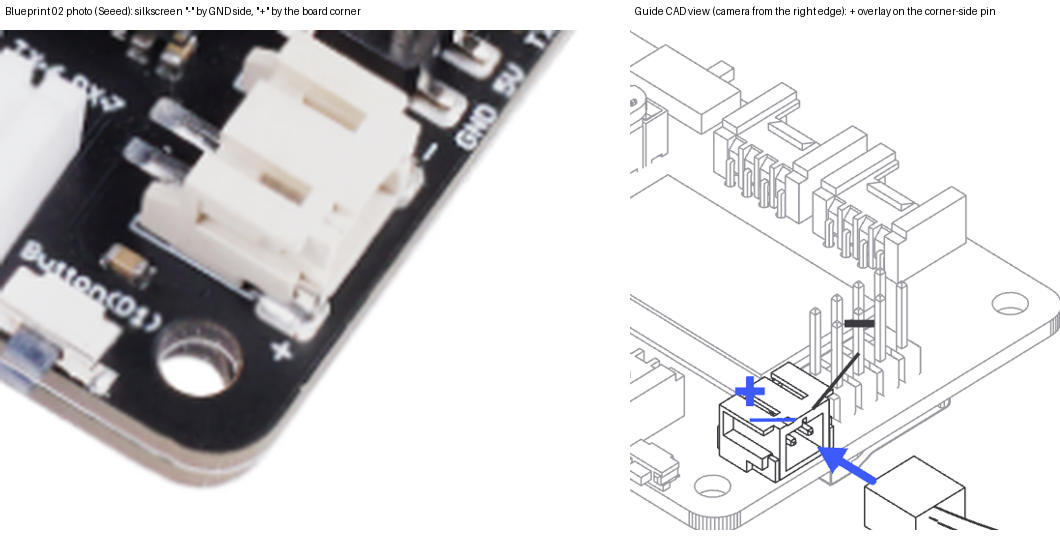
guide/qa/jst-compare.png
