railyai/raily-pin/case/keyring_case.py

#!/usr/bin/env python3
"""Raily Keyring case v1: one parametric CadQuery model.

This file is the single source of truth for the keyring case: print files
(STL/STEP), the assembly guide's line art and the Blender renders all come
from it. Every printed body is one filament region (tray, loop, cover zone 3,
front zones 1 and 2, LED spot, shelf) so a multi-colour slicer can assign them;
SCHEMES maps bodies to filaments.

Coordinates are the ones of Seeed's Expansion Board STEP (../guide/cad):
  x  long axis of the case. x min = bottom end (XIAO USB-C), x max = top end (loop)
  y  thickness. +y = front (component side, OLED, screws go in from here)
  z  width. +z = the long side with Button D1 and the Grove A0/D0 port

Every number in MEASURED comes from expansion.step / xiao.step (measure()),
every number in DATASHEET from the cited source. Clearances, walls and shape
choices are design parameters in P.

HARD RULE (owner, 2026-09-29): owner-approved geometry is frozen. Never alter an approved part (its outline, fence,
steps, posts, clearances, notches, keys) or add a feature to it without asking the lead first and getting the owner's
yes. A new version reuses the approved part's own source and parameters; any difference must be listed and approved
before it is sliced. (17.2 drifted from the approved 13.2B + 11.2 through v1.2 audit features nobody re-approved.)

Run:  python keyring_case.py measure      # the measured stack
      python keyring_case.py options      # packing options A/B/C
      python keyring_case.py variants     # corner variants a/b/c: sizes after board-corner growth
      python keyring_case.py tab          # flex-tab mechanics
      python keyring_case.py check [v]    # interference / clearance report
      python keyring_case.py stage2       # all bodies -> print/ (STL per filament + STEP), preview line art,
                                          # build/stage2 meshes for Blender, interference report
      python keyring_case.py stage2 v2    # case v2 (OLED window, thinner shell; VERSIONS) -> print/v2/, ...-v2
"""
import json
import math
import os
import sys
from dataclasses import dataclass, replace, asdict

import cadquery as cq
import numpy as np

HERE = os.path.dirname(os.path.abspath(__file__))
CAD = os.path.normpath(os.path.join(HERE, '..', 'guide', 'cad'))
PREVIEW = os.path.join(HERE, 'preview')
BUILD = os.path.join(HERE, 'build')

# ---------------------------------------------------------------- measured
# From the Seeed STEP files (CC BY-SA 4.0). measure() re-derives them.
MEASURED = dict(
    board_x=(119.50, 177.50), board_z=(-20.39, 22.11), board_r=3.00,   # PCB outline, corner radius
    pcb_y=(-3.20, -1.60),                                              # 1.6 mm PCB, top face at -1.60
    holes=[(123.49, 18.36), (173.49, 18.36), (123.49, -16.64), (173.49, -16.64)], hole_r=1.50,
    under_min_y=-6.38,        # lowest part under the board: CR1220 holder, x 142.93..155.07
    # every other part under the board (Grove connectors, microSD slot, through-hole tails) ends above this
    under_rest_y=-5.14,
    cr1220_holder=dict(x=(142.93, 155.07), z=(-8.76, 10.24)),
    xiao_top_y=9.85,          # XIAO USB-C top; XIAO on 2.54 mm header spacers on the 2.90 sockets
    usb_c=dict(x_mouth=117.96, x_back=125.26, y=(5.65, 9.85), z=(-3.58, 5.36)),  # overhangs the edge by 1.54
    # the receptacle shell at its mouth (a section of the shell solid at x 118.0..119.4): 8.94 x 3.21, its tongue
    # at y 7.90..8.60 (centre 8.25). The y 5.65 above is the mounting legs behind the XIAO PCB edge (x > 119.48).
    usb_c_shell=dict(y=(6.64, 9.85), z=(-3.58, 5.36)),
    # OLED module block: glass top y -0.60 over z -7.96..5.76; the strip z 5.76..8.54 is the lower FPC ledge (top y -1.02).
    # The STEP has no active-area face: the window is sized from the glass (DATASHEET oled_aa for the reading area).
    oled=dict(x=(141.92, 166.60), z=(-7.96, 8.54), y_top=-0.60, glass_z=(-7.96, 5.76)),
    jst=dict(x_mouth=176.89, y=(-1.59, 3.79), z=(6.89, 15.04)),        # battery socket, opening +x
    grove_a0=dict(x=(143.53, 153.53), z_mouth=21.36, y=(-1.60, 3.50)),  # A0/D0 shroud, opening +z
    switch=dict(x=(130.30, 139.12), z_min=-21.47),                      # power switch lever past the -z edge
    # Button D1: body x 166.40..171.10, y -1.99..0.31, front face z 22.01; actuator
    # x 167.78..169.73, y -1.06..-0.21, tip z 23.01 -> 1.00 mm of actuator out of the body
    button_d1=dict(x=(167.78, 169.73), y=(-1.06, -0.21), z_max=23.01, body_z=22.01, body_x=(166.40, 171.10)),
    header_pins_top_y=7.88,   # 2x4 male pins at x 170.8..174.0, z -4.0..4.2
    # power switch lever past the board edge (one position in the STEP): x 134.71..136.16, y -1.11..0.02;
    # travel assumed = lever width (1.45) toward -x, the usual for this size of slide switch
    switch_lever=dict(x=(134.71, 136.16), y=(-1.11, 0.02), z_min=-21.47, travel=1.45),
    # XIAO LEDs, posed on the board (xiao.step product names): 'USR' = the RGB user LED, 'LED' = charge LED
    xiao_rgb_led=dict(x=(121.77, 122.77), y=(6.64, 6.94), z=(-5.32, -4.32)),
    xiao_charge_led=dict(x=(119.80, 120.43), y=(6.64, 6.94), z=(-5.45, -4.18)),
)

# The real stack against the STEP pose, from the owner's fit test (2026-09-28). The Expansion Board sits on its
# standoffs at the model height (checked in the printed tray), but its XIAO sockets are about 5.5 mm tall, not the
# STEP's 4.5, and the header spacer stands about 0.5 off them: with the headers the reversed way (short ends down,
# spacer on the sockets, the XIAO soldered on the long ends, tails clipped to <= 2 mm) the XIAO sits about +1.9
# over the STEP pose (side photos, the spacer as the scale). Long ends down sits +5.7..6.0: the guide shows it as
# wrong. The design takes +2.0 (the cover clears it by clr); the window also takes +1.5 (XIAO_DY_TOL).
# Every XIAO-referenced number (USB-C receptacle, XIAO top, its LEDs) and the XIAO in board_parts() move by XIAO_DY.
XIAO_DY = float(os.environ.get('KC_XIAO_DY', '2.0'))
XIAO_DY_TOL = 0.5            # the window also takes a XIAO this much lower (P.usb_window_low)
XIAO_DY_UP = 0.0             # the cover clears a XIAO this much higher (plus clr)
for _k in ('usb_c', 'usb_c_shell', 'xiao_rgb_led', 'xiao_charge_led'):
    MEASURED[_k]['y'] = tuple(v + XIAO_DY for v in MEASURED[_k]['y'])
MEASURED['xiao_top_y'] += XIAO_DY
# The power switch's lever sits higher on its body than in the STEP: with the bare board flat on its standoffs in the
# printed tray the lever is entirely above the v1 slot (top at y 0.42), so at least +1.5; an earlier photo showed its
# bottom sliver (+1.3). The slot takes +1.0 to +2.4 (switch_slot_clr_y around +1.7).
SWITCH_DY = float(os.environ.get('KC_SWITCH_DY', '1.7'))
MEASURED['switch_lever']['y'] = tuple(v + SWITCH_DY for v in MEASURED['switch_lever']['y'])

# ---------------------------------------------------------------- datasheet
DATASHEET = dict(
    # 602030 LiPo with PCM. Largest listed envelope: EEMB LP602030, 6.7 x 20.5 x 32 mm
    # (docs/pins/eu-compliance.md, supplier table; Ufine UFX602030 is 6 x 20 x 32).
    lipo=(20.5, 32.0, 6.7),            # width, length, thickness
    # Seeed Grove Vibration Motor 105020003: 24 x 20 x 9.8 mm (Distrelec product data,
    # distrelec.ch 30069914). Split used for the model: 1.6 PCB, 5.1 Grove socket
    # (same socket as on the Expansion Board STEP), 3.1 through-hole tails.
    motor=(20.0, 24.0, 9.8),
    motor_split=(3.1, 1.6, 5.1),       # tails, pcb, socket
    grove_plug_len=7.0,                # HY2.0-4P plug body (guide/cad/parts.py, Raily Blueprints 03-06)
    grove_socket_depth=6.46,           # A0/D0 mouth 21.36 to pin wall 14.90 (STEP)
    usb_c_overmold=(12.35, 6.5),       # USB Type-C spec: max plug overmold (the v1 opening was sized for it)
    usb_c_plug_shell=(8.4, 2.6, 6.65), # USB Type-C plug metal shell, max width x height, and its length past the overmold
    # eSUN PLA-Matte Rainbow TDS (esun3d.com): flexural modulus XY 2249 MPa, Z 1783 MPa;
    # elongation at break XY 7.23 %, Z 2.26 %. Used for the flex tab (PLA family).
    pla_E_xy=1997.0, pla_elong_xy=7.23,
    # Polymaker Panchroma TDS V2.1 (polymaker.com), Matte column: density 1.37 g/cm3, Young's modulus
    # X-Y 1997 MPa (used for the flex tab since the chosen spools are Panchroma Matte). The elongation
    # at break is not in that TDS; 7.23 % is eSUN PLA-Matte's (a PLA-matte proxy).
    pm_matte_density=1.37,
    # 0.96 inch 128 x 64 SSD1306 OLED glass (Univision UG-2864HSWEG01 class): active area 21.744 x 10.864 mm,
    # viewing area 23.744 x 12.864 mm. Assumed centred on the glass block of the STEP; check on the board.
    oled_aa=(21.744, 10.864), oled_va=(23.744, 12.864),
)

# ---------------------------------------------------------------- colour
# Raily brand tokens (Brandbook 2026-09-06, 04-Color-Tokens/raily-color-tokens.json)
PALETTE = dict(deepBlue='#425FFF', railyBlue='#5B77FF', periwinkle='#8599FF', lilac='#9AABFF')
# Owner's candidate filaments (amazon.es, 1.75 mm). Hex = eSUN's published colour list
# (esun3d.com PLA+ / PLA+HS pages) unless noted. token = brand role it stands in for.
FILAMENTS = dict(
    esun_blue=dict(name='eSUN PLA+ Blue', asin='B07FQJ8LQD', hex='#01378D', token='deepBlue',
                   src='esun3d.com: BLUE #01378D, Pantone 2146 C'),
    esun_blue_purple=dict(name='eSUN PLA+ Blue Purple (Very Peri)', asin='B0BDKTH44X', hex='#6667AB', token='periwinkle',
                          src='eSUN lists it as Very Peri; render uses Pantone Very Peri 17-3938 #6667AB. '
                              'eSUN\'s page gives #22047E, far darker than the name: check the spool'),
    esun_haze_blue=dict(name='eSUN PLA+ Haze Blue', asin='B0DNMLR9PC', hex='#7AB9EF', token='lilac',
                        src='esun3d.com: HAZE BLUE #7AB9EF'),
    esun_ocean=dict(name='eSUN PLA-Matte Rainbow Ocean', asin='B0DGPSJ464',
                    stops=['#1F4F9A', '#2BA3B8', '#A8DDE0'],
                    src='no published hex; stops approximated from the product name until a sample is photographed'),
    raily_4th=dict(name='4th spool, railyBlue role (to source)', asin=None, hex='#5B77FF', token='railyBlue',
                   src='placeholder = brand token railyBlue; eSUN\'s PLA+ colour table lists a "Periwinkle blue" '
                       '(Pantone 2116 C) worth sampling'),
    # Polymaker Panchroma Matte PLA; hex and TD (transmission distance, mm) from Polymaker's
    # "HEX Codes and Transmission Distances" table (wiki.polymaker.com); Raspberry Blue from the colourway agent
    pm_cotton_white=dict(name='Polymaker Panchroma Matte Cotton White', sku='CA04016', hex='#F4EFEB', td=4.1),
    pm_charcoal_black=dict(name='Polymaker Panchroma Matte Charcoal Black', sku='CA04015', hex='#2F2E30', td=0.1),
    pm_ash_grey=dict(name='Polymaker Panchroma Matte Ash Grey', sku='CA04014', hex='#485155', td=0.1),
    pm_army_blue=dict(name='Polymaker Panchroma Matte Army Blue', sku='CA04008', hex='#2E4462', td=0.1, token='deepBlue'),
    pm_raspberry_blue=dict(name='Polymaker Panchroma Matte Raspberry Blue', sku='CA04092', hex='#5472D0', td=None,
                           token='railyBlue'),
    pm_pastel_periwinkle=dict(name='Polymaker Panchroma Matte Pastel Periwinkle', sku='CA04036', hex='#ADB4E6', td=1.5,
                              token='lilac'),
    overture_marble=dict(name='OVERTURE Marble PLA', asin='B0F8NM6788', hex='#B9B7B0', src='stone effect; not rendered'),
)


@dataclass
class P:
    layout: str = 'B'            # 'A' sandwich, 'B' end bay (owner-approved), 'C' side by side
    corner: str = 'g2'           # front silhouette: 'circle' (a), 'g2' (b), 'stadium' (c)
    corner_r: float = 9.6        # (a) circular corner radius
    g2_req: float = 15.0         # (b) circle-equivalent radius (same corner cut on the diagonal)
    g2_n: float = 3.0            # (b) superellipse exponent: n > 2 gives zero curvature at the joins (G2)
    stadium_flat: float = 2.0    # (c) straight piece left on each end
    clr: float = 0.3             # part to wall / part to part
    print_clr: float = 0.2       # printed fits (stage 2)
    wall: float = 1.6            # side walls (v1.1: the owner's pick after printing 1.0 / 1.25 / 1.6 test trays; v1 was 2.0)
    floor: float = 1.4           # rear (v1.1 = v1: the owner found 1.4-1.5 fine after the 1.0 / 1.2 test trays)
    end_wall: float = 1.25       # the USB-C end wall where it is flat (up to the top band), so the receptacle mouth can sit
                                 # usb_recess under the outer face with clr to the board edge; 0 = wall
    floor_boss: float = 1.4      # floor thickness in a ring around each countersunk screw hole (closure A)
    # thin walls under the fillets: the front fillet (3.0) reaches below the parting line and the back fillet (2.5)
    # past the floor, so a 1.25 wall would be 0.49 mm at the parting line and 0.55 across the floor corner. A band
    # inside the wall top (the cover's lip moves in by as much) and a 45 degree fillet along the floor corner keep both
    # near 1 mm. 0 = none (v1 and v2 walls do not need them)
    rim_band: float = 0.2        # extra wall thickness over the top rim_band_h of the tray wall, 45 degrees below
    rim_band_h: float = 1.5
    floor_chamfer: float = 0.8   # 45 degree fill in the floor-to-wall corner inside
    floor_boss_d: float = 8.0    # ring diameter
    g2_req_bottom: float = 4.25  # USB-C end: circle-equivalent corner radius (the loop end keeps g2_req); 0 = g2_req
    cover: float = 1.0           # front plate at the rim, over the cavity (kept as low as the lip allows)
    facet_angle: float = 7.0     # tilt of the four X-arm facets, degrees (the corner facets are steeper)
    crown: float = 0.0           # 0 = facets run all the way to the panel edge (crown follows from the angle);
                                 # > 0 = cap: the facets stop at this height and the outer field is flat
    facet_min: float = 0.15      # lowest facet height over the rim (panel corners)
    rim_w: float = 4.0           # rim band around the faceted panel
    fillet_front: float = 3.0    # pillowed rim
    fillet_back: float = 2.5     # back (build plate) edge round, used when back_chamfer is 0
    back_chamfer: float = 1.2    # v1.1: a 45 degree chamfer on the back edge instead of the round (a round on the plate
                                 # side prints as stair steps: its first layers overhang almost flat; owner photo 2026-09-28)
    jst_zone: float = 5.0        # mated JST-PH plug + lead bend past the socket mouth (verify)
    grove_zone: float = 3.5      # Grove cable bend past the plug back (verify)
    lipo_swell: float = 0.3      # headroom over the cell for swelling
    foam: float = 0.5            # foam pad (layout A, cell under the parts)
    shelf: float = 0.8           # printed shelf between cell and motor (layout B)
    lattice_fill_w: float = 0.97 # the 4 outer diamonds span this share of the faceted panel's width
    lattice_fill_h: float = 0.95 # ... and of its height (owner sketch: they reach the panel edge)
    top_hole: bool = False       # v2 centre button hole, off in v1
    top_hole_d: float = 12.0
    loop_w: float = 11.0         # keyring lug, top end
    loop_t: float = 4.0          # lug thickness (y)
    loop_hole: float = 4.0       # split ring 25 mm, wire about 1.2-1.5
    loop_gap: float = 0.8        # hole edge to the case end
    loop_web: float = 2.5        # material from hole to lug edge (>= 2 mm)
    loop_boss: float = 1.5       # the end wall behind the lug, thickened inward over the lug (above the shelf)
    low_floor: bool = True       # v1.1: the floor as high under the board as the depth allows (packing()); v1 False
    holder_pocket: float = 0.75  # floor left under the CR1220 holder's pocket (low_floor). The holder reaches 2.3 under the
                                 # board in the owner's photo (0.85 clear of the pocket), 3.18 in the STEP (0.02 clear)
    # side button: print-in-place flexure in the +z wall over Button D1
    tab_len: float = 16.0        # hinge to free end, along x (v1 14.0: the 1.25 tongue needs a longer arm for the same force)
    tab_h: float = 5.0           # tongue height (y), centred tab_dy off the D1 actuator (v1 6.0: the slit below it now
                                 # stays 1.5 mm above the back fillet, the roofed slit above it under the B latch slits)
    tab_dy: float = 0.0          # tongue centre off the actuator centre
    tab_t: float = 1.25          # tongue thickness: 3 lines of a 0.4 nozzle (v1 1.0 = 2.4 lines printed ragged)
    tab_slit: float = 0.7        # slit width (0.4 nozzle: >= 0.6 so it does not fuse)
    tab_roof: float = 45.0       # the slit above the tongue (print Z) is a 45 degree roof, not a 14 mm bridge; 0 = flat
    tab_end_chamfer: float = 2.0 # 45 degree chamfer on the tongue's free-end top corner (x-y), the slit follows; 0 = square
    tab_free: float = 2.5        # free end past the D1 centre
    nub_gap: float = 0.15        # nub to actuator tip at rest
    nub_w: float = 1.6           # nub across x (actuator is 1.95)
    nub_h: float = 0.0           # nub across y (v1: 1.4) (actuator is 0.85; taller to forgive board height tolerance); 0 = a rib
    nub_rib_margin: float = 0.3  # nub_h 0 (v1.1): the nub is a vertical rib over the whole tongue height, this far in
                                 # from its edges; it only ever meets the D1 actuator (owner check), +-1.8 mm of height
    pad: tuple = (5.5, 4.4, 0.0) # outside pad on the tongue: x, y, proud (0 = flush, body colour, no pad)
    # USB-C: the end wall is flat at the receptacle and its outer face sits usb_recess in front of the receptacle mouth;
    # the opening fits the receptacle shell (8.94 x 3.21) with clearance, so only the plug's metal shell goes in.
    # v1 had a 13.0 x 7.2 overmold-sized opening with the mouth 8.3 mm inside the outer face.
    usb_recess: float = 0.2      # receptacle mouth behind the outer face at the USB axis (target; see packing())
    usb_window: tuple = (9.8, 3.8)    # width (z) x height (y): shell + 0.43 / 0.30 per side
    usb_window_low: float = 0.5       # the window's lower edge this much lower (XIAO_DY_TOL: the lift is read from photos)
    # colour: which filament each part is printed in
    scheme: str = 'v1'           # colour scheme (SCHEMES): which filament each body gets
    front_zones: bool = False    # split the front into 3 colour zones (option; the owner chose solid fronts)
    zone_depth: float = 1.0      # front colour zones 1 and 2: skin depth under the facet surface
    # RGB LED spot in the cover, over the XIAO user LED: 'skin' (thin cover skin) or 'hole'
    led_mode: str = 'skin'
    led_d: float = 3.0           # skin spot diameter
    led_skin: float = 0.3        # skin left over the LED (owner, 2026-09-28: 0.3 shows the LED clearly better than 0.4)
    led_hole_d: float = 2.0      # through-hole diameter (led_mode 'hole')
    # closure (owner, 2026-09-28: keep the front clean). 'back' = A: M2 countersunk screws from the back into
    # nuts in side slots of the cover pillars; 'snap' = B: screwless, four cantilever latches in the long walls;
    # 'front' = the first version (screws from the front into nuts in the back), kept as an option.
    closure: str = 'back'
    # A: ISO 7046-1 M2 x 16 countersunk, cross recess H0 (dk 3.8, k 1.2; the length includes the head)
    back_screw_len: float = 16.0
    csk_d: float = 4.1           # 90 degree countersink at the back face (dk 3.8 + 0.3)
    nut_slot_clr: float = 0.1    # slot width = nut AF + this: a light push fit, so the nut stays while the cover is turned
    nut_boss_d: float = 7.4      # pillar diameter around the nut slot (from 1 mm under the slot up to the front plate)
    nut_tip_past: float = 0.5    # screw tip past the nut
    # B: cantilever latches (tongues cut in the long walls, like the side button), bumps on the cover
    latch_x: tuple = (140.0, 178.0)   # bump centres along x, on both long walls (straight part of the outline)
    latch_len: float = 14.0      # hinge to bump centre
    latch_y0: float = 5.8        # tongue bottom; the tongue runs up to the wall top (v1 5.0; v1.1 clears the button's roofed slit)
    latch_t: float = 2.0         # latch tongue thickness: where the wall is thinner, a pad inside the wall makes it up locally
    latch_e: float = 0.6         # engagement = tongue deflection while the bump passes
    latch_bump_w: float = 3.0    # bump length along x
    latch_catch_h: float = 3.6   # catch block under the front plate (carries the bump)
    latch_catch_t: float = 1.6   # catch block thickness (z)
    latch_ret_deg: float = 45.0  # retention face angle from the pull direction (45: both parts print without support)
    latch_lead_deg: float = 30.0 # lead-in face angle
    latch_mu: float = 0.35       # PLA on PLA friction (assumed, not in the TDS; see snap_mechanics for the range)
    pry_notch: tuple = (6.0, 1.0, 9.5)  # width (z), depth (y), start z: pry notch in the bottom end, beside USB-C
    pin_d: float = 2.6           # B: locating pins on the standoffs, into the board holes (3.0)
    # fastening 'front': M2 screws from the front, through the board holes, into nuts in the back
    screw_len: float = 16.0      # ISO 1207 M2 x 16 (cheese head dk 3.8, k 1.3)
    screw_tip: float = 0.1       # tip stops this far inside the back face
    screw_clear: float = 2.4
    cbore_d: float = 4.2         # head counterbore
    nut_af: float = 4.0          # ISO 4032 M2: s 4.0, m 1.6
    nut_m: float = 1.6
    standoff_d: float = 5.0      # tray standoffs under the PCB
    pillar_d_top: float = 5.8    # cover pillars above y pillar_step_y (clears JST by 0.4)
    pillar_d_low: float = 4.2    # below the step (clears Reset and D1 by 0.4)
    pillar_step_y: float = 0.7   # above the button tops (0.31) + 0.4
    pillar_gap: float = 0.1      # pillar to PCB top
    lip_w: float = 1.0           # cover lip into the tray
    lip_h: float = 1.5
    # bay
    rib_t: float = 1.2           # cell stop rib at the start of the bay
    lead_notch: tuple = (8.0, 4.0)   # notch for the cell leads: width (z), depth (y)
    ledge_w: float = 1.5
    ledge_h: float = 1.5
    motor_post: float = 3.0      # corner posts under the motor PCB (tails hang between them); bay_hold False only
    # ---- bay retention (v1.1 follow-up, the owner's fit tests 2026-09-28). The real Grove Vibration Motor module is a
    # 20 x 20 mm PCB (the 24 mm datasheet length is its envelope); its Grove socket's through-hole pins stick 2 mm under it.
    bay_hold: bool = True        # pads, slide-in shelf with the corner hook leaf, motor rails (False = the v1 posts)
    motor_l: float = 20.0        # motor PCB length along z (Grove socket on the +z edge)
    cell_len: tuple = (30.1, 31.6)   # real cell length with its protection board (EEMB LP502030, THOR 602030 class)
    cell_t: tuple = (5.0, 6.7)   # cell thickness range
    pad_h: float = 1.8           # cell end pads on the bay floor, printed with the tray (both rigid)
    pad_wall_clr: float = 0.3    # pad outline off the bay wall (they sit under the ledges)
    pad_x0: float = 183.3        # pads start here: the rib-side corner stays free for the cell leads
    shelf_slide: float = 1.5     # the shelf goes in this far toward the rib, then slides home under the far lip
    shelf_lip_w: float = 1.4     # far lip over the shelf edge (45 degree underside; the shelf edge has a 45 degree chamfer)
    shelf_lip_z: float = 11.0    # far lip spans z within +- this of the bay centre line (the straighter part of the end)
    detent_h: float = 0.4        # detent bump on the rib top: the shelf edge drops past it (click) at home
    # v1.2 (no support anywhere): the shelf prints standing on its rib-side edge, so every spring is a (y, z) profile
    # bending in the layer plane. One leaf in the shelf plane runs along z (root by the -z motor rail, free end over the
    # cell's -z end); a hook under its free end presses the cell's -z top corner on a 45 degree face: down onto the
    # floor and +z against the rigid +z pad. Length and thickness both lift the leaf.
    leaf_x: tuple = (None, 194.1)   # leaf across x: from the shelf's rib-side edge to here
    leaf_z: tuple = (-15.8, -1.6)   # leaf free end (the hook's -z face) and root
    leaf_slit: float = 0.6
    hook_x0: float = 183.8       # hook starts here (clear of the rib when the shelf drops in 1.5 short), 45 degree lead
    hook_pre: float = 0.3        # preload on the shortest, thinnest cell, normal to the hook face
    rail_lip: float = 0.6        # motor rails: top lip over the PCB edge (45 degree underside), clearance rail_clr
    rail_clr: float = 0.2
    mark_h: float = 0.5          # the orientation mark: raised on the shelf top
    under_fence: tuple = None    # #13: (mode 'full' | 'ends' | 'ends+mid', height, tab width) under the shelf edge
    fence_t: float = 1.25        # #13: fence / tab thickness across x (3 lines)
    fence_lead: float = 0.3      # #13: 45 degree lead-in on the fence's free edge, partition side
    seat_posts: bool = True      # v1.1 seat posts on the shelf top (#13 prints top down: no posts)
    top_label_deboss: float = 0.0   # > 0: the top label is cut this deep instead of raised (#13: the top is the bed face)
    under_depth: float = 0.41    # the part number's depth in the shelf underside
    top_chamfer: float = 0.0     # 45 degree chamfer round the shelf top's edge (#13: the bed face, elephant foot)
    # ---- #10 (v1.2 at the owner's width option 3; lead + independent audit, 2026-09-28). Defaults keep v1.
    len_extra: float = 0.0       # extra length at the loop end (the owner's 89.5)
    shelf_clr: float = None      # shelf outline to the tray (None = print_clr; the owner asked >= 0.3)
    motor_drop: float = 0.0      # bay_hold: the motor PCB this much lower (underside at the socket pins + 0.3)
    motor_dx: float = 0.0        # bay_hold: the motor this much toward the loop (room for the -x click bump)
    floor_top: float = None      # low_floor: the floor top under the board fixed here (None = as low as the stack needs)
    motor_pins: float = 2.0      # Grove socket pins under the motor PCB (#11 fit: 1.6)
    bay_len: float = None        # rigid bay between the cell pads along z (None = the longest cell; the leaf presses)
    bay_leaf: bool = True        # the v1.2 spring leaf with its hook (audit: it cannot work; #10 drops it)
    bay_detent: bool = True      # detent bump on the rib top for the slide-home shelf
    motor_retain: bool = False   # -x click bumps, +x corner stops clear of the ears, no lip over the rails
    socket_gap: float = 11.0     # +z rail gap in front of the Grove socket (the plug overlaps the fence)
    lip_center: bool = False     # far lip centred on the case axis (v1: on z = 0)
    shelf_key: tuple = None      # (x length, z depth): key on the +z ledge wall, the shelf's notch on that side only
    nail_dip: float = 0.0        # a dip this deep in the rib top by the shelf edge: a fingernail lifts the shelf there
    ledge_45: bool = False       # ledges with 45 degree undersides (the tray prints them without overhang)
    loop_gusset: bool = False    # 45 degree gusset under the loop lug
    floor_arrow: str = None      # cut into the bay floor (e.g. 'провода →'): the cell's lead end
    board_locate: bool = False   # -z pads (the board edge sits switch_wall_clr off the wall) + +z crush ribs
    crush: float = 0.1           # crush rib interference with the board edge
    led_land: float = 0.0        # a flat land of this diameter round the LED spot, so the skin is one flat piece
    pillar_roofs: bool = False   # 90 degree cone at the blind screw end, 45 degree roof over the nut pocket and slot
    flat_top: bool = False       # flat front, 45 degree front chamfer (front_chamfer): the cover prints face down
    front_chamfer: float = 1.2
    crown_style: str = 'facets'  # 'pillow' (#16C): a smooth dome over the same panel outline, the same peak, no creases
    crease_r: float = 0.0        # round the crown's creases (facet to facet, facet to diamond) with this radius (#14C)
    crown_shell: float = 0.0     # > 0: the crown is a shell this thick (measured vertically), not a solid wedge (weight)
    boss_slim: bool = False      # nut boss only round the nut (+ a 45 degree cone back to the pillar), not to the ceiling
    cover_fins: float = 0.0      # > 0: designed breakaway fins under the cover's ceiling at this pitch (crown-up print)
    tab_square: bool = False     # the tongue's top edge flat (no 45 degree lean, no end chamfer): no one-line island
    tab_ties: int = 0            # breakaway ties across the lower slit (0.4 x the inner 0.6), 4 mm apart from the hinge
    tab_end_ties: bool = False   # #9 B1 (owner's pick): one 0.45 tie across the end slit at mid height, inner 0.5
    tab_tie_w: float = 0.4       # lower-slit tie width along the tongue (the slicer must see it as a support column)
    led_normal: bool = False     # the LED pocket's ceiling follows the outer face at led_skin (normal, not vertical), the
    led_body: bool = True        # outside untouched; led_body False: no separate skin body (no perimeter ring on the face)
    led_skin_check: bool = True  # assert the skin range (False: report only, for option renders)
    led_grow: float = 1.45       # the 26-direction Minkowski undershoots between directions: grow r = led_skin x this
    motor_rot180: bool = False   # the module turned 180 deg on the seat (owner, P10 fit): J1 on the -x (board) side,
                                 # the coin under the hold-down bar; J1 / coin positions from the photos (to be measured)
    hold_feet: float = None      # 10.3b: feet from the hold-down bar down to the motor PCB top + this (either side of the coin)
    shelf_ribs: bool = False     # 10.2C (owner: one piece, the 13.2B fence + the 11.2 posts): prints top up; designed
                                 # breakaway ribs under the plate (one line, 0.2 gap), their own body, snapped off after
    hold_legs: bool = False      # 10.3b: legs from the hold-down bar's ends down to the shelf top (+0.2)
    motor_kind: str = 'grove'    # 'da7280': check() takes the DA7280 on shelf 17.3c and the battery socket / plug envelope
    hold_down: bool = True       # False (#18.1e, DA7280 on 17.3c): no hold-down bar, boss or legs at all (pinned board)
    # 10.3b generic hold-down boss under the bar centre (retune these for a new motor module; hold_feet is the old name)
    hold_boss: float = None      # gap over the target plane (None: no boss)
    hold_boss_w: float = 10.0    # boss width across z, centred on the module
    hold_boss_y: float = None    # target plane (None: the module PCB top); e.g. the seat-post tops for another module
    hold_boss_gaps: tuple = None # per-foot gap over the target plane, in z order after the keep-out split (None: hold_boss)
    hold_boss_keep: tuple = ()   # z bands off the module centre kept clear (a part under the bar, e.g. the coin)
    motor_dz: float = 0.0        # the module's as-built z offset from its packed place (17.2b holds it in the exact 11.2
                                 # posts, 0.69 toward -z of the v1.3 axis); moves the envelope in check and the frame's feet
    coin_at: tuple = None        # motor_rot180: the coin's centre off the module centre (dx, dz); None = (2.0, 0.0)
    extra_dowels: tuple = ()     # 18.3 (owner, 2026-09-29): more dowels (x, z, web_x): a boss r 3 under the line in the
                                 # frame, a web from it to x = web_x (None: none), the same holes and lead-ins as the posts
    usb_bar_x: float = None      # 18.3b: a crossbar lip to lip at this x, t_sp under the line (the USB-end dowels' bosses)
    face_bosses: bool = False    # #20 (owner, 2026-09-29): square bosses under 10.3a's back at the 4 screws carry the M2 nuts
                                 # (the frame pillars' nut bosses move into the face), so the screws clamp the face itself
    face_boss_w: float = 7.0     # the boss diameter: walls 1.13 at the nut's corners, 1.45 at its flats
    cover_onepiece: bool = False # #19 (owner, 2026-09-29): 10.3a + 10.3b as ONE part (no dowels), so the 4 screws clamp the
                                 # whole cover; printed crown up on the pillar tips over designed breakaway fins (cover_fins)
                                 # plus a one-line fin ring under the lip
    ear_out: float = 2.0         # the motor module's M2 ears past the PCB edge (the envelope in check)
    mark_outside: bool = False   # #17: the tray number on the outside bottom (read with the keyring flipped, loop up)
    loop_support: bool = False   # paint the slicer's grid support under the loop (as #7 printed) when it has no fins
    partition_lip: float = 0.0   # #17 option D: a lip this tall on the partition top stops the one-piece shelf's edge
                                 # (0.2 play); lowered to 0.2 under anything of the shelf that hangs over the partition
    hold_legs_z: tuple = None    # the frame legs' z spans; None = 3..7 off the motor module's sides
    shelf_support: bool = False  # 17.2: paint the slicer's grid support under the one-piece shelf's plate (10.2C's ribs failed)
    face_shell: str = ''         # 10.3a slicer shell: 'G1' = build_bambu SHELL_G1 (10% gyroid, 2 bottom, 6 top at 0.08, ironing)
    port_pocket: float = 0.0     # 10.2 Grove fit: a pocket this deep in the +z wall behind the A0/D0 plug (wall >= 0.8 left);
                                 # the UART plug has the D1 tongue behind it, so it gets width (grove_zone) only
    motor_posts: bool = False    # bay_hold: the #11 seat (4 corner posts, owner-proven) instead of the v1.2 rails
    rib_teeth: tuple = None      # (width z, height): teeth on the partition top at the cell ends; the shelf edge stops on them
    xiao_pocket: float = 0.0     # a recess this deep in the cover's ceiling over the XIAO (more margin over its +2.0 lift)
    ceil_margin: float = 0.0     # more room over the XIAO's +2.0 lift: the parting line this much higher (cover thinner)
    loop_boss_flat: bool = False # the #7 nub over the shelf's far edge: flat underside (owner: it printed great, holds the shelf)
    far_lip: bool = True         # bay_hold: the v1.2 far lip + the shelf's far-edge wedge (None of it on #7)
    seat_split: bool = False     # the #11 posts as their own part (10.4) on a ring, sunk seat_groove into the shelf top
    seat_groove: float = 0.4
    shelf_edge_clr: float = None # the shelf's partition-side edge off the partition (None = shelf_clr); 13.2B: 0.2
    fence_lead_b: float = 0.0    # 45 degree chamfer on the fence's battery-side bottom edge (pushes the cell clear)
    ledge_cell_trim: bool = False  # trim the side ledges where the thickest cell lies clear of the fence
    cover_split: bool = False    # 10.3a face plate (above the parting line) + 10.3b frame (lip, pillars, spine), 2 dowels
    peg_clr: float = 0.1         # dowel hole clearance per side: 0.10 (holes 3.20) validated by #15 (owner, 2026-09-29)
    peg_d: float = 3.0
    peg_depth: float = 2.5       # in each half
    peg_clr_face: float = None   # #18.1 (owner: #18's six dowels had to be hammered in): the face holes' clearance (None: peg_clr)
    peg_lead: float = 0.3        # 45 degree lead-in at each dowel hole's mouth (#18.1: 0.5)
    dowel_blocks: bool = False   # #18.1: the loop-end -z dowel boss (it broke on #18) joined to the bar by a solid block,
                                 # full depth where it clears the coin by >= 1.0, stepped over the coin's edge
    proto_label: str = None      # the part number on the cover halves, instead of '<proto>.3' (e.g. '18.1-3')
    frame_plate: float = None    # #18.1 (owner): the frame's lattice filled to a plate t_sp (0.8) under the line from this x
                                 # to the loop end (the USB end stays open over the XIAO); windows in frame_windows
    frame_windows: tuple = ()    # (x0, x1, z0, z1) cut out of that plate
    face_label_x: float = 140.0  # the face label's centre x
    centre_dowels: bool = True   # the two centre dowel posts (152 / 172 on the axis); #18.1b drops them
    # #18.1c: the motor module's connector, as named numbers (the Grove vibration module is temporary: the final motor
    # changes only these). Its Grove header stands motor_conn_h over the PCB (Seeed 110990030, 1125S-4P vertical DIP:
    # 8.6 body), the cable plug motor_plug_proud over it (estimate). The face gets a pocket over motor_conn_xz (x0, x1,
    # dz0, dz1 off the module centre) as deep as face_pocket_skin allows, in face_pocket_step terraces (flat bridges)
    motor_conn_h: float = 8.6
    motor_plug_proud: float = 1.0
    motor_conn_xz: tuple = None
    face_pocket_skin: float = 0.8
    face_pocket_step: float = 0.24
    dowel_locators: tuple = ()   # #18.1c: (round (x, z), slotted (x, z)): the face holes there keep peg_clr_face; the
    peg_clr_loose: float = None  # slot runs +-peg_slot along x; every other face hole gets peg_clr_loose per side
    peg_slot: float = 0.3
    face_screws: tuple = ()      # #22 (owner, 2026-09-30): the face held to the frame by hidden self-tapping screws from
                                 # under the frame plate, no dowels: (x, z) of each; face_screw = (length, head d, head k,
                                 # pilot d, clearance d, locator clearance d, counterbore d, boss d, max engagement)
    face_screw: tuple = (4.5, 4.2, 1.8, 1.7, 2.5, 2.25, 4.6, 6.6, 2.4)   # DIN 7981 C ST2.2 x 4.5 (A2), PLA pilot 1.7
    face_screw_locators: tuple = ()   # the (x, z) whose frame hole is the snug locator clearance
    dowel_sprue: bool = False    # #18.1c (owner): the dowels printed standing on a carrier (a model-kit sprue, twice the
                                 # count) with a small tab on each D-flat's base, plus a pusher; not loose on the plate
    peg_ribs: tuple = None       # #18.1c: the non-locator face holes as crush-rib holes (bore d, rib-tip d, rib width, count):
                                 # the bore clears the position drift, the ribs keep the grip (they crush where they touch)
    short_dowels: tuple = ()     # #18.1b: USB-end dowels where the face is thin: (x, z, rib_to_x, rib_to_z) - a post like the
                                 # others, a rib (1.2 wide, lip_h deep) to the screw pillar at (rib_to_x, rib_to_z)
    short_face_depth: float = 1.5   # their face hole depth (the face is ~2.4 there: 0.9 skin)
    short_len: float = 4.0       # their dowel length (the rest sits in the frame post)
    short_lead: float = 0.3      # their lead-in (more straight grip than 0.5)
    # #18.1d (owner, 2026-09-30: the end dowels sank, the face came off there): the dowel bottoms in a blind frame hole,
    # so the frame depth sets the protrusion P = dowel - frame depth; the face hole is P + 0.04 (one layer rounding; 18.1c
    # had 0 and seated flush). Real grip = P - 0.3 (dowel end chamfer) - rib_lead. None = the older rules
    peg_face_d: float = None     # face / frame hole depth of the extra (middle) dowels and the locators (None: peg_depth)
    peg_frame_d: float = None
    short_frame_d: float = None  # frame hole depth of the corner (short_dowels) positions (None: short_len - short_face_depth);
                                 # a tuple: one per short_dowels entry
    short_face_ds: tuple = ()    # the corner face hole depths, one per short_dowels entry (() : short_face_depth)
    sprue_pusher: bool = True    # dowel_sprue: the pusher goes on the same plate (#18.1d: the owner has one already)
    short_post_r: tuple = ()     # their radius, one per short_dowels entry (() : 3.0)
    short_post_d: tuple = ()     # the corner posts' depth under the line, one per short_dowels entry (() : frame + 0.6)
    rib_lead: float = None       # the ribbed face holes' mouth cone and rib start (None: the hole's lead)
    frame_lead: float = None     # every frame hole's mouth cone (None: the hole's lead)
    pusher_cups: tuple = (1.5,)  # the pusher's cup depth at each end (= the protrusion it leaves when its rim meets the frame)
    mid_post_d: float = 3.2      # the middle (extra_dowels) posts' depth under the line
    post_trims: tuple = ()       # 18.2-B: ((x, z, dy), ...) a dowel post this much shorter (its frame hole then runs through)
    sml_sprues: tuple = ()       # 18.2-B: ((letter, dowel d), ...) one labelled 10-dowel sprue per size instead of the one sprue
    sprue_spares: int = None     # dowels on the sprue = the cover's count + this (+1 for test_joint); None: twice the count
    test_joint: bool = False     # 18.2-G (lead, 2026-09-30): the plate also carries one labelled 'ТЕСТ' joint (a frame block
                                 # with one stop hole + a face tab with one ribbed hole, this version's exact numbers)
    dowel_flat: float = 0.3      # the sprue dowels' D-flat depth (#15: vents a blind hole). 0 = round (#18.1e: a flat facing
                                 # one of a face hole's 3 ribs takes that rib out, 0.41 of radial play: the fit is a lottery)
    frame_neck: float = None     # #18.1e: every frame hole ends in a through neck this wide: the dowel's end (Ø2.4 after its
                                 # 0.3 chamfer) stops on the ledge, carried by the post's wall, not by a thin floor
    usb_face_clean: bool = False # the USB window and its lead-in cut the cover only below the line (P10e: they notched the
                                 # face's edge above the window, which the face does not need: the window top is the line)
    face_back_chamfer: float = 0.0   # 45 degree chamfer round 10.3a's back (bed) perimeter; the frame lip's gets 0.3
    led_mouth: float = 0.0       # 45 degree chamfer at the LED pocket's mouth on the bed face (first-layer ring)
    led_rect: tuple = None       # (length x, width z): a rectangular LED spot instead of the led_d circle
    led_side_wall: float = 0.0   # > 0: the pocket also keeps this much horizontally from vertical outer faces (P10e: the
                                 # spot straddles the 1 mm facet step 4.0 from the USB edge; a 0.3 skin there printed as slits)
    # face_pockets: kept as code, off by default. Measured 2026-09-29 (face sliced alone, 14C): the pockets do not save
    # weight against 15% infill (9.19 g solid -> 9.07 g at a 1.2 skin, 9.53 g at 1.6; with thinner shells they weigh
    # more than without) and add ~20 min: the ribs, the pocket walls and a bottom skin on every ceiling replace sparse
    # infill. The shell settings (build_bambu.SHELL_G1: 6.36 g) are the lever.
    face_pockets: float = None   # 10.3a lightening (owner's H sketch): pockets in the back, the crown kept this thick over
                                 # them (vertical); None = solid. Terraced ceilings every pocket_step, ribs along the creases
    pocket_step: float = 0.4
    pocket_rim: float = 4.0      # solid band round the back: the tray wall top + the frame lip (3.6) + 0.4
    usb_end_w: float = 0.0       # 10.3b: the lip ring this wide (inward) for 7 mm each side of the USB notch (P10f)
    frame_tie: bool = False      # 10.3b: gussets at the USB-end pillars + a breakaway tie across the USB notch (P10e)
    part_suffix: str = ''        # after the part number on a variant (13.2A)
    top_label: str = None        # raised label on the shelf top, '|' splits lines (#11: ВЕРХ|МОТОР)
    seat_center: bool = False    # v1.1 seat: centre the module on the case's width axis (#11)
    seat_l: float = None         # v1.1 seat: PCB length between the posts along z (None = the datasheet 24; #11: 20)
    seat_drop: float = 0.0       # v1.1 seat: lower the PCB this much (#11: to the pins + 0.3)
    post_keepout: float = 0.0    # v1.1 seat: posts this far off the tray (#11: 0.3)
    proto: int = None            # prototype number (fit / test builds only): debossed on the tray floor and the shelf underside
    fence: float = 1.0           # locating fence outside the motor PCB
    fence_h: float = 1.2
    switch_slot_clr: float = 0.4    # slot clearance along the travel (x)
    switch_slot_off: float = 1.25   # v1.2: the slot runs this much further past the OFF end, so a nail catches the lever
    switch_wall_clr: float = None   # board edge to the switch-side inner wall (None = v1.1: the lever tip clr inside);
                                    # 0.3 needs tighter USB-end corners (outer_box: 0.85 short), pending the owner
    switch_scoop: float = 0.8       # v1.2: nail scoop around the slot in the outer face, this deep (45 degree sides)
    switch_slot_clr_y: float = 0.7  # slot clearance up and down (the lever height is read from photos, see SWITCH_DY)
    usb_chamfer: float = 0.25   # 45 degree lead-in at the outer face; small so the tray keeps 0.8 mm over the window
    usb_r: float = 1.6          # opening corner radius (the receptacle ends are round, r 1.6)
    # Grove cable (kit: 20 cm), coiled in the free space over the A0/D0 shroud row
    cable_len: float = 200.0
    cable_w: float = 4.4         # 4 x 26 AWG side by side
    cable_t: float = 1.1
    # OLED window (case v2; v1 has none): 'none', 'open' (a cut-out over the glass), 'lip' (the cut-out plus a recess
    # from inside for a glued clear sheet). The glass sits 12 mm under the front, so the cut-out is the floor of a
    # well that hangs from the front down to window_gap above the glass: no parallax, no view into the case.
    window: str = 'none'
    window_inset: float = 0.2    # aperture = OLED glass minus this per side (the glass border is black)
    window_r: float = 0.8        # aperture corner radius
    window_gap: float = 0.5      # bezel underside to the glass top
    window_bezel: float = 1.2    # well floor (bezel) thickness
    window_chamfer: float = 0.3  # 45 degree chamfer on the aperture's top edge
    window_ledge: float = 0.4    # flat floor ring between the aperture and the well walls
    window_wall: float = 1.0     # well wall thickness (horizontal)
    window_deg: tuple = (0.0, 12.0, 15.0, 15.0)   # wall draft from vertical: -x (USB end), +x (loop end), -z, +z
    window_kink_y: float = 7.6   # the -x wall stays vertical up to here (0.3 mm past the XIAO), then opens
    window_kink_deg: float = 30.0
    window_top_chamfer: float = 0.8   # 45 degree chamfer where the well meets the front
    window_field: float = 1.5    # faceted fronts: flat field this far around the well (the facets stop there); 0 = none
    window_field_h: float = 0.6  # field height over the rim
    window_lip: tuple = (1.0, 0.6)    # 'lip': recess width per side and depth, from inside (a 0.5 mm sheet sits flush)
    # test prints: a label raised on the floor's inner face under the board (not visible from outside); '' = none
    label: str = ''
    label_at: tuple = (131.0, 0.0)   # x, z of the label centre (clear of the parts under the board)
    label_size: float = 5.0
    label_h: float = 0.3


VARIANTS = dict(a=dict(corner='circle'), b=dict(corner='g2'), c=dict(corner='stadium'))

# Case versions. v1: the locked case (no OLED window). v2 (owner, 2026-09-28): the same board stack with a window over
# the OLED and a thinner shell; v2flat: v2 without the facet relief (flat front, the thinnest). version_p() builds P.
# Front fillet 2.5 (v1 3.0): with less than about 1.7 mm between the fillet radius and the front plate, Bambu Studio
# spreads the cover's supports 4.5 mm past its ends (measured: fillet 2.0 or plate 1.0 with 2.5), instead of 0.7.
V2 = dict(wall=1.6, floor=1.2, cover=0.8, fillet_front=2.5, latch_e=0.7, window='lip', rim_band=0.0, floor_chamfer=0.0)
# v1.1 has the same 1.6 / 1.2 walls since the owner's pick (2026-09-28); v2 keeps its thinner front plate and fillet, and
# needs neither the top band nor the floor-corner fill (0.99 / 1.0 mm measured)
# v1.0: the walls of the trays printed before v1.1 (2.0 / 1.4, no band or corner fill). The bay, ledges and loop end
# are those of the printed v1 trays (shelf_variants.py builds shelves for them); the USB-C end is v1.1's.
VERSIONS = dict(v1={}, v2=V2, v2flat=dict(V2, facet_angle=0.0, facet_min=0.0, window_field=0.0),
                **{'v1.0': dict(wall=2.0, floor=1.4, rim_band=0.0, floor_chamfer=0.0, end_wall=0.0, low_floor=False,
                                 grove_zone=3.5, switch_slot_off=0.0, switch_wall_clr=None, switch_scoop=0.0),
                   # #11 throne test: the #7 (v1.1) shelf with the seat hugging the 20 x 20 PCB, 1.2 lower, posts 0.3 off the tray
                   'v1.1-throne': dict(bay_hold=False, seat_l=20.0, seat_center=True, seat_drop=1.2, post_keepout=0.3, top_label='ВЕРХ|МОТОР',
                                       switch_slot_off=0.0, switch_scoop=0.0),
                   # #13 fence variants: the #11 shelf printed top down (fence up, no support), so without the seat
                   # posts; the label cut into the top, the number 0.5 deep underneath
                   'v1.1-fence': dict(bay_hold=False, seat_l=20.0, seat_center=True, seat_drop=1.2, post_keepout=0.3,
                                      top_label='ВЕРХ|МОТОР', switch_slot_off=0.0, switch_scoop=0.0, seat_posts=False,
                                      top_label_deboss=0.5, under_depth=0.5, top_chamfer=0.3),
                   # #10 (owner's width option 3 + the independent audit, 2026-09-28): 47.8 x 89.5, the board 0.3 off
                   # the switch wall and located by its edge, a rigid bay (the longest cell + 0.3), the shelf 1.2 with
                   # the #11 motor seat, partition teeth and a key; the faceted cover in two halves (10.3a face plate,
                   # 10.3b frame) joined by two dowels on the parting line, both printed without support
                   'v1.2': dict(grove_zone=2.0, switch_wall_clr=0.3, g2_req_bottom=3.55, len_extra=0.481,
                                shelf=0.8, shelf_clr=0.2, shelf_edge_clr=0.2, motor_drop=1.2, motor_pins=1.6, bay_len=31.9,
                                bay_leaf=False, bay_detent=False, motor_retain=True, far_lip=False, loop_boss_flat=True,
                                shelf_key=(3.0, 1.5), nail_dip=1.2, ledge_45=True, loop_gusset=True,
                                floor_arrow='провода →', board_locate=True, led_land=0.0, pillar_roofs=True,
                                top_label='ВЕРХ|МОТОР', floor_top=-5.75, motor_posts=True, post_keepout=0.3,
                                seat_split=True, under_fence=('full', 2.0, 0.0), fence_lead_b=0.8, ledge_cell_trim=True,
                                top_label_deboss=0.5, under_depth=0.5, top_chamfer=0.3,
                                xiao_pocket=0.0,
                                cover_split=True, peg_clr=0.1, ear_out=1.2, crease_r=1.5, led_normal=True, led_body=False,
                                lip_w=1.6, frame_tie=True, usb_face_clean=True, face_back_chamfer=0.5, led_mouth=0.3,
                                led_side_wall=0.9, usb_end_w=2.4, motor_rot180=True, hold_boss=0.2, hold_boss_w=19.0, hold_boss_keep=((-5.6, 5.6),), hold_legs=True,
                                tab_t=1.6, tab_square=True, tab_ties=2, tab_end_ties=True, tab_tie_w=0.6)})
# v1.3 (owner, 2026-09-29): the Grove plug's wires were crushed flat against the +z wall (1.2 from the plug back to the
# wall, the wire is 1.3): +1.8 on +z only (47.8 -> 49.6) plus a 0.8 pocket behind A0/D0 give its wires an R 2.5 bend
# (UART R 1.7: the D1 tongue sits behind it, no pocket there). The D1 nub grows by itself (0.74 -> 2.54).
# len_extra: the wider corners need less loop-end growth; keep the owner's 89.5 (x1 207.258)
# the face: #16A (owner, 2026-09-29): facets with crease_r 20, printed with the G1 shell
# PENDING v1.3.1 tray (owner, 2026-09-29, from the printed 17.1): the A0 pocket shows through (0.8 wall) and breaks the
# rim top as a ragged slit. Next tray: pocket 0.4 deep (1.2 wall, 3 lines), its top at y 4.5 under a 45 degree roof
# (the wire's bend ends at y 0.95 + R 2.1 + 1.3 = 4.35), solid wall and a continuous rim above; A0 bend R 2.1.
# the loop (owner, 2026-09-29, 'gigantic'): back to the #7 lug exactly, no fins under it (loop_gusset off; the inner
# boss stays the #7 flat one), and the grid support #7 had painted under it; the tray number on the outside bottom
VERSIONS['v1.3'] = dict(VERSIONS['v1.2'], grove_zone=3.8, port_pocket=0.8, len_extra=0.481 + 0.47084,
                        crease_r=20.0, face_shell='G1',
                        loop_gusset=False, loop_support=True, mark_outside=True,
                        # 17.2 = the 10.2C shelf (owner: the construction is perfect, only its rib lattice failed): one
                        # piece, 13.2B fence + 11.2 posts, top up, the plate on the slicer's grid support (shelf_support);
                        # frame legs out to |z - 2.5| >= 15 (room for a 29.2-wide DA7280)
                        seat_split=False, shelf_ribs=False, shelf_support=True,
                        # the tray key stays (owner, 2026-09-29): the printed 17.1 carries it; 17.2b has its notch
                        hold_legs_z=((-16.5, -12.5), (17.5, 21.5)))
# #18 cover (v1.3-p18, owner, 2026-09-29): fits the printed 17.1 tray + 17.2b shelf; the tray, the loop and the shelf
# are v1.3's. Differences from #17 (17.3a/b), each asked for by the owner:
#  - face retention: 17.3a sat on 2 dowels only and its ends lifted. 4 more dowels where the face is >= 3.3 thick over the
#    lead-in disk (2.5 hole + 0.8 skin). The crossbar legs (z -14.5 / 19.5) have 2.05 there, so the loop-end pair moves
#    inward: +z on the hold-down bar over the +z foot, -z beside the bar on a web (off the coin and J1). The USB end has
#    >= 3.3 only over the XIAO (no room under the line), so its pair sits on a new crossbar just past the XIAO (x 144; +z stops short of the A0 cable zone).
#  - the hold-down feet (17.3b fit, owner photos 24fd6e5b / 59bf98e6): the coin sits under the -z foot (the A0 shroud is on
#    the photo's left = +z; the owner cut the foot he calls left, seen from the USB end = -z). The coin is modelled at
#    (dx 1.0, dz -4.5) off the module centre (edge 0.5 in from the -z PCB edge); the -z foot stops 1.0 over its top
#    (PCB top + 3.4 + 1.0), the +z foot keeps +0.2 on bare PCB. The module sits 0.69 toward -z (17.2b = the 11.2 posts).
#  - the face shell T08 (owner: the G1 gyroid showed through the 0.48 top): 10 x 0.08 top over 15% gyroid; crown unchanged.
VERSIONS['v1.3-p18'] = dict(VERSIONS['v1.3'], face_shell='T08', motor_dz=-0.69, coin_at=(1.0, -4.5),
                            hold_boss_gaps=(3.4 + 1.0, 0.2),
                            extra_dowels=((191.9, 7.25, None), (183.5, -7.25, 189.44), (144.0, -8.0, None), (144.0, 10.3, None)),
                            usb_bar_x=144.0)
# #19 (owner, 2026-09-29, fallback c): the #18 cover as one part, no dowels: the 4 M2 screws clamp face and frame
# together. The lip stays on the cover (the tray cannot take it: the face is 1.0 thick over the lip ring), so 19.3 fits
# the printed 17.1 unchanged. Crown up on the pillar tips over painted slicer grid support (the 17.2 settings the owner
# found easy to remove), blocked at the pillars / nut slots and the LED. Designed fins (cover_fins 4 + the lip ring)
# weighed 12.9 g of fins alone.
# #20 (owner, 2026-09-29): the #18 face and frame (2 centre dowels, no USB crossbar) with the nuts in square bosses
# under the face's back at the 4 screws (M2 x 16 unchanged), so the screws clamp the face. Fits the printed 17.1.
VERSIONS['v1.3-p20'] = dict(VERSIONS['v1.3-p18'], extra_dowels=(), usb_bar_x=None, face_bosses=True)
# #18.1 (owner, 2026-09-29): #18 closed the USB end perfectly, but its 6 dowels had to be hammered in, the loop-end -z
# dowel boss (on a 1.2 web) broke, and the face label read mirrored from the back. Face holes 0.125 per side (Ø3.25,
# thumb press), frame holes stay 0.10 (the dowel stays in the frame), 0.5 lead-ins, that boss on a solid block to the
# bar, the label read from the back. Everything else is #18.
# Owner additions: the frame lattice filled to a thin plate (0.8, as the webs) from past the XIAO to the loop end, with
# a window over the motor's J1 (its plug and cable); and 10 dowels in a pattern mirrored across both axes about
# (162, the case axis): USB x 144.5 and loop x 179.5 at z axis +- 7.8 and on the axis, the centre pair 152 / 172, and
# x 162 at +- 7.8. The face is >= 3.3 over every lead-in (3.69 .. 4.72); +- 7.8 stops the +z row clear of the A0 cable
# zone, x 144.5 clears the XIAO, x 179.5 clears J1. The #18 bar / web dowels and the USB crossbar go.
_zc = 2.505
VERSIONS['v1.3-p18.1'] = dict(VERSIONS['v1.3-p18'], peg_clr_face=0.125, peg_lead=0.5, proto_label='18.1-3', usb_bar_x=None,
                              extra_dowels=tuple((x_, _zc + dz_, None) for x_ in (144.5, 179.5) for dz_ in (-7.8, 0.0, 7.8))
                              + ((162.0, _zc - 7.8, None), (162.0, _zc + 7.8, None)),
                              frame_plate=141.0, frame_windows=((181.9, 189.0, 1.81 - 6.0, 1.81 + 6.0),), face_label_x=139.0)
# #18.1b (owner, 2026-09-29: "the edge will peel off"; his own layout on the 18.1 pattern): the 4 dowels on the axis go;
# the 6 at x 144.5 / 162 / 179.5, z axis +- 7.8 stay; 4 corner dowels mirrored about the axis, nudged 1.25 inward from
# his (192.5 / 132.5, 18.4 / -12.4) to where the face is 2.31: the short type (1.5-deep face holes, 0.8 skin, 0.3
# lead-ins, 4 mm dowels). The frame plate now spans the USB end too, open only over the XIAO's parts and the plug.
VERSIONS['v1.3-p18.1b'] = dict(VERSIONS['v1.3-p18.1'], proto_label='18.1b-3', centre_dowels=False,
                               extra_dowels=tuple((x_, _zc + dz_, None) for x_ in (144.5, 162.0, 179.5) for dz_ in (-7.8, 7.8)),
                               short_dowels=((191.75, 17.4, None, None), (191.75, 2 * _zc - 17.4, None, None),
                                             (133.25, 17.4, None, None), (133.25, 2 * _zc - 17.4, None, None)),
                               frame_plate=116.0, frame_windows=((117.0, 137.6, -6.0, 8.0), (181.9, 189.0, 1.81 - 6.0, 1.81 + 6.0)))
# #18.1c (owner, 2026-09-30): the loop end of #18.1b stood 1-1.5 proud: the Grove header on the motor module is a
# vertical 8.6 part (the model had 5.1), its plug went through the plate slot into a flat face back. Changes, each asked
# for: a terraced pocket over the plug (0.6 skin, the plate slot's footprint + 0.3), the +z hold-down foot to touch the
# PCB (it stood 0.2 off), 2 dowel locators (round Ø3.25 at 144.6, slot 3.25 x 3.85 along x at 179.4, z 10.3); the other
# 8 face holes Ø3.45 with 3 crush ribs to Ø3.225 (0.6 wide: a 0.3 rib is under the 0.42 line and would not print), the
# x 179.5 / 144.5 dowels 0.1 toward the middle (0.5 off the taller header).
VERSIONS['v1.3-p18.1c'] = dict(VERSIONS['v1.3-p18.1b'], proto_label='18.1c-3',
                               motor_conn_xz=(0.5 - 1.3, 5.5 + 1.3, -5.0 - 1.3, 5.0 + 1.3), face_pocket_skin=0.6,
                               hold_boss_gaps=(3.4 + 1.0, 0.0),
                               extra_dowels=tuple((x_, _zc + dz_, None) for x_ in (144.6, 162.0, 179.4) for dz_ in (-7.8, 7.8)),
                               dowel_locators=((144.6, _zc + 7.8), (179.4, _zc + 7.8)), peg_ribs=(3.45, 3.225, 0.6, 3),
                               dowel_sprue=True)
# owner, same day: one dowel type (the 4 mm ones were too small to hold, fell out, barely seated): the corner dowels are
# the normal 5 mm dowel, 1.5 in the thin face and 3.5 in a deeper frame post (4.1 under the line). The USB corners move
# 3.55 toward the middle (x 136.8): a 4.1-deep post at 133.25 sat over the screw pillars' nut-insertion slots. The
# middle dowels moved outward only where free (face >= 3.69, clear of the A0 cable zone): (162, -5.3) -> (162, -10.2).
VERSIONS['v1.3-p18.1c']['short_len'] = 2 * P.peg_depth
VERSIONS['v1.3-p18.1c']['short_dowels'] = ((191.75, 17.4, None, None), (191.75, 2 * _zc - 17.4, None, None),
                                          (136.8, 17.4, None, None), (136.8, 2 * _zc - 17.4, None, None))
VERSIONS['v1.3-p18.1c']['extra_dowels'] = ((144.6, _zc - 7.8, None), (144.6, _zc + 7.8, None), (162.0, _zc - 12.7, None),
                                          (162.0, _zc + 7.8, None), (179.4, _zc - 7.8, None), (179.4, _zc + 7.8, None))
# #18.1d (owner, 2026-09-30, after assembling #18.1c: the dowels at both ends sank, the face came off there; the pusher
# and the ribs stay): every frame hole is blind and sets the protrusion (P = 5.0 - frame depth), the face hole is P + 0.04,
# all depths on the 0.2 + 0.16 k layer grid. Real face grip (P - 0.3 dowel chamfer - 0.2 rib start), 18.1c -> 18.1d:
# middle 1.7 -> 2.06 (face 2.6, frame 2.44), corners 0.9 -> 1.26 (face 1.8, frame 3.24): the face is 2.3-2.5 there and
# 2.0 would need 3.2, found only 6-7 mm inward. The loop corners 1.0 inward (their skin 0.66 over a 1.8 hole); the USB
# corner posts end at y 8.43, over the pillar nuts' path (8.35). A two-ended pusher: cup 2.56 (middle) / 1.76 (corners).
VERSIONS['v1.3-p18.1d'] = dict(VERSIONS['v1.3-p18.1c'], proto_label='18.1d-3',
                               peg_face_d=2.6, peg_frame_d=2.44, short_face_depth=1.8, short_frame_d=3.24,
                               short_dowels=((191.27, 16.52, None, None), (191.27, 2 * _zc - 16.52, None, None),
                                             (136.8, 17.4, None, None), (136.8, 2 * _zc - 17.4, None, None)),
                               short_post_d=(4.1, 4.1, 3.72, 3.72), rib_lead=0.2, frame_lead=0.2,
                               pusher_cups=(2.56, 1.76))
# #18.1e candidate (not sliced; 18.1d went to print as is, with its pusher): no pusher on the plate (the owner keeps the
# 18.1c one, cup 1.5: shallower than every protrusion, so the hole floor is the stop everywhere). The USB corner floors
# 0.47 -> 0.63 (their posts cannot go lower: the pillar nuts' path is at 8.35): frame 3.08, face 1.96 (skin 0.57),
# protrusion 1.92, grip 1.26 -> 1.42 there.
# #18.1e (owner, 2026-09-30, option 3 for the DA7280's Qwiic cable): + the +z hold-down legs 2.8 out (17.5-21.5 ->
# 20.3-24.3) so shelf 17.3b can shift the board 2.9 toward +z: its J1 cable then runs clear of the expansion board's
# 2 x 4 pin column (wires >= 1.0 off in z)
VERSIONS['v1.3-p18.1e'] = dict(VERSIONS['v1.3-p18.1d'], proto_label='18.1e-3', sprue_pusher=False,
                               short_frame_d=(3.24, 3.24, 3.08, 3.08), short_face_ds=(1.8, 1.8, 1.96, 1.96),
                               hold_legs_z=((-16.5, -12.5), (20.3, 24.3)))
# 18.1d failed (owner, 2026-09-30: the dowels fall out of the face; some punched through their frame floors). From the
# sliced G-code (fit_gate.py), 18.1c and 18.1d have the SAME face holes (rib crest Ø3.227, bore Ø3.478 at every layer),
# the same frame holes (Ø3.20, stops 0.48 / 0.80) and the same dowels (Ø2.995 with a 0.3 D-flat): (1) the face grip
# never had a designed interference (crest 0.23 over the dowel), only the print's shrink; (2) the D-flat, turned onto one
# of the 3 ribs (~60% of orientations), takes that rib out: 0.41 of radial play, a lottery per dowel; (3) a bridged
# floor under 1 mm is no stop, and 18.1d's protrusions (2.56 / 1.76) were driven with the 18.1c pusher (cup 1.5) until
# its rim landed: 0.26-1.06 past the floors. 18.1e:
#  - round dowels (dowel_flat 0; the face holes vent between their ribs, the frame holes through their necks);
#  - rib crests Ø3.125 (+0.10 over 18.1c) until the fit coupon (3.225 / 3.175 / 3.125) picks the step;
#  - every frame hole ends in a Ø1.6 through neck; the ring the dowel lands on is 1.2 thick (1.28 on the layer grid) at
#    the 6 middle, the 2 loop-corner and the loop-centre posts (3.64 / 4.44 / 3.64 deep); a stop you feel, any pusher;
#  - the 2 USB corners keep 0.48 rings (their posts end over the pillar nuts' path, 8.35): owner to decide (the USB end
#    is clamped by its screws);
#  - a loop-end centre dowel on the axis at x 192.0 (owner's mark: in line with the corners, 1.03 of wall to the
#    connector pocket): face 2.6 (face 3.38 there, skin 0.78), frame 2.44 (2.56 proud, the middle type), post 3.64 to
#    y 8.51: 0.81 over the DA7280's LRA (17.3b), 2.9 to its J2. It overlaps the 17.2b Grove module's coin: 18.1e is for
#    the DA7280 only (lead, 2026-09-30). v1.3-p18.1e-g: the same with that post at 2.78 (0.42 over the coin, a 0.34
#    ring) for a closure test with the old motor only.
VERSIONS['v1.3-p18.1e'].update(
    peg_ribs=(3.45, 3.125, 0.6, 3), frame_neck=1.6, mid_post_d=3.64, dowel_flat=0.0,
    short_dowels=VERSIONS['v1.3-p18.1d']['short_dowels'] + ((192.0, _zc, None, None),),
    short_frame_d=(3.24, 3.24, 3.24, 3.24, 2.44), short_face_ds=(1.8, 1.8, 1.8, 1.8, 2.6),
    short_post_d=(4.44, 4.44, 3.72, 3.72, 3.64))
# v1.3-p18.1e-g: that 18.1e with the centre post at 2.78 (0.42 over the Grove coin, a 0.34 ring), for a closure test
# with the old Grove motor on 17.2b only (lead, 2026-09-30; not sliced until asked)
VERSIONS['v1.3-p18.1e-g'] = dict(VERSIONS['v1.3-p18.1e'], proto_label='18.1eg-3', short_post_d=(4.44, 4.44, 3.72, 3.72, 2.78))
# 18.1e for the DA7280 on shelf 17.3c (2026-09-30, after 17.3b sat on the battery socket): the board is raised 2.65
# (underside 4.70, top 6.30, LRA top 10.35, J1 / J2 tops 9.25), so the frame gives up the Grove hold-down (bar, boss,
# legs: the board is pinned, nothing presses it, nothing pushes the cover up) and the face its Grove connector pocket;
# the slot locator post moves (179.4, 10.3) -> (179.4, 14.1) off the raised J1 and its Qwiic plug; the loop-centre dowel
# moves (192.0, 2.5) -> (192.0, 5.45), off the LRA's footprint (0.8 in plan), its post 3.64 (a 1.2 ring); the loop
# corner posts r 3.0 -> 2.6 (0.8 in plan to the LRA). The board moves 0.2 toward the loop end (0.31 to the +z pillar).
VERSIONS['v1.3-p18.1e'].update(
    hold_down=False, hold_legs=False, motor_conn_xz=None, motor_kind='da7280',
    extra_dowels=tuple((x_, z_, None) for x_, z_ in ((144.6, _zc - 7.8), (144.6, _zc + 7.8), (162.0, _zc - 12.7),
                                                      (162.0, _zc + 7.8), (179.4, _zc - 7.8), (179.4, 14.1))),
    dowel_locators=((144.6, _zc + 7.8), (179.4, 14.1)),
    short_post_r=(2.6, 2.6, 3.0, 3.0, 3.0),     # the loop corners' posts r 2.6 (wall 1.0): 0.8 in plan to the raised LRA
    short_dowels=VERSIONS['v1.3-p18.1d']['short_dowels'] + ((192.0, 5.45, None, None),))
# 18.1e synced to 18.2-G's joint (owner, 2026-09-30: both versions share the strengthened face-dowel joint): round
# dowels, crest 3.075, middle / locator / centre frame 2.28 + face 2.76 (2.72 proud, grip 2.22), rings >= 1.28 round a
# through Ø1.6 neck; the loop corners to where the face is >= 3.2 and off the raised LRA: (191.27, 11.5) and
# (181.5, -10.0), frame 2.44 / face 2.6 (2.56 proud, grip 2.06); no USB corners (the screws clamp that end); the same
# sprue (+1 test, +3 spare) and ТЕСТ joint.
VERSIONS['v1.3-p18.1e'].update(
    peg_ribs=(3.45, 3.075, 0.6, 3), peg_face_d=2.76, peg_frame_d=2.28,
    short_dowels=((191.27, 11.5, None, None), (181.5, -10.0, None, None), (192.0, 5.45, None, None)),
    short_frame_d=(2.44, 2.44, 2.28), short_face_ds=(2.6, 2.6, 2.76), short_post_d=(3.72, 3.72, 3.64),
    short_post_r=(3.0, 3.0, 3.0), test_joint=True, sprue_spares=3)


# 18.2-G (owner, 2026-09-30: two versions; this is the production one for the current Grove motor on shelf 17.2b, to
# print now): 18.1e-g's retention fixes (round dowels, crests from the coupon, necked frame holes with 1.2 rings at the
# 6 middle and 2 loop-corner posts) on 18.1d's Grove frame (hold-down bar, boss and legs as 18.1d: legs at 18.1d's z,
# the Grove connector pocket in the face). The loop-centre dowel at (192.5, 5.6): off the coin (8.3 between centres,
# 0.3 in plan) and off the connector's pocket zone (x <= 189.2), so its post goes to 3.64 (a 1.2 ring) like the middle
# ones.
VERSIONS['v1.3-p18.2-G'] = dict(VERSIONS['v1.3-p18.1e-g'], proto_label='18.2G-3', hold_legs_z=None,
                                short_dowels=VERSIONS['v1.3-p18.1d']['short_dowels'][:2] + ((192.5, 5.6, None, None),),
                                short_frame_d=(3.24, 3.24, 2.44), short_face_ds=(1.8, 1.8, 2.6),
                                short_post_d=(4.44, 4.44, 3.64))
# owner, 2026-09-30 (coupon: the Ø3.125 crest, 3 dimples, holds perfectly; 3.175 comes off, 3.225 falls out): crest
# 3.125 as sliced; the 2 USB-corner dowels dropped (the screws clamp that end; their posts could not reach a 1.2 stop).
# owner, 2026-09-30 (coupon assembled: face hole 3 on the dowel standing 1.76 out of frame hole 3 holds poorly; a loose
# dowel fully in face hole 3 felt perfect; the 3.24 + neck + 1.28 ring stop sits firmly): the grip was too short. 18.2-G:
#  - every protrusion >= 2.4 into the face: middle 6 + locators + centre frame 2.28 / face 2.76 (2.72 proud, real grip
#    2.72 - 0.3 chamfer - 0.2 rib start = 2.22; skins >= 0.76); the loop corners move to where the face is >= 3.2:
#    (191.27, 11.5) and (186.5, -9.0) (the -z one clear of the coin), frame 2.44 / face 2.6 (2.56 proud, grip 2.06);
#  - crest 3.075 (one step past the coupon's 3.125), the 0.2 rib lead-in kept;
#  - every frame hole ends on a >= 1.28 ring round a through Ø1.6 neck (the stop the owner felt firm).
VERSIONS['v1.3-p18.2-G'].update(
    peg_ribs=(3.45, 3.075, 0.6, 3), peg_face_d=2.76, peg_frame_d=2.28,
    short_dowels=((191.27, 11.5, None, None), (186.5, -9.0, None, None), (192.5, 5.6, None, None)),
    short_frame_d=(2.44, 2.44, 2.28), short_face_ds=(2.6, 2.6, 2.76), short_post_d=(3.72, 3.72, 3.64), test_joint=True,
    sprue_spares=3)   # owner: 9 round dowels + 1 for the ТЕСТ joint + 3 spares; no pusher (he has one)
# 18.2-B (owner, 2026-10-02, after 18.1e-B failed its first assembly): edition B is 18.2-G exactly (face with the Grove
# pocket, frame, dowels, joint) minus the two points the owner found pressing the DA7280 board on shelf 17.3c, both on
# the +z side: the +z hold-down leg (z 14.8-18.8) and the +z hold-down boss piece (z 7.4-11.3, beside the (192.5, 5.6)
# post). The -z leg and the -z boss piece stay (owner: they press nothing).
VERSIONS['v1.3-p18.2-B'] = dict(VERSIONS['v1.3-p18.2-G'], proto_label=None,   # owner 2026-10-03: no part codes inside the models
                               
                                hold_legs_z=((-15.185, -11.185),), hold_boss_keep=((-5.6, 5.6), (5.6, 30.0)))
# 18.2-B first print (owner, 2026-10-03): the cover did not close; with the locator post (179.4, 10.305) cut 2 mm
# shorter it closed and the dowel still held (the model had that post 0.74 into the DA7280's J1 / Qwiic plug). And
# three labelled 10-dowel sprues, S 3.00 / M 3.05 / L 3.10, in place of the one sprue: a loose dowel takes the next size.
VERSIONS['v1.3-p18.2-B'].update(post_trims=((179.4, 10.305, 2.0), (179.4, -5.295, 1.0)),   # owner: the other post of that row 1 mm too
                                sml_sprues=(('S', 3.00), ('M', 3.05), ('L', 3.10)), test_joint=False)   # owner: no ТЕСТ joint any more
# #22 (owner, 2026-09-30): #18.1c with the face held to the frame by 8 hidden DIN 7981 C ST2.2 x 4.5 screws from under
# the frame plate, no dowels. The USB-end quadrant takes none: the pillar nut slots' insertion paths, the XIAO and the
# A0 cable zone leave no room for a boss there. Locators: the snug frame holes at (144.5, 9.7) and (187.3, -12).
VERSIONS['v1.3-p22'] = dict(VERSIONS['v1.3-p18.1c'], proto_label='22-3', extra_dowels=(), short_dowels=(), dowel_sprue=False,
                            dowel_locators=(), peg_ribs=None,
                            face_screws=((143.5, -12.0), (154.0, -13.0), (180.0, -12.0), (187.3, -12.0),
                                         (144.5, 9.7), (162.0, 9.7), (181.5, 17.0), (191.0, 14.0)),
                            face_screw_locators=((144.5, 9.7), (187.3, -12.0)))
VERSIONS['v1.3-p19'] = dict(VERSIONS['v1.3-p18'], extra_dowels=(), usb_bar_x=None, cover_onepiece=True)


def version_p(name='v1', **kw):
    if name not in VERSIONS:
        raise SystemExit(f'unknown case version {name!r}; known: {", ".join(VERSIONS)}')
    return P(**{**VERSIONS[name], **kw})


# ---------------------------------------------------------------- packing
def packing(p: P):
    """Cavity box (x0, x1, y0, y1, z0, z1) and where the cell and the motor go."""
    M, D = MEASURED, DATASHEET
    c = p.clr
    # USB-C end: the end wall's outer face usb_recess in front of the receptacle mouth, unless that leaves less than clr
    # between the (end_wall thick) flat end wall and the board edge; x0 is the box face one full wall inside
    ew = end_wall(p)
    x0 = min(M['usb_c']['x_mouth'] - p.usb_recess, M['board_x'][0] - c - 0.05 - ew) + p.wall
    # switch side: v1.1 kept the lever tip clr inside the wall (the lever sat 1.9 under the outer face, out of a nail's
    # reach); v1.2 puts the wall switch_wall_clr off the board edge, so the lever runs into the slot in the wall
    z0 = (M['switch']['z_min'] - c) if p.switch_wall_clr is None else (M['board_z'][0] - p.switch_wall_clr)
    z1 = M['grove_a0']['z_mouth'] + (D['grove_plug_len'] - D['grove_socket_depth']) + p.grove_zone
    x_jst = M['jst']['x_mouth'] + p.jst_zone
    ceil_board = M['xiao_top_y'] + XIAO_DY_UP + c + p.ceil_margin
    lw, ll, lt = D['lipo']
    mw, ml, mt = D['motor']
    ml = p.motor_l if p.bay_hold else ml
    under = M['under_min_y'] - c                           # floor top under the board, nothing extra
    if p.low_floor and p.layout == 'B':
        # v1.1: the floor rises under the board as far as it can without making the case deeper: the bay stack
        # (cell, swell, shelf, motor) then ends at the XIAO's ceiling, or the floor stops clr under the lowest part
        # other than the CR1220 holder, which gets its own pocket in the floor (holder_pocket)
        bay_stack = lt + p.lipo_swell + p.shelf + mt - (p.motor_drop if p.bay_hold else 0.0) + c
        under = min(M['under_rest_y'] - c, ceil_board - bay_stack)
        if p.floor_top is not None:     # #10: keep v1's floor (the CR1220 holder pocket needs it)
            under = p.floor_top
    parts = {}
    if p.layout == 'A':     # cell and motor side by side under the board
        motor_top = -4.74 - c
        cell_top = M['under_min_y'] - c - p.foam
        y0 = min(motor_top - mt, cell_top - lt)
        y1 = ceil_board
        x1 = x_jst
        parts['motor'] = (x0 + 0.4, x0 + 0.4 + ml, motor_top - mt, motor_top, z0 + 1.0, z0 + 1.0 + mw)
        parts['lipo'] = (143.0, 143.0 + ll, cell_top - lt, cell_top, -20.0, -20.0 + lw)
    elif p.layout == 'B':   # end bay past the JST: cell on the floor, shelf, motor on top
        y0 = under
        bay_top = y0 + lt + p.lipo_swell + p.shelf + mt - (p.motor_drop if p.bay_hold else 0.0) + c
        y1 = max(ceil_board, bay_top)
        bx0 = x_jst
        x1 = bx0 + lw + 2 * c
        lz0 = -ll / 2 if not p.bay_hold else (z0 + z1) / 2 - ll / 2     # v1.2: the bay centred on the case axis too
        parts['lipo'] = (bx0 + c, bx0 + c + lw, y0, y0 + lt, lz0, lz0 + ll)
        my0 = y0 + lt + p.lipo_swell + p.shelf - (p.motor_drop if p.bay_hold else 0.0)
        # socket toward +z for the Grove cable; 1.2 mm back so the module corner clears a corner arc
        mz1 = z1 - p.grove_zone - (D['grove_plug_len'] - D['grove_socket_depth']) - 1.2
        if p.bay_hold:          # v1.2 (owner): the module centred on the case's width axis
            mz1 = (z0 + z1) / 2 + ml / 2
        mdx = p.motor_dx if p.bay_hold else 0.0
        parts['motor'] = (bx0 + c + (lw - mw) / 2 + mdx, bx0 + c + (lw + mw) / 2 + mdx, my0, my0 + mt, mz1 - ml, mz1)
        parts['shelf'] = (bx0, x1, y0 + lt + p.lipo_swell, y0 + lt + p.lipo_swell + p.shelf, z0, z1)
    elif p.layout == 'C':   # cell and motor beside the board, along the +z long side
        y0 = under
        y1 = max(ceil_board, y0 + lt + p.lipo_swell + p.shelf + mt + c)
        x1 = x_jst
        cz0 = z1
        parts['lipo'] = (130.0, 130.0 + ll, y0, y0 + lt, cz0 + c, cz0 + c + lw)
        my0 = y0 + lt + p.lipo_swell + p.shelf
        parts['motor'] = (130.0 + (ll - ml) / 2, 130.0 + (ll + ml) / 2, my0, my0 + mt, cz0 + c, cz0 + c + mw)
        z1 = cz0 + lw + 2 * c
    else:
        raise ValueError(p.layout)
    return dict(cavity=(x0, x1, y0, y1, z0, z1), parts=parts)


def end_wall(p: P):
    return p.end_wall if 0 < p.end_wall < p.wall else p.wall


def base_outer_box(p: P):
    x0, x1, y0, y1, z0, z1 = packing(p)['cavity']
    return (x0 - p.wall, x1 + p.wall, y0 - p.floor, y1 + p.cover, z0 - p.wall, z1 + p.wall)


# ---------------------------------------------------------------- silhouette
def corner_extent(p: P, width, end='top'):
    """Distance from a box corner to where the corner curve meets the straight side. end 'bottom' = the USB-C end
    (x min), whose corners are g2_req_bottom (v1.1: the end wall is flat at the receptacle), 'top' = the loop end."""
    if p.corner == 'circle':
        return p.corner_r
    if p.corner == 'g2':
        # same diagonal cut as a circle of g2_req: circle cut = r(sqrt2 - 1);
        # superellipse cut = sqrt2 * c * (1 - 2^(-1/n))
        req = p.g2_req_bottom if end == 'bottom' and p.g2_req_bottom > 0 else p.g2_req
        return req * (math.sqrt(2) - 1) / (math.sqrt(2) * (1 - 2 ** (-1 / p.g2_n)))
    if p.corner == 'stadium':
        return width / 2 - p.stadium_flat / 2
    raise ValueError(p.corner)


def _corner_pts(p: P, cx, cz, sx, sz, c, n=24):
    """Points of one corner from the end-side tangent point to the long-side tangent point.
    (cx, cz) box corner, (sx, sz) inward signs."""
    ox, oz = cx + sx * c, cz + sz * c          # curve centre
    e = 2.0 if p.corner in ('circle', 'stadium') else p.g2_n
    pts = []
    for i in range(n + 1):
        t = (math.pi / 2) * i / n
        pts.append((ox - sx * c * math.cos(t) ** (2 / e), oz - sz * c * math.sin(t) ** (2 / e)))
    return pts


def outline_pts(p: P, box, n=24):
    """Closed outline in (x, z), counter-clockwise seen from +y... order: bottom end, +z side, top end, -z side."""
    X0, X1, _, _, Z0, Z1 = box
    c = corner_extent(p, Z1 - Z0)
    cb = corner_extent(p, Z1 - Z0, 'bottom')
    pts = []
    for (cx, cz, sx, sz, rev) in ((X0, Z1, 1, -1, False), (X1, Z1, -1, -1, True),
                                  (X1, Z0, -1, 1, False), (X0, Z0, 1, 1, True)):
        q = _corner_pts(p, cx, cz, sx, sz, cb if cx == X0 else c, n)
        pts += q[::-1] if rev else q
    return pts, c


def profile(p: P, box, y):
    """CadQuery closed profile of the outline on the plane y (normal +y)."""
    pl = cq.Plane(origin=(0, y, 0), xDir=(1, 0, 0), normal=(0, 1, 0))   # local (u, v) = (x, -z)
    X0, X1, _, _, Z0, Z1 = box
    c = corner_extent(p, Z1 - Z0)
    cb = corner_extent(p, Z1 - Z0, 'bottom')
    L = lambda q: (q[0], -q[1])
    wp = cq.Workplane(pl)
    corners = ((X0, Z1, 1, -1, False), (X1, Z1, -1, -1, True), (X1, Z0, -1, 1, False), (X0, Z0, 1, 1, True))
    first = True
    for (cx, cz, sx, sz, rev) in corners:
        q = _corner_pts(p, cx, cz, sx, sz, cb if cx == X0 else c, 16)
        q = q[::-1] if rev else q
        if first:
            wp = wp.moveTo(*L(q[0])); first = False
        else:
            wp = wp.lineTo(*L(q[0]))
        if p.corner in ('circle', 'stadium'):
            wp = wp.threePointArc(L(q[len(q) // 2]), L(q[-1]))
        else:
            # exact side directions at both joins, so the spline is tangent (and, n > 2, curvature-free) there
            t0, t1 = ((-sx, 0), (0, sz)) if rev else ((0, -sz), (sx, 0))
            wp = wp.spline([L(v) for v in q[1:]], tangents=[L(t0), L(t1)], includeCurrent=True)
    return wp.close()


# ---------------------------------------------------------------- growth
def footprints(p: P):
    """(points, clearance) sets in (x, z) that must stay inside the cavity (outer outline minus wall)."""
    M = MEASURED
    k = packing(p)
    x0, x1, _, _, z0, z1 = k['cavity']
    bx0, bx1 = M['board_x']; bz0, bz1 = M['board_z']; r = M['board_r']
    pcb = []
    for (cx, cz, a0) in ((bx1 - r, bz1 - r, 0), (bx0 + r, bz1 - r, 90), (bx0 + r, bz0 + r, 180), (bx1 - r, bz0 + r, 270)):
        for i in range(19):
            t = math.radians(a0 + 90 * i / 18)
            pcb.append((cx + r * math.cos(t), cz + r * math.sin(t)))

    def rect(xa, xb, za, zb, step=0.5):
        out = []
        for x in np.arange(xa, xb + 1e-9, step):
            out += [(x, za), (x, zb)]
        for z in np.arange(za, zb + 1e-9, step):
            out += [(xa, z), (xb, z)]
        return out
    # the USB-C receptacle is not a footprint: it passes through the end wall's opening (v1.1)
    sw = p.switch_wall_clr
    sets = [(pcb, p.clr if sw is None else min(p.clr, sw)),
            # v1.2: the lever runs into the slot in the wall, so only the switch body up to the board edge counts
            (rect(*M['switch']['x'], M['switch']['z_min'] if sw is None else bz0, -19.0), p.clr if sw is None else sw),
            (rect(*M['grove_a0']['x'], M['grove_a0']['z_mouth'], z1), 0.0),       # plug + cable bend zone
            (rect(M['jst']['x_mouth'], M['jst']['x_mouth'] + p.jst_zone, *M['jst']['z']), 0.0)]
    for name in ('lipo', 'motor'):
        if name in k['parts']:
            a = k['parts'][name]
            sets.append((rect(a[0], a[1], a[4], a[5]), p.clr))
    return sets


def _inside_margin(poly, pts):
    """Signed distance of each point to the closed convex polygon boundary (positive inside)."""
    P_ = np.array(poly); Q = np.array(pts)
    A = P_; B = np.roll(P_, -1, axis=0)
    AB = B - A
    AQ = Q[:, None, :] - A[None, :, :]
    t = np.clip((AQ * AB[None]).sum(-1) / (AB * AB).sum(-1)[None], 0, 1)
    d = np.linalg.norm(AQ - t[..., None] * AB[None], axis=-1).min(1)
    # inside test for a convex polygon: same side of every edge
    cr = AB[None, :, 0] * AQ[..., 1] - AB[None, :, 1] * AQ[..., 0]
    inside = (cr >= -1e-9).all(1) | (cr <= 1e-9).all(1)
    return np.where(inside, d, -d)


def fits(p: P, box):
    poly, _ = outline_pts(p, box, 90)
    worst = 1e9
    for pts, clr in footprints(p):
        m = _inside_margin(poly, pts) - p.wall - clr
        worst = min(worst, m.min())
    return worst


_GROW = {}


def outer_box(p: P):
    """Base box, grown along x (length) until every footprint clears the chosen silhouette.
    Thickness never changes; width does not grow (the owner prefers long and narrow)."""
    key = json.dumps(asdict(p), sort_keys=True, default=str)
    if key in _GROW:
        return _GROW[key]
    X0, X1, Y0, Y1, Z0, Z1 = base_outer_box(p)
    mid = (X0 + X1) / 2

    def ok(db, dt, side):
        box = (X0 - db, X1 + dt, Y0, Y1, Z0, Z1)
        poly, _ = outline_pts(p, box, 90)
        for pts, clr in footprints(p):
            sel = [q for q in pts if (q[0] < mid) == (side == 'bottom')]
            if not sel:
                continue
            # the flat USB-C end wall is end_wall thick (x under box[0] + wall + 0.3), the rest is wall
            w = np.array([end_wall(p) if (side == 'bottom' and q[0] < box[0] + p.wall + 0.3) else p.wall for q in sel])
            if (_inside_margin(poly, sel) - w - clr).min() < -1e-3:
                return False
        return True
    res = {}
    for side in ('bottom', 'top'):
        lo, hi = 0.0, 40.0
        if ok(0.0, 0.0, side):
            res[side] = 0.0
            continue
        for _ in range(40):
            m = (lo + hi) / 2
            if ok(m if side == 'bottom' else 40, m if side == 'top' else 40, side):
                hi = m
            else:
                lo = m
        res[side] = hi
    # the USB-C end must not grow: its outer face is placed on the receptacle mouth (usb_recess)
    assert res['bottom'] < 0.02, (f'the board does not fit the USB-C end corners (needs {res["bottom"]:.2f} mm more): '
                                  'lower g2_req_bottom')
    box = (X0 - res['bottom'], X1 + res['top'] + p.len_extra, Y0, Y1, Z0, Z1)
    _GROW[key] = box
    return box


# ---------------------------------------------------------------- shape
def _halfspace_above(origin, normal, size=600.0, h=200.0):
    n = cq.Vector(*normal).normalized()
    xd = cq.Vector(0, 0, 1).cross(n)
    if xd.Length < 1e-6:
        xd = cq.Vector(1, 0, 0)
    pl = cq.Plane(origin=cq.Vector(*origin), xDir=xd.normalized(), normal=n)
    return cq.Workplane(pl).rect(size, size).extrude(h)


def diamond_params(p: P, box):
    """The front lattice (owner sketch): a centre diamond (zone 2) and four diamonds of the same size
    sharing its edges (zone 1). Sized so the outer diamonds reach lattice_fill of the faceted panel."""
    X0, X1, Y0, Y1, Z0, Z1 = box
    b = p.lattice_fill_w * ((Z1 - Z0) / 2 - p.rim_w) / 2
    a = p.lattice_fill_h * ((X1 - X0) / 2 - p.rim_w) / 2
    return dict(xc=(X0 + X1) / 2, zc=(Z0 + Z1) / 2, a=a, b=b)


def zone_of(p: P, box, x, z):
    d = diamond_params(p, box)
    u, v = z - d['zc'], x - d['xc']
    s1, s2 = abs(u / d['b'] + v / d['a']), abs(u / d['b'] - v / d['a'])
    if s1 < 1 and s2 < 1:
        return 2
    if (s1 < 1 and s2 < 3) or (s2 < 1 and s1 < 3):
        return 1
    return 3


def _diamond(d, cu, cv, y0, y1):
    """Prism over a lattice diamond centred at (u, v) = (cu, cv), half-axes a (x) and b (z)."""
    xc, zc, a, b = d['xc'] + cv, d['zc'] + cu, d['a'], d['b']
    pl = cq.Plane(origin=(0, y0, 0), xDir=(1, 0, 0), normal=(0, 1, 0))   # local (x, -z)
    pts = [(xc + a, -zc), (xc, -(zc + b)), (xc - a, -zc), (xc, -(zc - b))]
    return cq.Workplane(pl).polyline(pts).close().extrude(y1 - y0)


def facet_panel(p: P, box):
    """Front panel with the reference's X facets: a flat centre diamond, planar facets
    falling toward the rim; the creases are the four lines through the diamond's sides."""
    X0, X1, Y0, Y1, Z0, Z1 = box
    d = diamond_params(p, box)
    xc, zc, a, b = d['xc'], d['zc'], d['a'], d['b']
    rim = Y1

    def T(u, v):
        s1, s2 = u / b + v / a, u / b - v / a
        return max(0.0, abs(s1) - 1) + max(0.0, abs(s2) - 1)
    poly, _ = outline_pts(p, box, 90)
    ctr = np.array([(X0 + X1) / 2, (Z0 + Z1) / 2])
    tmax = 0.0
    for q in np.array(poly):      # panel outline ~ outline pulled in by rim_w toward the centre
        dd = q - ctr
        qq = q - dd / np.linalg.norm(dd) * p.rim_w
        tmax = max(tmax, T(qq[1] - zc, qq[0] - xc))
    norm = math.sqrt(1 / a ** 2 + 1 / b ** 2)
    k = math.tan(math.radians(p.facet_angle)) / norm          # height per unit of the s coordinates
    crown_full = k * tmax + p.facet_min
    capped = 0 < p.crown < crown_full
    crown = p.crown if capped else crown_full
    top = rim + crown
    panel = profile(p, box, rim - 0.5).offset2D(-p.rim_w).extrude(0.5 + crown)
    for c1 in (0, 1, -1):
        for c2 in (0, 1, -1):
            if c1 == 0 and c2 == 0:
                continue
            du = k * (c1 / b + c2 / b)
            dv = k * (c1 / a - c2 / a)
            const = top + k * (abs(c1) + abs(c2))
            panel = panel.cut(_halfspace_above((xc, const, zc), (dv, 1.0, du)))
    if p.crown_style == 'pillow':  # a lofted dome: the panel outline scaled in step by step (same topology), rising as
        n_ = 10                     # a quarter sine: steep at the rim, flat on top
        base_w = profile(p, box, rim).offset2D(-p.rim_w).vals()[0]
        bb0 = base_w.BoundingBox()
        cxp, czp = (bb0.xmin + bb0.xmax) / 2, (bb0.zmin + bb0.zmax) / 2
        Lx, Lz = bb0.xlen, bb0.zlen
        dmax = Lz / 2 - 4.0                                 # the top keeps an 8 mm wide flat oval
        ws = []
        for i in range(n_ + 1):
            t = i / n_
            dd = dmax * (1 - math.cos(t * math.pi / 2)) if i < n_ else dmax
            hh = crown * math.sin(t * math.pi / 2)
            m = cq.Matrix([[(Lx - 2 * dd) / Lx, 0, 0, cxp * (1 - (Lx - 2 * dd) / Lx)],
                           [0, 1, 0, hh],
                           [0, 0, (Lz - 2 * dd) / Lz, czp * (1 - (Lz - 2 * dd) / Lz)]])
            ws.append(base_w.transformGeometry(m))
        dome = cq.Workplane().add(cq.Solid.makeLoft(ws, ruled=False))
        top_cap = cq.Workplane().add(cq.Solid.extrudeLinear(ws[-1], [], cq.Vector(0, 0.001, 0)))
        panel = profile(p, box, rim - 0.5).offset2D(-p.rim_w).extrude(0.5 + 0.001).union(dome)
    if p.crease_r > 0 and p.crown_style != 'pillow':
        panel = _round_creases(panel, p.crease_r)
    if capped:      # facets stop where they reach the rim + facet_min; the outer field stays flat there
        panel = panel.union(profile(p, box, rim - 0.5).offset2D(-p.rim_w).extrude(0.5 + p.facet_min))
    d.update(k=k, tmax=tmax, top=top, crown=crown, crown_full=crown_full, capped=capped,
             arm_deg=math.degrees(math.atan(k * norm)), corner_deg=math.degrees(math.atan(2 * k / b)),
             max_slope_deg=math.degrees(math.atan(2 * k / b)))
    return panel, d


def _round_creases(panel, r):
    """Fillet every edge between two upward faces of the faceted panel (the creases): each layer contour then
    turns smoothly instead of printing a sharp ring at every crease (#14C)."""
    from OCP.TopExp import TopExp
    from OCP.TopTools import TopTools_IndexedDataMapOfShapeListOfShape
    from OCP.TopAbs import TopAbs_EDGE, TopAbs_FACE
    from OCP.TopoDS import TopoDS
    solid = panel.val()
    m = TopTools_IndexedDataMapOfShapeListOfShape()
    TopExp.MapShapesAndAncestors_s(solid.wrapped, TopAbs_EDGE, TopAbs_FACE, m)
    edges = []
    for i in range(1, m.Extent() + 1):
        fs = [cq.Face(TopoDS.Face_s(f)) for f in m.FindFromIndex(i)]
        if len(fs) == 2 and all(f.normalAt().y > 0.5 for f in fs):
            n0, n1 = fs[0].normalAt(), fs[1].normalAt()
            if n0.dot(n1) < 0.99999:
                edges.append(cq.Edge(m.FindKey(i)))
    if not edges:
        return panel
    return cq.Workplane().add(solid.fillet(r, edges))


def crown_coupon(p: P, x=(117.76, 146.76), z_half=10.5, height=4.5, label=None):
    """#14: a patch of the cover's crown (the owner's cover top at the USB end, with the LED land, a diamond corner
    and two creases), solid under the crown down to a flat base: the slicer fills it with sparse infill under the top
    shells, as the real crown. label: cut 0.5 into the base (the bed face), read from below."""
    body, info = outer_body(p)
    X0, X1, Y0, Y1, Z0, Z1 = info['box']
    top = info['facets']['top']
    zc = (Z0 + Z1) / 2
    y0 = top - height
    c = body.intersect(_box(x[0], x[1], y0, top + 1, zc - z_half, zc + z_half))
    if p.led_land:
        Ld = MEASURED['xiao_rgb_led']
        c = c.cut(_cyl(sum(Ld['x']) / 2, sum(Ld['z']) / 2, p.led_land / 2, Y1, Y1 + 10))
    if label:
        t = (cq.Workplane(cq.Plane(origin=((x[0] + x[1]) / 2, y0 - 0.01, zc), xDir=(0, 0, -1), normal=(0, -1, 0)))
             .text(label, 7.0, -0.51, halign='center', valign='center', kind='bold'))
        c = c.cut(t)
    return c, dict(y0=round(y0, 2), rim=Y1, top=round(top, 2), crown=round(top - Y1, 2), base=round(Y1 - y0, 2))


def crown_section(p: P, half=5.0, label=None, depth=1.2):
    """#16: a full-width slice (x = the diamond centre +- half) of the crown down to depth under the rim, solid; the
    slicer fills it like the real crown. label: cut 0.5 into the base (the bed face)."""
    body, info = outer_body(p)
    X0, X1, Y0, Y1, Z0, Z1 = info['box']
    top = info['facets']['top']
    xc = info['facets']['xc']
    zc = (Z0 + Z1) / 2
    y0 = Y1 - depth
    c = body.intersect(_box(xc - half, xc + half, y0, top + 1, Z0 - 1, Z1 + 1))
    if label:
        t = (cq.Workplane(cq.Plane(origin=(xc, y0 - 0.01, zc), xDir=(0, 0, -1), normal=(0, -1, 0)))
             .text(label, 6.0, -0.51, halign='center', valign='center', kind='bold'))
        c = c.cut(t)
    return c, dict(top=round(top, 2), crown=round(top - Y1, 2), base=depth, width=round(Z1 - Z0, 2), length=2 * half)


def dowel_sprue(p: P, n_long, n_short, pitch=5.0, labels=('L', 'S'), flats=None):
    """#18.1c: the dowels standing in two rows on one carrier bar (print frame, z up, the bar flat on the bed): the long
    row on one side, the short row on the other, each dowel's D-flat facing the bar and joined to it at its base by a
    0.6 x 0.4 tab (twist off: the nub stays on the flat and the end chamfer, off the working diameter). 'L' / 'S' raised
    on the bar. Returns (sprue, pusher): the pusher is a Ø12 x 40 handle with a Ø3.4 x pusher_cups[0] cup on its top, palm end
    down (a second entry: a second cup in the palm end, marked by a V ring groove 4.6 mm up from it)."""
    d = p.peg_d
    fl_l, fl_s = flats if flats is not None else (p.dowel_flat, p.dowel_flat)
    _, peg_l, _ = peg_coupon(clearances=(p.peg_clr,), d=d, peg_len=2 * p.peg_depth, flat=fl_l)
    _, peg_s, _ = peg_coupon(clearances=(p.peg_clr,), d=d, peg_len=p.short_len, flat=fl_s)
    bw, bt, gap = 3.0, 1.0, 1.0            # bar width, thickness, bar edge to the dowel's surface
    n_max = max(n_long, n_short)
    L = (n_max - 1) * pitch + d + 8.0
    sprue = _box(-6.0, L - 6.0, -bw / 2, bw / 2, 0, bt).translate((0, 0, 0))      # (x, y, z) here: _box is x, y, z
    yc = bw / 2 + gap + d / 2
    for label, peg, n, side, fl in ((labels[0], peg_l, n_long, 1, fl_l), (labels[1], peg_s, n_short, -1, fl_s)):
        pg = peg.rotate((0, 0, 0), (0, 0, 1), -90 if side > 0 else 90)       # the flat (+x) toward the bar
        for i in range(n):
            x = i * pitch
            sprue = sprue.union(pg.translate((x, side * yc, 0)))
            if fl > 0:
                y_bar, y_peg = side * bw / 2, side * (yc - d / 2 + fl + 0.2)   # the tab reaches 0.2 into the dowel's flat
                sprue = sprue.union(_box(x - 0.3, x + 0.3, *sorted((y_bar - side * 0.2, y_peg)), 0, 0.4))
            else:     # round (#18.1e): a first-layer tab into the 0.3 end chamfer only: the nub stays inside the Ø d envelope
                y_bar, y_peg = side * bw / 2, side * (yc - d / 2 + 0.3 + 0.2)
                sprue = sprue.union(_box(x - 0.3, x + 0.3, *sorted((y_bar - side * 0.2, y_peg)), 0, 0.2))
        t = (cq.Workplane(cq.Plane(origin=(-4.5, side * 0.0, bt - 0.01), xDir=(1, 0, 0), normal=(0, 0, 1)))
             .text(label, 2.4, 0.6, halign='center', valign='center', kind='bold'))
        sprue = sprue.union(t.translate((0 if side > 0 else L - 7.5, 0, 0)))
    pusher = cq.Workplane().circle(6.0).extrude(40.0).faces('>Z or <Z').edges().chamfer(0.6)
    cups = p.pusher_cups
    pusher = pusher.cut(cq.Workplane().circle(3.4 / 2).extrude(cups[0]).translate((0, 0, 40.0 - cups[0])))
    if len(cups) > 1:             # #18.1d: a second cup at the other end (its own protrusion), marked by a ring groove
        pusher = pusher.cut(cq.Workplane().circle(3.4 / 2).extrude(cups[1]).translate((0, 0, -0.01)))
        ring = (cq.Workplane('XZ').polyline([(5.4, 4.6), (6.6, 3.4), (6.6, 5.8)]).close()
                .revolve(360, (0, 0, 0), (0, 1, 0)))       # a V groove, 45 degree flanks (no overhang)
        pusher = pusher.cut(ring)
    return sprue, pusher


def fit_coupon(p: P, tips=(3.225, 3.175, 3.125), frame_holes=((2.44, 'neck'), (2.44, 'floor'), (3.24, 'neck')),
               face_depth=2.6, stop=1.2):
    """#18.1e fit coupon (lead, 2026-09-30): the face-hole and frame-hole geometry of p on two small strips, printed in
    their cover orientation (hole mouths on the bed), so the fit is felt in minutes before a 2 h cover. Face strip:
    ribbed holes (bore p.peg_ribs[0], 3 ribs p.peg_ribs[2] wide) with rib crests `tips` (18.1c's 3.225, +0.05, +0.10),
    `face_depth` deep, the lead / rib start of p. Frame strip: one block per `frame_holes` entry (depth, 'neck' | 'floor'),
    each exactly depth + `stop` tall like a cover post: a Ø(peg_d + 2 peg_clr) hole that ends on a `stop` thick ring round
    a p.frame_neck through neck, or on a `stop` thick solid floor. The n-th hole of a strip has n dimples on top.
    Returns (face_strip, frame_strip, info), print frame (z up, on the bed at z 0)."""
    bore, _, rw, nr = p.peg_ribs
    lead = p.rib_lead if p.rib_lead is not None else p.peg_lead
    pitch, W = 8.0, 8.0
    def dimples(body, i, x, top):
        for k in range(i + 1):
            body = body.cut(cq.Workplane().add(cq.Solid.makeCylinder(0.5, 1.0, cq.Vector(x - (i * 1.4) / 2 + k * 1.4, 2.9, top - 0.4),
                                                                      cq.Vector(0, 0, 1))))
        return body
    L = pitch * len(tips) + 2.0
    H = face_depth + 0.8
    face = cq.Workplane().box(L, W, H, centered=(False, True, False)).edges('|Z').fillet(1.0)
    for i, tip in enumerate(tips):
        x = 1.0 + pitch * (i + 0.5)
        hole = cq.Workplane().add(cq.Solid.makeCylinder(bore / 2, face_depth + 0.01, cq.Vector(x, -1.0, -0.01), cq.Vector(0, 0, 1)))
        for j in range(nr):
            a = 2 * math.pi * j / nr + math.pi / 2
            rib = cq.Workplane().box(bore / 2 + 0.3 - tip / 2, rw, face_depth - lead + 0.02, centered=(False, True, False)) \
                .translate((tip / 2, 0, lead)).rotate((0, 0, 0), (0, 0, 1), math.degrees(a)).translate((x, -1.0, 0))
            hole = hole.cut(rib)
        hole = hole.union(cq.Workplane().add(cq.Solid.makeCone(bore / 2 + lead, bore / 2, lead, cq.Vector(x, -1.0, -0.01), cq.Vector(0, 0, 1))))
        face = dimples(face.cut(hole), i, x, H)
    rf = p.peg_d / 2 + p.peg_clr
    fl = p.frame_lead if p.frame_lead is not None else p.peg_lead
    neck = p.frame_neck or 1.6
    frame = None
    for i, (dpt, kind) in enumerate(frame_holes):
        x = 1.0 + pitch * (i + 0.5)
        Hf = dpt + stop
        blk = cq.Workplane().box(pitch + (1.0 if i in (0, len(frame_holes) - 1) else 0.02), W, Hf, centered=(False, True, False)) \
            .translate((x - pitch / 2 - (1.0 if i == 0 else 0.01), 0, 0))
        hole = cq.Workplane().add(cq.Solid.makeCylinder(rf, dpt + 0.01, cq.Vector(x, -1.0, -0.01), cq.Vector(0, 0, 1)))
        hole = hole.union(cq.Workplane().add(cq.Solid.makeCone(rf + fl, rf, fl, cq.Vector(x, -1.0, -0.01), cq.Vector(0, 0, 1))))
        if kind == 'neck':
            hole = hole.union(cq.Workplane().add(cq.Solid.makeCylinder(neck / 2, Hf + 1, cq.Vector(x, -1.0, dpt - 0.01), cq.Vector(0, 0, 1))))
        blk = dimples(blk.cut(hole), i, x, Hf)
        frame = blk if frame is None else frame.union(blk)
    frame = frame.edges('|Z').fillet(0.8)
    return face, frame, dict(tips=tips, face_depth=face_depth, frame_holes=frame_holes, neck=neck, stop=stop,
                             size=(L, W, H, max(d_ for d_, _ in frame_holes) + stop))


def test_joint(p: P, L=16.0, W=10.0, skin=0.8, label='ТЕСТ'):
    """One exact face / frame joint of p (lead, 2026-09-30: felt before the cover is assembled), each piece labelled on
    its top. Frame block: a Ø(peg_d + 2 peg_clr) hole p.peg_frame_d deep, its frame_lead cone, the Ø frame_neck through
    neck on a >= 1.28 ring. Face tab: the ribbed hole (p.peg_ribs, rib_lead) p.peg_face_d deep under `skin`. Print frame:
    hole mouths on the bed (z 0). Returns (frame_block, face_tab)."""
    bore, tip, rw, nr = p.peg_ribs
    lead = p.rib_lead if p.rib_lead is not None else p.peg_lead
    fl = p.frame_lead if p.frame_lead is not None else p.peg_lead
    hx, hy = 4.5, -1.6
    def label_on(body, top):
        t = (cq.Workplane(cq.Plane(origin=(L / 2 + 1.0, 2.7, top + 0.01), xDir=(1, 0, 0), normal=(0, 0, 1)))
             .text(label, 2.8, -0.45, halign='center', valign='center', kind='bold'))
        return body.cut(t)            # engraved: an embossed label left a one-cell island on a letter
    D = p.peg_frame_d
    Hf = round(D + 1.28, 2)
    rf = p.peg_d / 2 + p.peg_clr
    fb = cq.Workplane().box(L, W, Hf, centered=(False, True, False)).edges('|Z').fillet(1.0)
    hole = cq.Workplane().add(cq.Solid.makeCylinder(rf, D + 0.01, cq.Vector(hx, hy, -0.01), cq.Vector(0, 0, 1)))
    hole = hole.union(cq.Workplane().add(cq.Solid.makeCone(rf + fl, rf, fl, cq.Vector(hx, hy, -0.01), cq.Vector(0, 0, 1))))
    hole = hole.union(cq.Workplane().add(cq.Solid.makeCylinder((p.frame_neck or 1.6) / 2, Hf + 1, cq.Vector(hx, hy, D - 0.01),
                                                                cq.Vector(0, 0, 1))))
    fb = label_on(fb.cut(hole), Hf)
    Fd = p.peg_face_d
    Ht = round(Fd + skin, 2)
    ft = cq.Workplane().box(L, W, Ht, centered=(False, True, False)).edges('|Z').fillet(1.0)
    hole = cq.Workplane().add(cq.Solid.makeCylinder(bore / 2, Fd + 0.01, cq.Vector(hx, hy, -0.01), cq.Vector(0, 0, 1)))
    for j in range(nr):
        a = 2 * math.pi * j / nr + math.pi / 2
        rib = cq.Workplane().box(bore / 2 + 0.3 - tip / 2, rw, Fd - lead + 0.02, centered=(False, True, False)) \
            .translate((tip / 2, 0, lead)).rotate((0, 0, 0), (0, 0, 1), math.degrees(a)).translate((hx, hy, 0))
        hole = hole.cut(rib)
    hole = hole.union(cq.Workplane().add(cq.Solid.makeCone(bore / 2 + lead, bore / 2, lead, cq.Vector(hx, hy, -0.01), cq.Vector(0, 0, 1))))
    ft = label_on(ft.cut(hole), Ht)
    return fb, ft


def size_sprue(p: P, d, letter, n=10, pitch=5.0):
    """18.2-B (owner, 2026-10-03): n round dowels of diameter d standing in one row beside a carrier bar, each joined to
    it by a first-layer tab into the end chamfer (twist off, the nub stays off the working diameter), and a 7 x 7 tab at
    the bar's start with the size letter raised on it (S / M / L): a loose dowel is swapped for the next size up."""
    _, peg, _ = peg_coupon(clearances=(p.peg_clr,), d=d, peg_len=2 * p.peg_depth, flat=0.0)
    bw, bt, gap = 3.0, 1.0, 1.0
    L = (n - 1) * pitch + d / 2 + 1.0
    spr = _box(-1.0, L, -bw / 2, bw / 2, 0, bt).union(_box(-9.0, -1.0, -3.5, 3.5, 0, bt))
    yc = bw / 2 + gap + d / 2
    for i in range(n):
        x = i * pitch + d / 2
        spr = spr.union(peg.translate((x, yc, 0)))
        spr = spr.union(_box(x - 0.3, x + 0.3, bw / 2 - 0.2, yc - d / 2 + 0.5, 0, 0.2))
    t = (cq.Workplane(cq.Plane(origin=(-5.0, 0.0, bt - 0.01), xDir=(1, 0, 0), normal=(0, 0, 1)))
         .text(letter, 4.5, 0.6, halign='center', valign='center', kind='bold'))
    return spr.union(t)


def sml_rack(p: P, pitch_y=12.0):
    """18.2-B: the size sprues (p.sml_sprues) as one rack, one row per size, their label tabs joined by a spine."""
    if not p.sml_sprues:
        raise ValueError('sml_rack needs at least one (letter, diameter) in p.sml_sprues')
    rack = None
    n = len(p.sml_sprues)
    for i, (lt, dd) in enumerate(p.sml_sprues):
        row = size_sprue(p, dd, lt).translate((0, i * pitch_y, 0))
        rack = row if rack is None else rack.union(row)
    return rack.union(_box(-9.0, -7.0, -3.5, (n - 1) * pitch_y + 3.5, 0, 1.0))


def peg_coupon(number=15, clearances=(0.05, 0.10, 0.15), d=3.0, depth=3.0, peg_len=5.0, flat=0.3):
    """#15: the 10.3a/b dowel press fit. A block (print frame: z up) with a blind hole per clearance (diameter d + 2 c,
    0.3 lead-in at the mouth), labelled on top, and loose pegs d x peg_len printed standing (0.3 chamfers both ends, a
    0.3 D-flat along the length to vent the blind hole)."""
    n = len(clearances)
    pitch, W, H = 10.0, 12.0, depth + 1.2
    L = pitch * n + 6.0
    block = _box(0, L, -W / 2, W / 2, 0, H).edges('|Z').fillet(1.0)
    block = block.faces('<Z').edges().chamfer(0.3)
    txts = []
    for i, c in enumerate(clearances):
        x = 6.0 + pitch * i + 2.0
        r = d / 2 + c
        hole = cq.Workplane().add(cq.Solid.makeCylinder(r, depth + 0.01, cq.Vector(x, -1.5, H - depth), cq.Vector(0, 0, 1)))
        hole = hole.union(cq.Workplane().add(cq.Solid.makeCone(r, r + 0.3, 0.3, cq.Vector(x, -1.5, H - 0.3), cq.Vector(0, 0, 1))))
        block = block.cut(hole)
        txts.append(cq.Workplane(cq.Plane(origin=(x, 3.4, H - 0.5), xDir=(1, 0, 0), normal=(0, 0, 1)))
                    .text(f'.{round(c * 100):02d}', 3.2, 0.51, halign='center', valign='center', kind='bold'))
    txts.append(cq.Workplane(cq.Plane(origin=(3.0, 0, H - 0.5), xDir=(0, 1, 0), normal=(0, 0, 1)))
                .text(str(number), 3.5, 0.51, halign='center', valign='center', kind='bold'))
    for t in txts:
        block = block.cut(t)
    peg = (cq.Workplane().add(cq.Solid.makeCylinder(d / 2, peg_len, cq.Vector(0, 0, 0), cq.Vector(0, 0, 1)))
           .faces('>Z or <Z').edges().chamfer(0.3))
    if flat > 0:
        peg = peg.cut(_box(d / 2 - flat, d, -d, d, -1, peg_len + 1))    # a D-flat the whole length: the blind hole's air vents
    return block, peg, dict(holes=[round(d + 2 * c, 2) for c in clearances], depth=depth, peg=(d, peg_len), block=(L, W, H))


def loop_lug(p: P, box):
    X0, X1, Y0, Y1, Z0, Z1 = box
    zc, yc = (Z0 + Z1) / 2, (Y0 + Y1) / 2
    hr = p.loop_hole / 2
    hx = X1 + p.loop_gap + hr
    R = hr + p.loop_web
    w = max(p.loop_w, 2 * R)
    base = X1 - 6.0
    lug = (cq.Workplane().box(hx - base, p.loop_t, w).translate(((hx + base) / 2, yc, zc))
           .union(cq.Workplane().cylinder(p.loop_t, w / 2, direct=(0, 1, 0)).translate((hx, yc, zc))))
    lug = lug.cut(cq.Workplane().cylinder(p.loop_t * 3, hr, direct=(0, 1, 0)).translate((hx, yc, zc)))
    try:                # the bed-side edges stay square when the lug has fins (a fillet there prints as a 90 deg lip)
        lug = lug.faces('>Y' if p.loop_gusset else '>Y or <Y').edges('not %LINE').fillet(0.6)
    except Exception:
        pass
    return lug, dict(hole_x=hx, hole_r=hr, web=R - hr, end_x=hx + w / 2, t=p.loop_t,
                     section_mm2=p.loop_web * p.loop_t)


def outer_body(p: P):
    box = outer_box(p)
    X0, X1, Y0, Y1, Z0, Z1 = box
    body = profile(p, box, Y0).extrude(Y1 - Y0)
    body = (body.faces('>Y').edges().chamfer(p.front_chamfer) if p.flat_top
            else body.faces('>Y').edges().fillet(p.fillet_front))
    body = (body.faces('<Y').edges().chamfer(p.back_chamfer) if p.back_chamfer > 0
            else body.faces('<Y').edges().fillet(p.fillet_back))
    panel, fac = facet_panel(p, box)
    body = body.union(panel)
    return body, dict(box=box, facets=fac, corner_extent=corner_extent(p, Z1 - Z0),
                      corner_extent_bottom=corner_extent(p, Z1 - Z0, 'bottom'))


def _wall_loft(p: P, box, ya, da, yb, db):
    """Ruled loft between the outline offset inward by da at y = ya and by db at y = yb (a 45 degree skirt when
    |da - db| = |yb - ya|)."""
    wa = profile(p, box, ya).offset2D(-da).vals()[0]
    wb = profile(p, box, yb).offset2D(-db).vals()[0]
    return cq.Workplane().add(cq.Solid.makeLoft([wa, wb], ruled=True))


def tab_geometry(p: P):
    """Numbers of the D1 flex tab in the +z wall."""
    M = MEASURED['button_d1']
    x0, x1, y0, y1, z0, z1 = packing(p)['cavity']
    xc = sum(M['x']) / 2; yc = sum(M['y']) / 2
    hx1 = xc + p.tab_free
    hx0 = hx1 - p.tab_len
    zin = z1                          # inner face of the +z wall
    zout = z1 + p.wall
    ztongue = zout - min(p.tab_t, p.wall)   # tongue inner face (thinned from inside when the wall is thicker)
    ym = yc + p.tab_dy
    # the slit above the tongue: vertical gap sv (its width across the 45 degree roof is tab_slit), rising by the
    # tongue thickness from the outer face to the tongue's inner face (roof = tan(tab_roof) per mm inward)
    roof = math.tan(math.radians(p.tab_roof)) if p.tab_roof > 0 else 0.0
    sv = p.tab_slit / math.cos(math.radians(p.tab_roof)) if p.tab_roof > 0 else p.tab_slit
    return dict(xc=xc, yc=yc, hx0=hx0, hx1=hx1, ya=ym - p.tab_h / 2, yb=ym + p.tab_h / 2,
                zin=zin, zout=zout, ztongue=ztongue, nub_z0=M['z_max'] + p.nub_gap, roof=roof, sv=sv,
                top_slit_max=ym + p.tab_h / 2 + sv + roof * (zout - ztongue))


def tab_solids(p: P, g, z_in=None):
    """(tongue, grown): the tongue's envelope and the same grown by tab_slit (so grown - tongue = the slits).
    Slit above the tongue (print Z): a 45 degree roof, not a flat 14 mm bridge. At the outer face the gap is
    yb..yb + sv (sv = tab_slit / cos 45); it rises going inward, so the wall above grows over it at 45 degrees and the
    tongue's top edge leans back on its inner side. The free end's top corner is cut at 45 degrees (tab_end_chamfer)
    and the slit follows it, so the wall past the free end overhangs at 45 degrees too."""
    zo, yb, ya, sv, rf, s, ce = g['zout'], g['yb'], g['ya'], g['sv'], g['roof'], p.tab_slit, p.tab_end_chamfer
    zi = (g['ztongue'] - 0.3) if z_in is None else z_in
    ze = zo + 1.5

    def env(dy0, dy1, x1):
        return _prism_yz([(ya - dy0, ze), (yb + dy1, ze), (yb + dy1, zo), (yb + dy1 + rf * (zo - zi), zi),
                          (ya - dy0, zi)], g['hx0'], x1)
    tongue, grown = env(0.0, 0.0, g['hx1']), env(s, sv, g['hx1'] + s)
    if p.tab_square:              # #9 / audit: a flat top edge, so the tongue does not end in a one-line island
        tongue = _prism_yz([(ya, ze), (yb, ze), (yb, zi), (ya, zi)], g['hx0'], g['hx1'])
        ce = 0
    if ce > 0:
        a = g['hx1'] + yb - ce                   # chamfer plane x + y = a
        pl = cq.Plane(origin=(0, 0, zi - 1), xDir=(1, 0, 0), normal=(0, 0, 1))
        top = yb + sv + rf * (zo - zi) + 2

        def past(c):                             # everything with x + y > c near the free end
            return cq.Workplane(pl).polyline([(c - top, top), (g['hx1'] + 5, top), (g['hx1'] + 5, c - g['hx1'] - 5),
                                              ]).close().extrude(ze - zi + 2)
        tongue = tongue.cut(past(a))
        grown = grown.cut(past(a + s * math.sqrt(2)))
    return tongue, grown


def nub_span(p: P, g):
    """(y0, y1) of the nub: nub_h around the actuator centre, or (nub_h 0) a rib over the tongue height."""
    if p.nub_h > 0:
        return g['yc'] - p.nub_h / 2, g['yc'] + p.nub_h / 2
    return g['ya'] + p.nub_rib_margin, g['yb'] - p.nub_rib_margin


def tab_mechanics(p: P = None):
    """Cantilever flexure: hinge at hx0, load at the nub (D1 centre)."""
    p = p or P()
    g = tab_geometry(p)
    M = MEASURED['button_d1']
    L = g['xc'] - g['hx0']
    I = p.tab_h * p.tab_t ** 3 / 12
    E = DATASHEET['pla_E_xy']
    k = 3 * E * I / L ** 3                         # N/mm
    protrusion = M['z_max'] - M['body_z']          # 1.00 mm of actuator out of the switch body
    typ_travel = 0.25                              # typical side tact switch travel; D1 part number unknown
    stroke = p.nub_gap + typ_travel
    bottom = p.nub_gap + protrusion                # nub reaches the switch body: hard stop
    strain = lambda d: 3 * d * p.tab_t / (2 * L ** 2) * 100
    return dict(L=L, I=I, E=E, k=k, gap=p.nub_gap, protrusion=protrusion, typ_travel=typ_travel,
                stroke=stroke, flex_force=k * stroke, strain_stroke=strain(stroke),
                max_defl=bottom, strain_max=strain(bottom), elong_break=DATASHEET['pla_elong_xy'],
                nub_len=g['ztongue'] - g['nub_z0'], wall=p.wall, tab_t=p.tab_t, slit=p.tab_slit, tab_len=p.tab_len,
                roof_deg=p.tab_roof, end_chamfer=p.tab_end_chamfer)


def _cyl(x, z, r, y0, y1):
    return cq.Workplane().cylinder(y1 - y0, r, direct=(0, 1, 0)).translate((x, (y0 + y1) / 2, z))


def _hexprism(x, z, af, y0, y1):
    return (cq.Workplane(cq.Plane(origin=(x, y0, z), xDir=(1, 0, 0), normal=(0, 1, 0)))
            .polygon(6, af / math.cos(math.pi / 6)).extrude(y1 - y0))


def _box(x0, x1, y0, y1, z0, z1):
    return cq.Workplane().box(x1 - x0, y1 - y0, z1 - z0).translate(((x0 + x1) / 2, (y0 + y1) / 2, (z0 + z1) / 2))


def fastening(p: P, box):
    """Screw stack per board hole: head seat, tip, nut.
    'front': screws enter from the front, nuts in the back. 'back' (A): countersunk heads flush with the
    back face, nuts in the cover pillars. 'snap' (B): no screws."""
    Y0 = box[2]
    if p.closure == 'back':
        tip = Y0 + p.back_screw_len
        n1 = tip - p.nut_tip_past
        return dict(closure='back', seat=Y0, tip=tip, nut=(n1 - p.nut_m, n1), holes=MEASURED['holes'])
    if p.closure == 'snap':
        return dict(closure='snap', seat=None, tip=None, nut=None, holes=MEASURED['holes'])
    tip = Y0 + p.screw_tip
    seat = tip + p.screw_len
    return dict(closure='front', seat=seat, tip=tip, nut=(Y0, Y0 + p.nut_m), holes=MEASURED['holes'])


def _cone(x, z, d0, d1, y0, y1):
    """Cone along +y from diameter d0 at y0 to d1 at y1."""
    return cq.Workplane().add(cq.Solid.makeCone(d0 / 2, d1 / 2, y1 - y0, cq.Vector(x, y0, z), cq.Vector(0, 1, 0)))


def _prism_yz(pts, x0, x1):
    """Prism along x over a polygon given as (y, z) points."""
    pl = cq.Plane(origin=(x0, 0, 0), xDir=(0, 1, 0), normal=(1, 0, 0))     # local x = y, local y = z
    return cq.Workplane(pl).polyline(pts).close().extrude(x1 - x0)


def latches(p: P):
    """B: one dict per latch. s = +1 on the +z wall, -1 on the -z wall; the tongue's hinge points to the
    middle of the straight side, the free end (with the groove) to the end of the case."""
    x0, x1, y0, y1, z0, z1 = packing(p)['cavity']
    mid = sum(p.latch_x) / 2
    out = []
    tt = max(p.latch_t, p.wall)
    for s, zw in ((1, z1), (-1, z0)):
        for xb in p.latch_x:
            hd = 1 if xb < mid else -1
            zout = zw + s * p.wall
            out.append(dict(s=s, zin=zout - s * tt, zwall=zw, zout=zout, xb=xb, hinge=xb + hd * p.latch_len,
                            free=xb - hd * (p.latch_bump_w / 2 + 1.0), hd=hd))
    return out


def snap_features(p: P, tray, cover, split, box, usb):
    """B: per latch, an L-shaped slit frees a tongue in the long wall (hinge toward the middle, free end toward
    the case end, top edge = wall top under the cover rim); a groove in the tongue's inner face near its free
    end; on the cover, a catch block under the front plate with a bump that snaps into the groove.
    Both 45 degree retention faces and the 30 degree lead-in print without support. Plus a pry notch in the
    bottom end beside USB-C."""
    X0 = box[0]
    x0 = packing(p)['cavity'][0]
    sl, e, c = p.tab_slit, p.latch_e, p.print_clr
    tl, tr = math.tan(math.radians(p.latch_lead_deg)), math.tan(math.radians(p.latch_ret_deg))
    dz = c + e
    dl, dr, flat = dz / tl, dz / tr, 0.4
    yb0 = split - p.latch_catch_h + 0.3
    yr0 = yb0 + dl + flat
    for L in latches(p):
        s, zin, zout, xb, hd = L['s'], L['zin'], L['zout'], L['xb'], L['hd']
        if abs(zin - L['zwall']) > 1e-6:
            # a wall thinner than latch_t: a pad inside the wall over the tongue and its slits, and the cover's lip
            # (which runs just inside the wall) notched over it; the catch block below takes the lip's place there
            xa_, xb_ = sorted((L['free'] - hd * (sl + 1.5), L['hinge'] + hd * 1.5))
            pa, pb = sorted((L['zwall'] + s * 0.1, zin))
            tray = tray.union(_box(xa_, xb_, p.latch_y0 - sl - 0.6, split, pa, pb))
            ca_, cb_ = sorted((L['zwall'] + s * 0.1, zin - s * c))
            cover = cover.cut(_box(xa_ - 0.3, xb_ + 0.3, split - p.lip_h - 0.5, split + 0.01, ca_, cb_))
        za, zb = sorted((zin - s * 1.0, zout + s * 1.5))
        fa, fb = sorted((L['free'], L['free'] - hd * sl))
        tray = tray.cut(_box(fa, fb, p.latch_y0 - sl, split + 0.1, za, zb))                    # end slit
        ba, bb = sorted((L['free'] - hd * sl, L['hinge']))
        tray = tray.cut(_box(ba, bb, p.latch_y0 - sl, p.latch_y0, za, zb))                     # bottom slit
        hw = p.latch_bump_w / 2
        # lead-in chamfer on the tongue's inner top edge
        tray = tray.cut(_prism_yz([(split + 0.05, zin - s * 0.05), (split - 0.8, zin - s * 0.05),
                                   (split + 0.05, zin + s * 0.8)], xb - hw - 0.3, xb + hw + 0.3))
        # groove: the bump's shape, 0.15 lower on the lead side, 0.05 higher on the retention side, 0.1 deeper
        zf, zt = zin - s * c, zin + s * e
        zt2 = zt + s * 0.1
        tray = tray.cut(_prism_yz([(yb0 - 0.15, zf), (yb0 - 0.15 + (dz + 0.1) / tl, zt2),
                                   (yr0 + 0.05 - 0.1 / tr, zt2), (yr0 + 0.05 + dr, zf)], xb - hw - 0.2, xb + hw + 0.2))
        # catch block + bump on the cover
        ca, cb = sorted((zin - s * (c + p.latch_catch_t), zf))
        cover = cover.union(_box(xb - hw - 0.5, xb + hw + 0.5, split - p.latch_catch_h, split + 0.5, ca, cb))
        cover = cover.union(_prism_yz([(yb0, zf - s * 0.3), (yb0, zf), (yb0 + dl, zt), (yr0, zt), (yr0 + dr, zf),
                                       (yr0 + dr, zf - s * 0.3)], xb - hw, xb + hw))
    # pry notch in the bottom end, beside the USB-C opening
    w, d, pz0 = p.pry_notch
    uz, uw = usb
    assert pz0 > uz + uw / 2 + p.usb_chamfer + 0.5, 'pry notch runs into the USB-C lead-in'
    tray = tray.cut(_box(X0 - 1.0, x0 + 3.0, split - d, split + 0.1, pz0, pz0 + w))
    return tray, cover


def fit_check(p: P, info):
    """Board-referenced openings against the real parts (MEASURED), as margins in mm; negative = the part is covered.
    usb: receptacle shell at its mouth inside the window (4 sides); switch: the lever over its full travel inside the
    slot; d1: the nub covers the actuator in y, and the rest gap; led: the LED die inside the skin spot; tab_wall: solid
    wall between the button slits and the back fillet / the parting line."""
    M = MEASURED
    out = {}
    uw, uh, uy, uz = usb_window_rect(p)
    sh = M['usb_c_shell']
    out['usb'] = dict(y_low=round(sh['y'][0] - (uy - uh / 2), 3), y_high=round(uy + uh / 2 - sh['y'][1], 3),
                      y_low_at_min_lift=round(sh['y'][0] - XIAO_DY_TOL - (uy - uh / 2), 3),
                      cover_over_at_max_lift=round(packing(p)['cavity'][3] - (M['xiao_top_y'] + XIAO_DY_UP), 3),
                      z_low=round(sh['z'][0] - (uz - uw / 2), 3), z_high=round(uz + uw / 2 - sh['z'][1], 3))
    sl, ss = M['switch_lever'], info['switch_slot']
    out['switch'] = dict(x_on=round(sl['x'][0] - sl['travel'] - ss['x'][0], 3), x_off=round(ss['x'][1] - sl['x'][1], 3),
                         tip_under_outer=round(sl['z_min'] - info['box'][4] - (p.switch_scoop or 0.0), 3),
                         y_low=round(sl['y'][0] - ss['y'][0], 3), y_high=round(ss['y'][1] - sl['y'][1], 3))
    d1, g = M['button_d1'], info['tab']
    ny0, ny1 = nub_span(p, g)
    nx0, nx1 = g['xc'] - p.nub_w / 2, g['xc'] + p.nub_w / 2
    out['d1'] = dict(nub_covers_y_low=round(d1['y'][0] - ny0, 3), nub_covers_y_high=round(ny1 - d1['y'][1], 3),
                     nub_on_actuator_x=round(min(nx0 - d1['x'][0], d1['x'][1] - nx1), 3),
                     rest_gap=round(g['nub_z0'] - d1['z_max'], 3))
    L = M['xiao_rgb_led']
    lx, lz = info['led']['x'], info['led']['z']
    far = max(math.hypot(x - lx, z - lz) for x in L['x'] for z in L['z'])
    out['led'] = dict(die_inside_spot=round(p.led_d / 2 - far, 3))
    Y0, split = info['box'][2], info['split']
    out['tab_wall'] = dict(below=round(g['ya'] - p.tab_slit - (Y0 + (p.back_chamfer or p.fillet_back)), 3),
                           above=round(split - g['top_slit_max'], 3))
    worst = min(v for d in out.values() for v in d.values())
    out['ok'] = bool(min(min(out['usb'].values()), min(out['switch'].values()), out['d1']['nub_covers_y_low'],
                         out['d1']['nub_covers_y_high'], out['led']['die_inside_spot']) >= 0.2
                     and min(out['tab_wall'].values()) >= 1.5 and out['d1']['rest_gap'] > 0)
    out['worst'] = round(worst, 3)
    return out
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
