railyai/raily-pin/firmware/RailyPinsP1/counter_select.h

#ifndef RAILY_COUNTER_SELECT_H
#define RAILY_COUNTER_SELECT_H

// Pure record layout + restore-selection logic for the persisted button-event
// counter. Kept free of Arduino/InternalFS dependencies so the exact same
// decision the firmware makes at boot can be unit-tested on the host
// (firmware/tests/test_counter_select.cpp).

#include <stdint.h>

// Two generation-numbered, checksummed slots: a torn write can only ever
// damage the slot being written, and restore picks the newest VALID record
// instead of trusting whatever four bytes happened to survive.
struct CounterRecord {
  uint32_t magic;     // COUNTER_MAGIC — identifies this record format
  uint32_t counter;
  uint32_t seq;       // generation — disambiguates the newest valid slot
  uint32_t checksum;  // magic ^ counter ^ seq ^ COUNTER_CHECKSUM_MASK
} __attribute__((packed));
static_assert(sizeof(CounterRecord) == 16, "on-disk counter record layout changed");
static const uint32_t COUNTER_MAGIC = 0x52314354;  // "R1CT"
// Integrity mask, NOT a secret: it detects flash corruption, it does not
// authenticate the record — the server's monotone watermark is the actual
// replay defense.
static const uint32_t COUNTER_CHECKSUM_MASK = 0x9E3779B9;
// A torn slot record is untrusted — bound any unvalidated candidate by the
// last persisted legacy counter plus slack for legacy-write failures, so
// relocated garbage cannot push the counter to an absurd range.
static const uint32_t COUNTER_SALVAGE_SLACK = 16;
// Never adopt a counter within this distance of the u32 ceiling: a few more
// presses would wrap to 0 and land permanently under the server watermark.
static const uint32_t COUNTER_WRAP_HEADROOM = 1024;
static const uint32_t COUNTER_ADOPT_MAX = 0xFFFFFFFFu - COUNTER_WRAP_HEADROOM;
// Legacy is dual-written right after a slot commit, so in healthy operation
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
